LibrEduc/RobotBlocs/Projets_complets/v2020-2021/RobotTraceur1 - Pierre Gautier  - Simon Le Moal - Armand Racine  - Gwen Berrou/brainstorming/Croquis Option 2.pdf

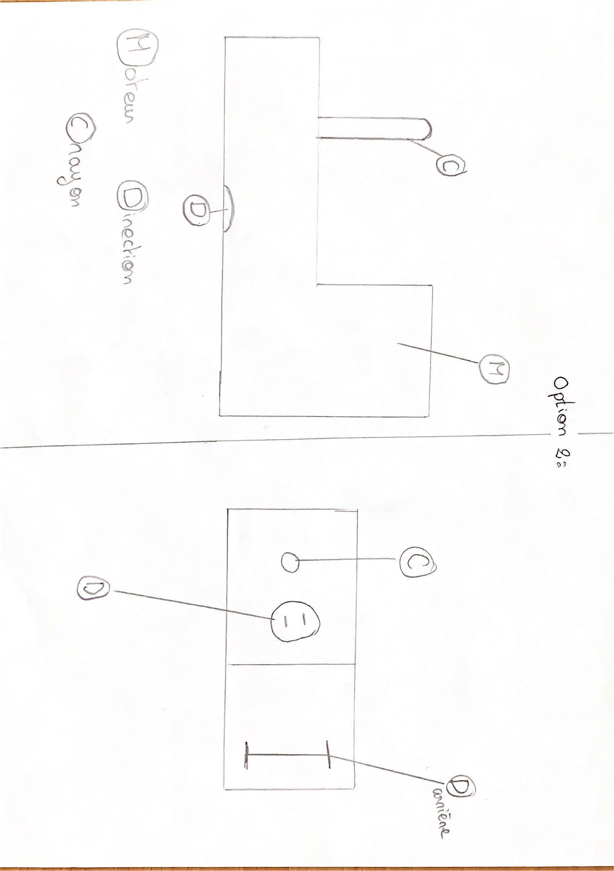
[picture p103: page 1]
