LibrEduc/RobotBlocs/Besoin_prof/SIN_ITEC_Livet_RobotBlocs_2020_uc.jpg

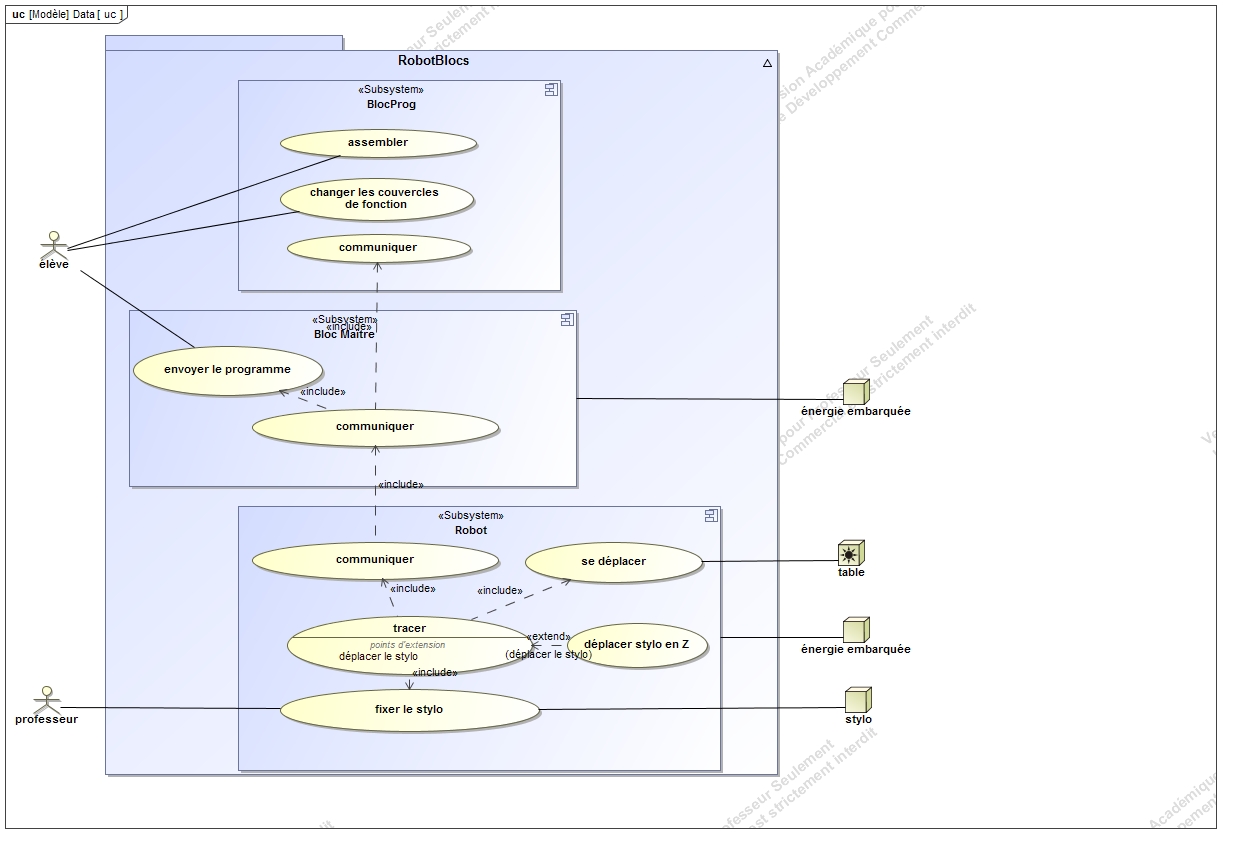
Besoin_prof/SIN_ITEC_Livet_RobotBlocs_2020_uc.jpg
