LibrEduc/RobotBlocs/Electronique/protoprof/CARTE BLOC SLAVE.png

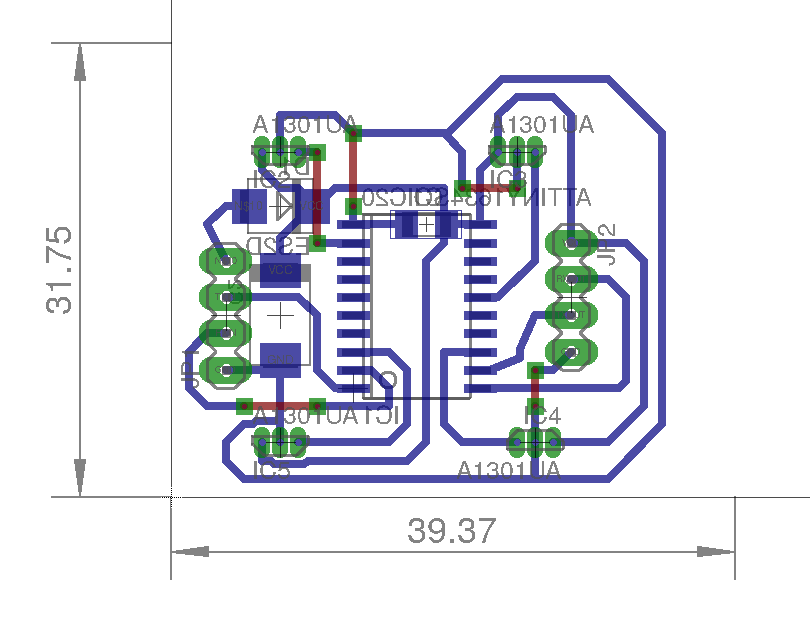
Electronique/protoprof/CARTE BLOC SLAVE.png
