LibrEduc/RobotBlocs/Electronique/protoprof/carte blocslave.png

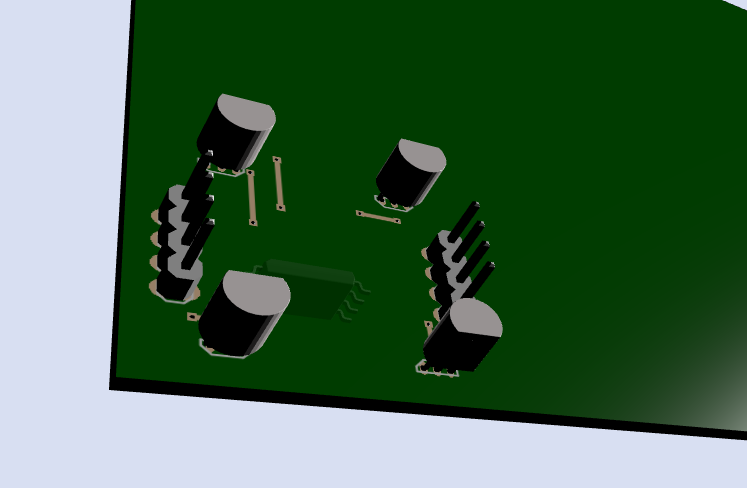
Electronique/protoprof/carte blocslave.png
