LibrEduc/RobotBlocs/Electronique/SIN_2016-2017/07_12_16 Idée RS232 cablage.png

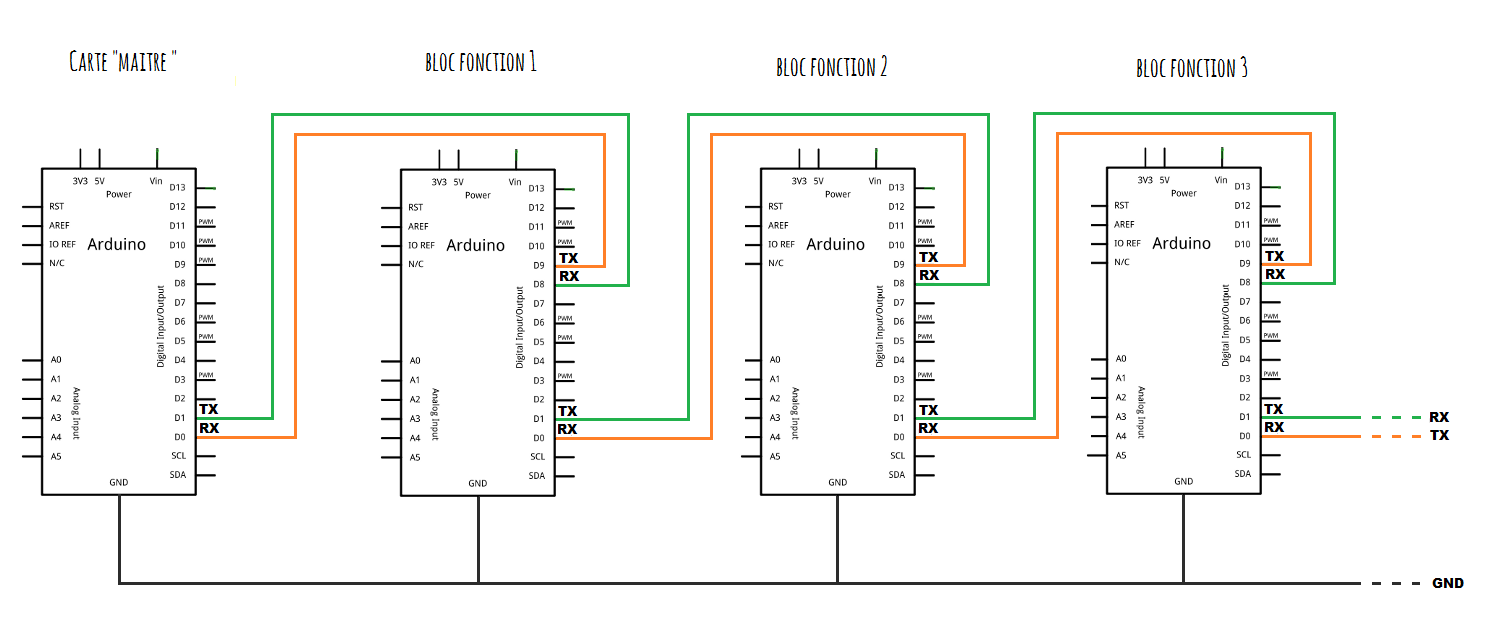
Electronique/SIN_2016-2017/07_12_16 Idée RS232 cablage.png
