LibrEduc/RobotBlocs/Electronique/SIN_2016-2017/09_12_16 Algorithme 2 RS232.png

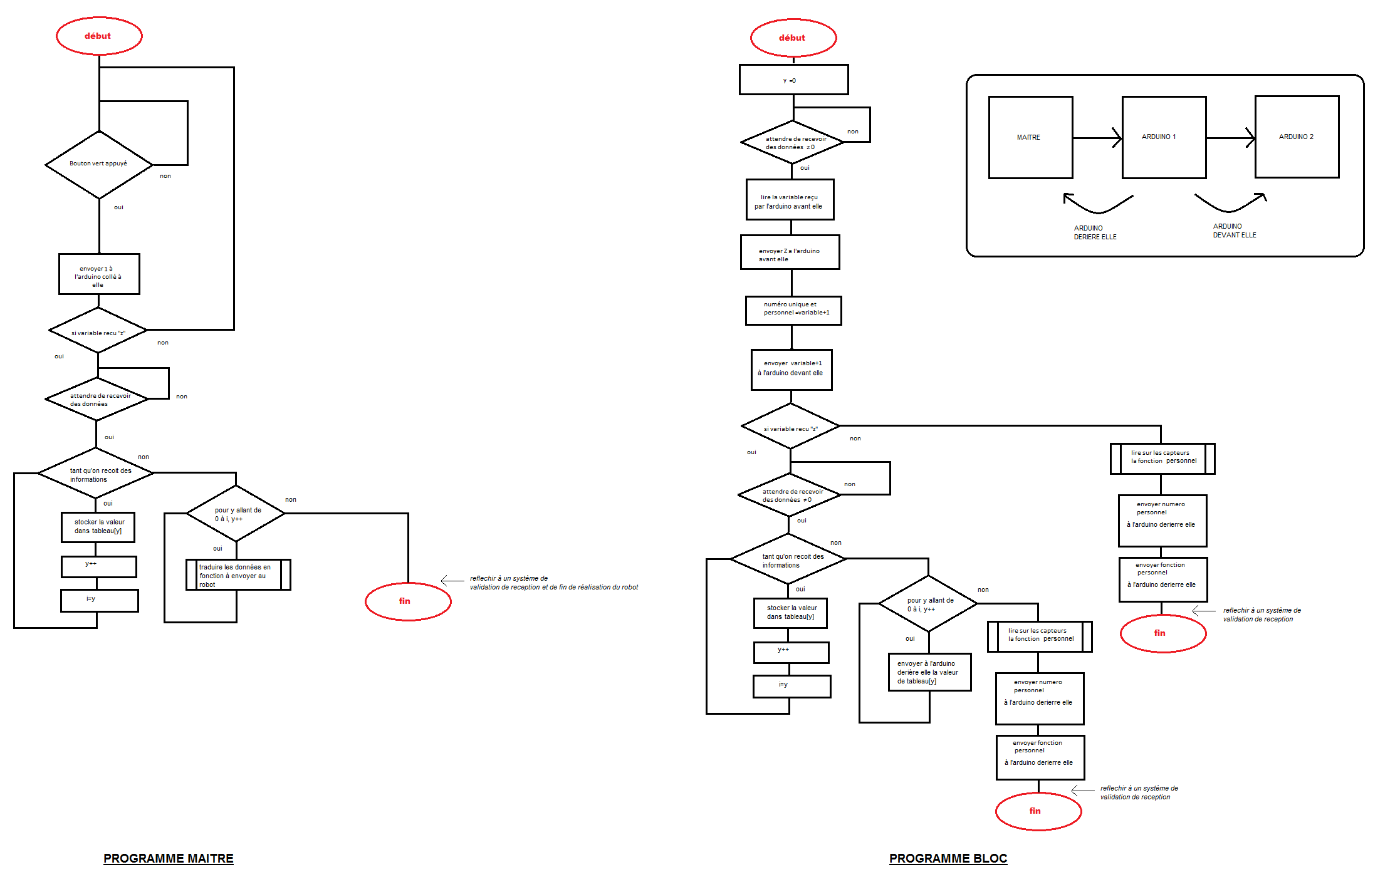
Electronique/SIN_2016-2017/09_12_16 Algorithme 2 RS232.png
