LibrEduc/RobotBlocs/Electronique/SIN_2016-2017/bloc-maitre.png

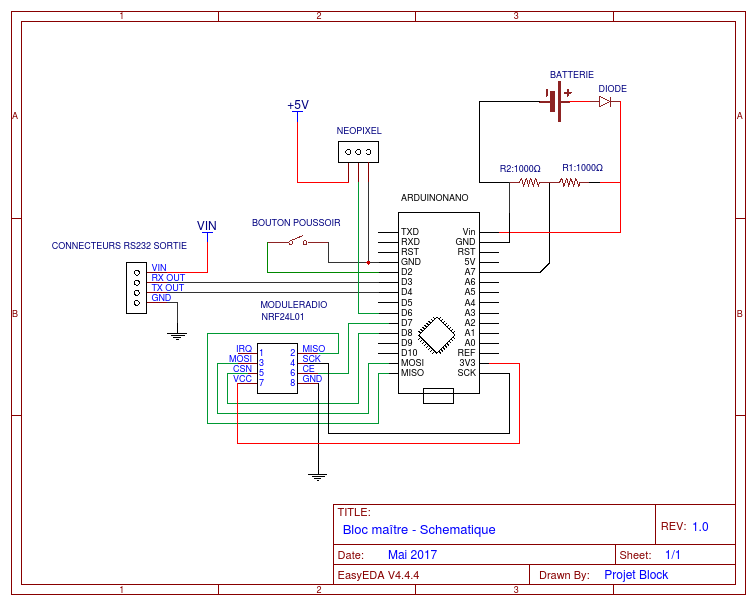
Electronique/SIN_2016-2017/bloc-maitre.png
