LibrEduc/RobotBlocs/Electronique/SIN_2016-2017/capture 1.PNG

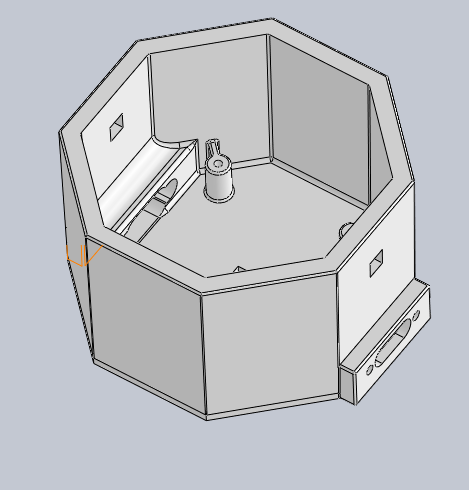
Electronique/SIN_2016-2017/capture 1.PNG
