LibrEduc/RobotBlocs/Electronique/SIN_2016-2017/Capture (1).PNG

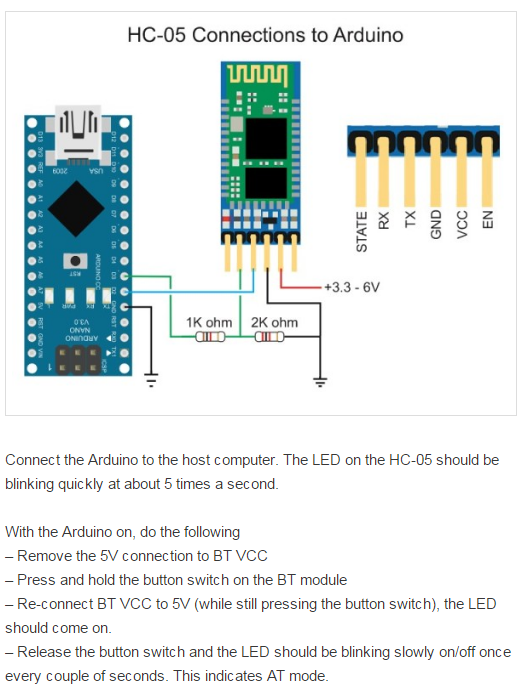
Electronique/SIN_2016-2017/Capture (1).PNG
