LibrEduc/RobotBlocs/Electronique/SIN_2016-2017/Capture.PNG

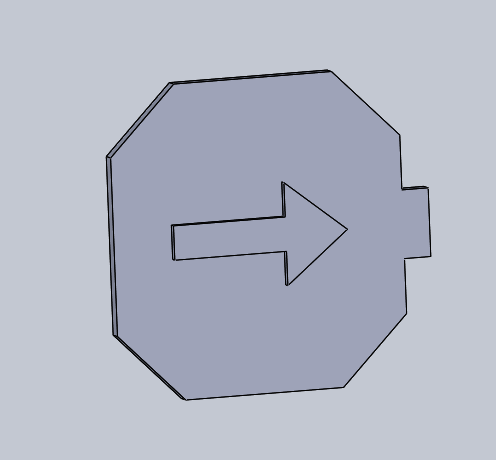
Electronique/SIN_2016-2017/Capture.PNG
