LibrEduc/RobotBlocs/Electronique/SIN_2016-2017/CODE MODULE RADIO/Captdddure.PNG

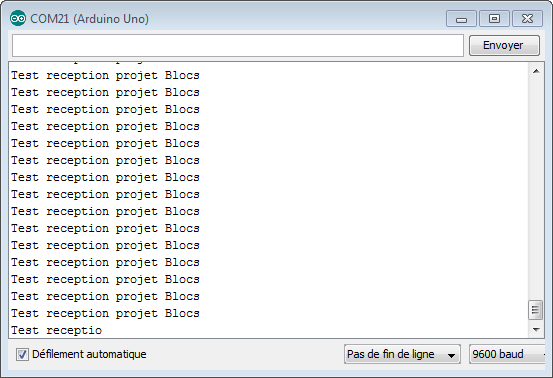
Electronique/SIN_2016-2017/CODE MODULE RADIO/Captdddure.PNG
