LibrEduc/RobotBlocs/Electronique/SIN_2016-2017/CODE MODULE RADIO/nrf-ardino-en.png

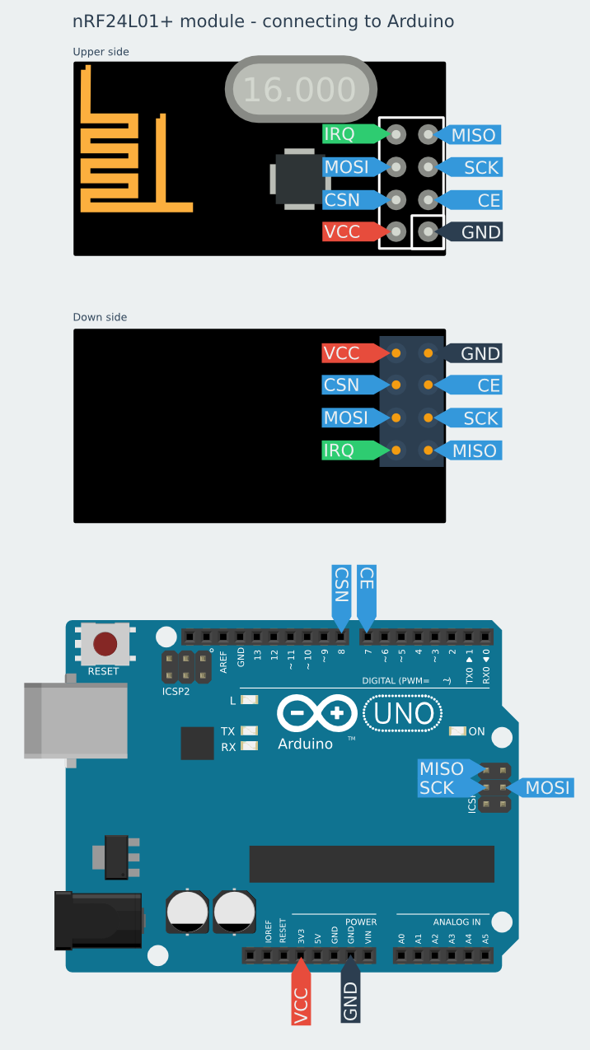
Electronique/SIN_2016-2017/CODE MODULE RADIO/nrf-ardino-en.png
