LibrEduc/RobotBlocs/Electronique/SIN_2016-2017/Effet hall/Capture.PNG

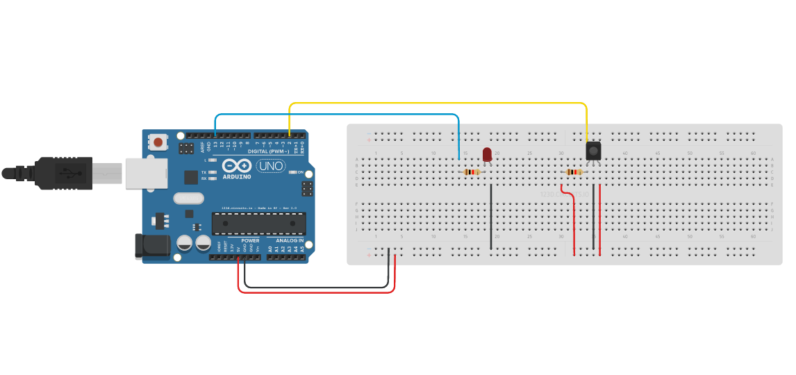
Electronique/SIN_2016-2017/Effet hall/Capture.PNG
