LibrEduc/RobotBlocs/Electronique/SIN_2016-2017/fritzing/capture bloc maitre (neopixel).PNG

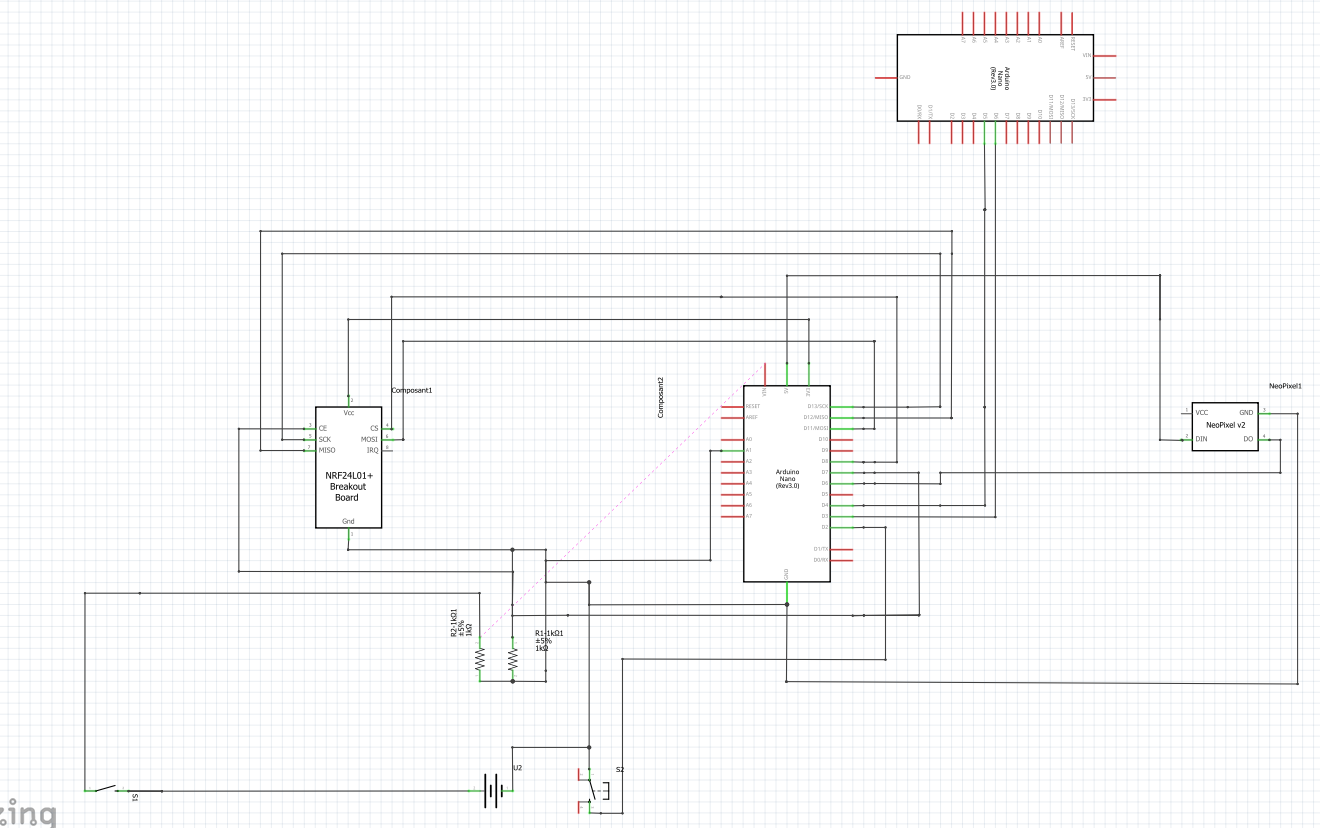
Electronique/SIN_2016-2017/fritzing/capture bloc maitre (neopixel).PNG
