LibrEduc/RobotBlocs/Electronique/SIN_2016-2017/fritzing/capture bloc maître.PNG

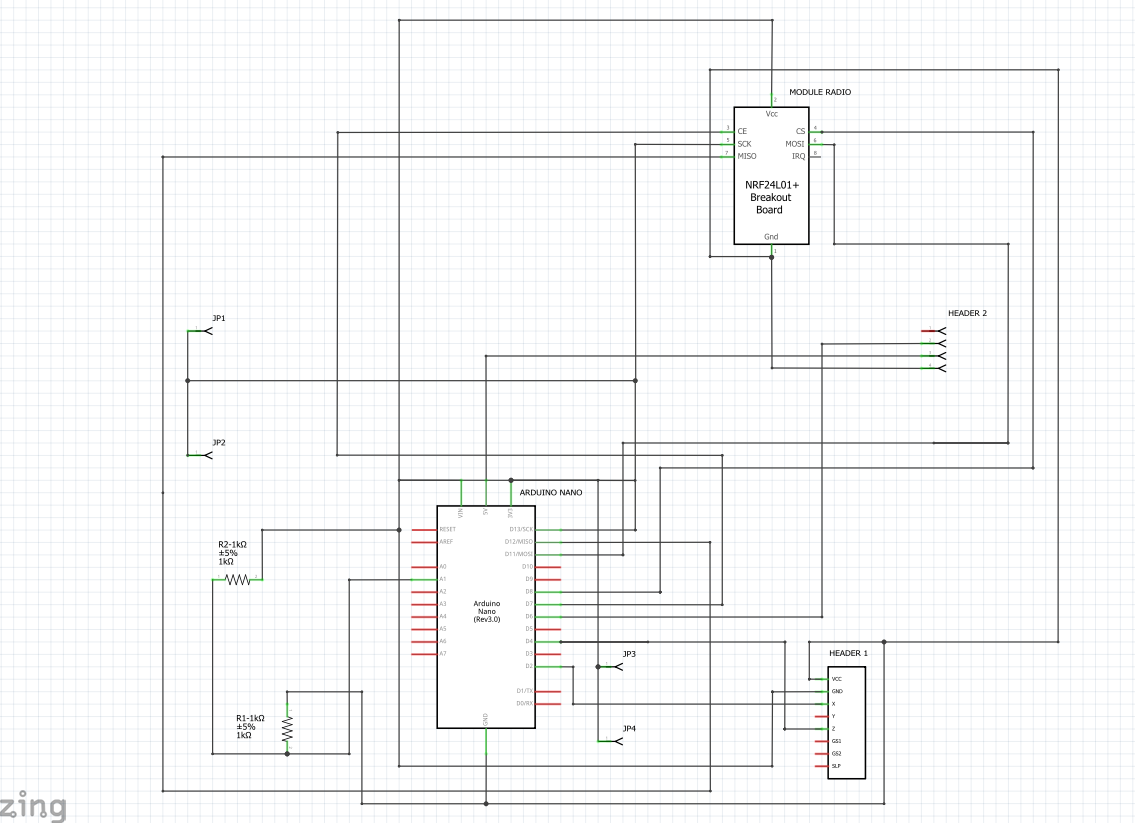
Electronique/SIN_2016-2017/fritzing/capture bloc maître.PNG
