LibrEduc/RobotBlocs/Electronique/SIN_2016-2017/fritzing/capture bloc prog.PNG

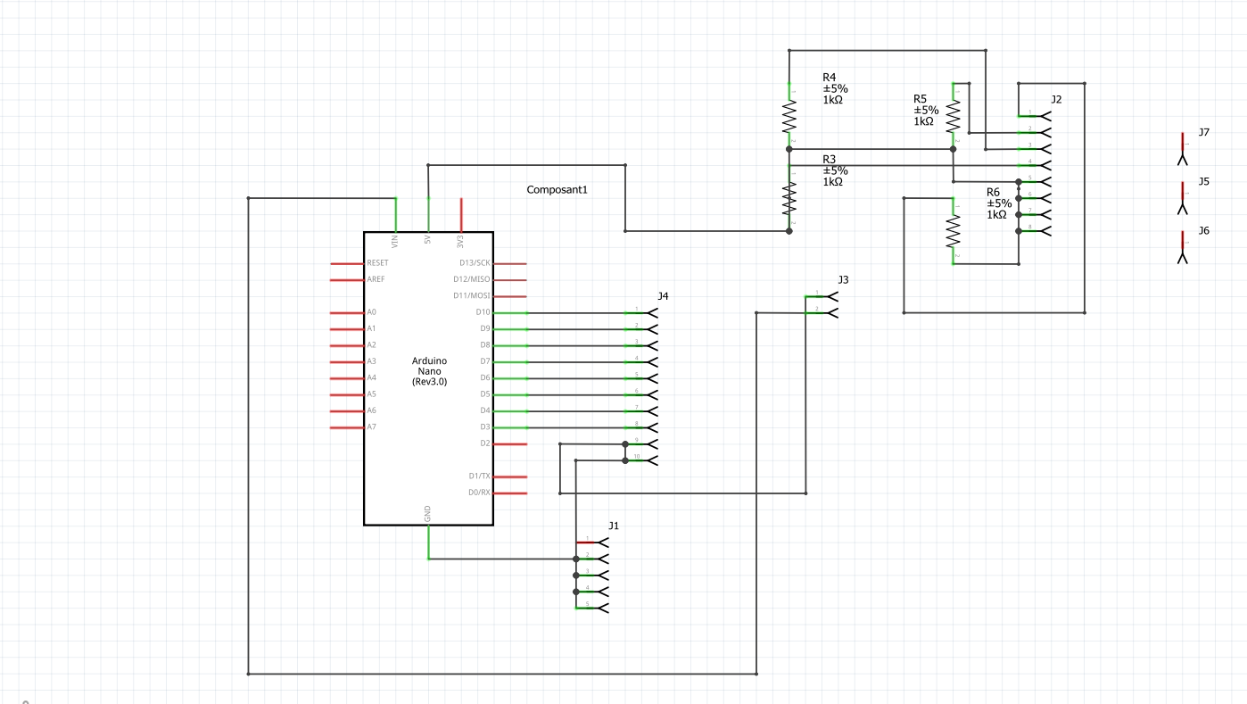
Electronique/SIN_2016-2017/fritzing/capture bloc prog.PNG
