LibrEduc/RobotBlocs/Electronique/SIN_2016-2017/fritzing/capture robot.PNG

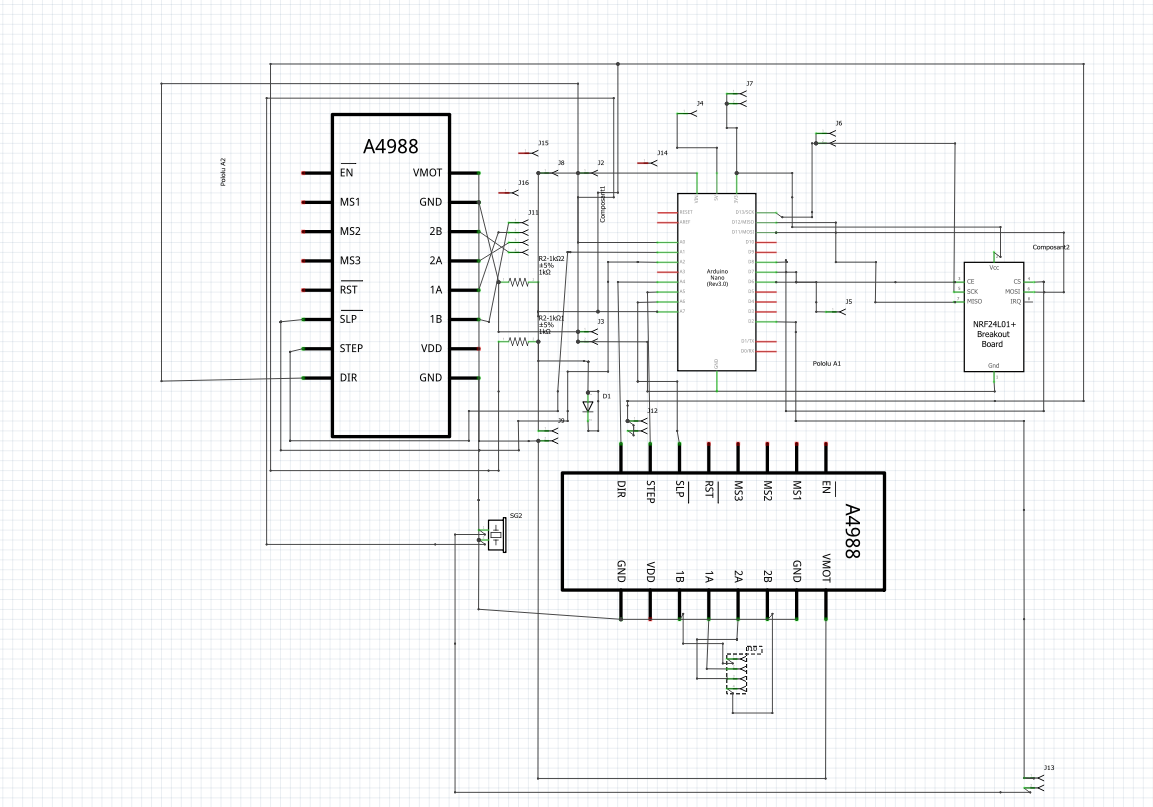
Electronique/SIN_2016-2017/fritzing/capture robot.PNG
