LibrEduc/RobotBlocs/Electronique/SIN_2016-2017/fritzing/screenshot bloc prog.PNG

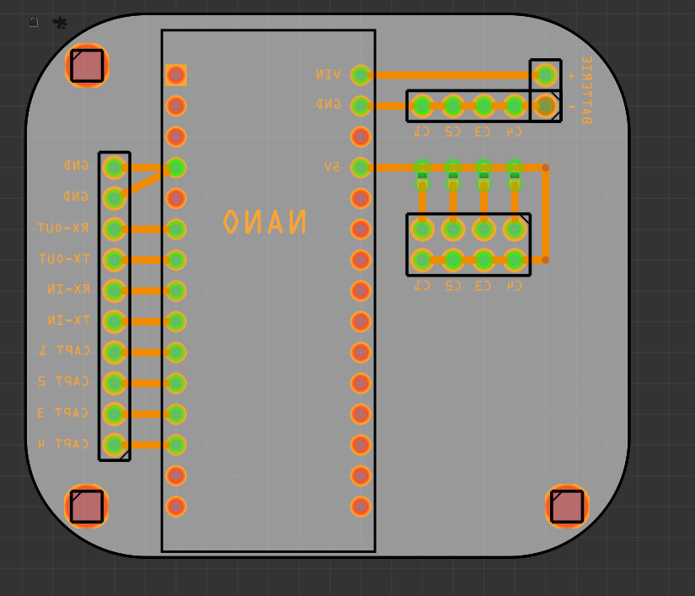
Electronique/SIN_2016-2017/fritzing/screenshot bloc prog.PNG
