LibrEduc/RobotBlocs/Electronique/SIN_2016-2017/fritzing/screenshot robot.PNG

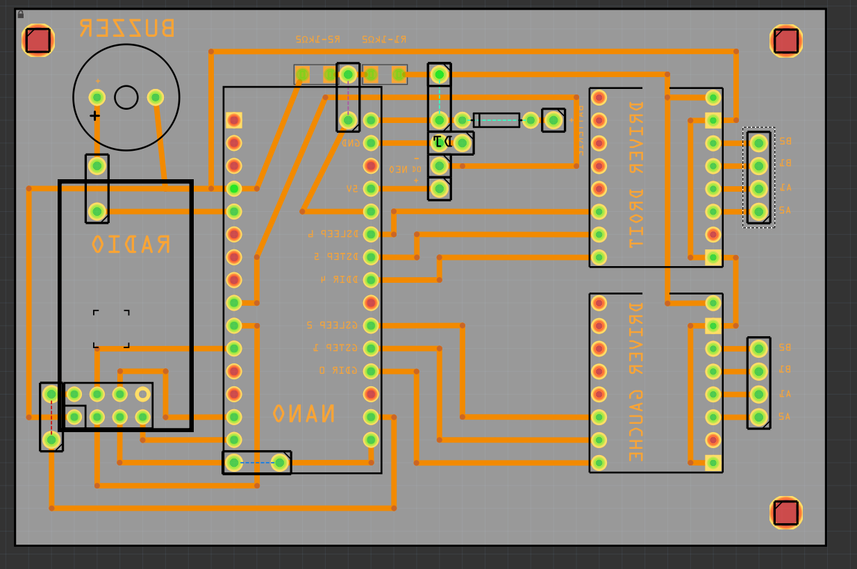
Electronique/SIN_2016-2017/fritzing/screenshot robot.PNG
