LibrEduc/RobotBlocs/Electronique/SIN_2016-2017/HTB1b1ajPXXXXXb2XVXXq6xXFXXXK.jpg

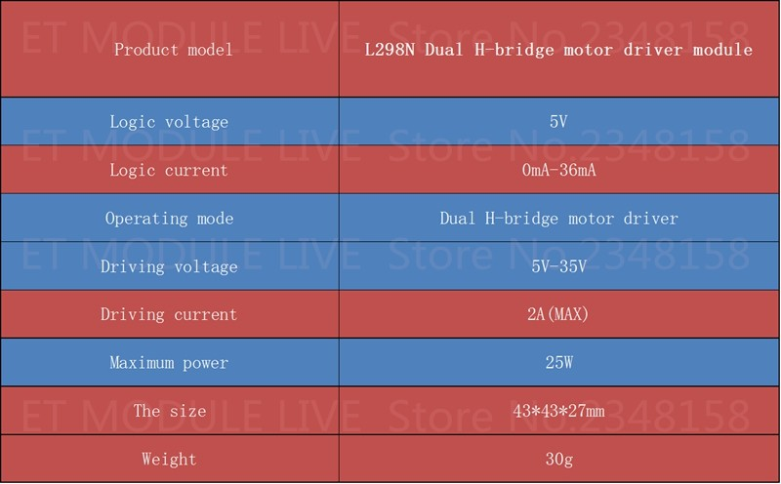
Electronique/SIN_2016-2017/HTB1b1ajPXXXXXb2XVXXq6xXFXXXK.jpg
