LibrEduc/RobotBlocs/Electronique/SIN_2016-2017/HTB1l993PXXXXXXdXVXXq6xXFXXXe.jpg

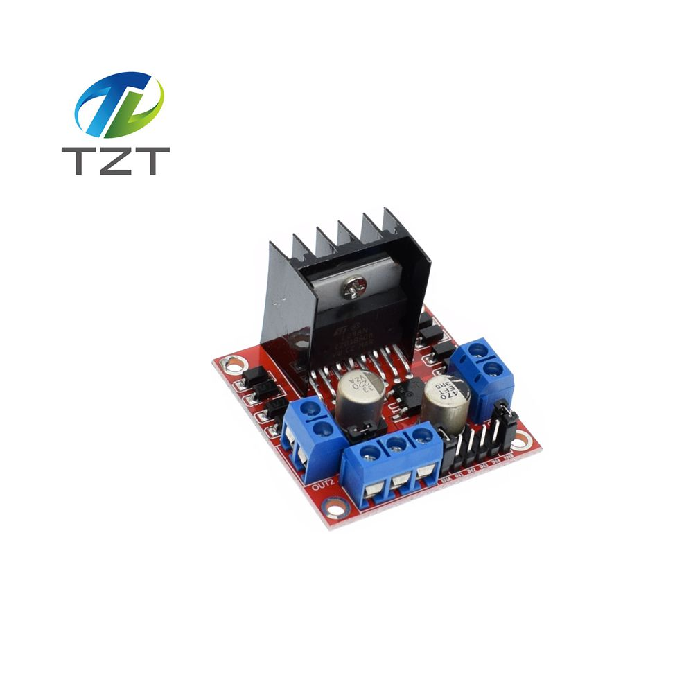
Electronique/SIN_2016-2017/HTB1l993PXXXXXXdXVXXq6xXFXXXe.jpg
