LibrEduc/RobotBlocs/Electronique/SIN_2016-2017/IMG_20170402_151555_1.jpg

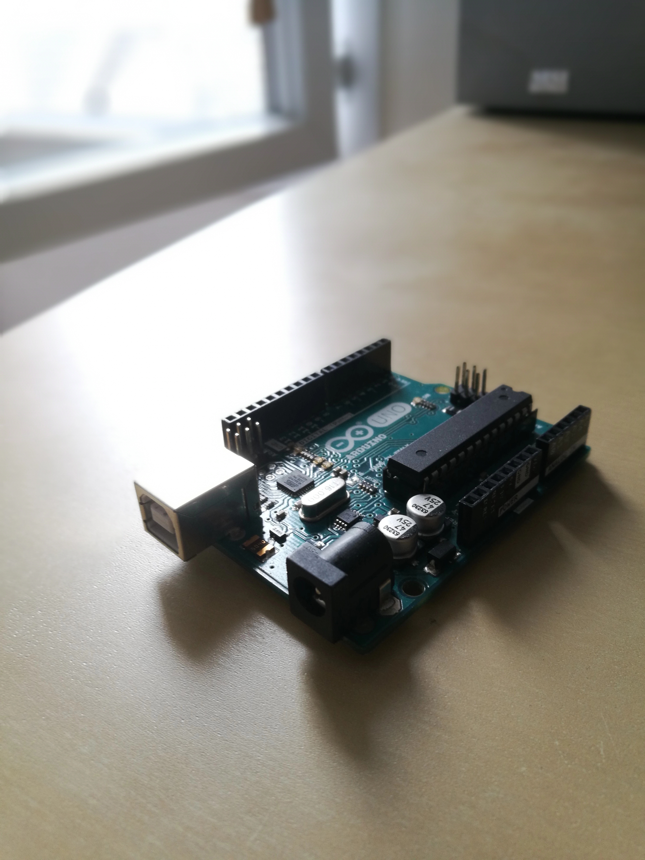
Electronique/SIN_2016-2017/IMG_20170402_151555_1.jpg
