LibrEduc/RobotBlocs/Electronique/SIN_2016-2017/L298_driver_with_stepper_motor.jpg

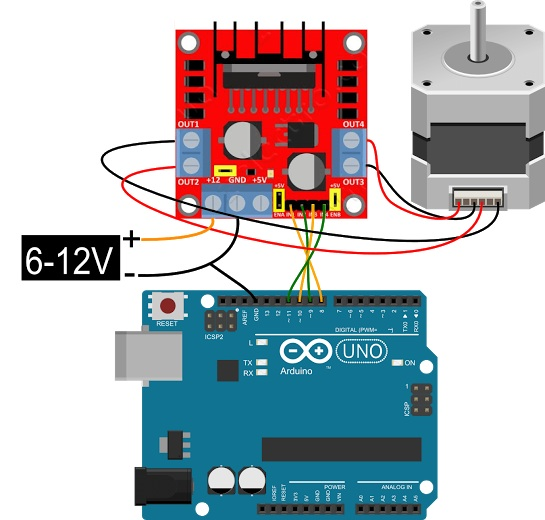
Electronique/SIN_2016-2017/L298_driver_with_stepper_motor.jpg
