LibrEduc/RobotBlocs/Electronique/SIN_2016-2017/New-Schematic-2.png

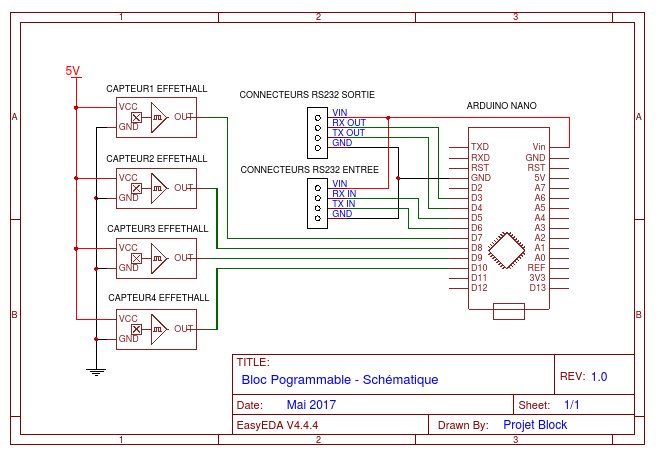
Electronique/SIN_2016-2017/New-Schematic-2.png
