LibrEduc/RobotBlocs/Electronique/SIN_2016-2017/VERSION-1.png

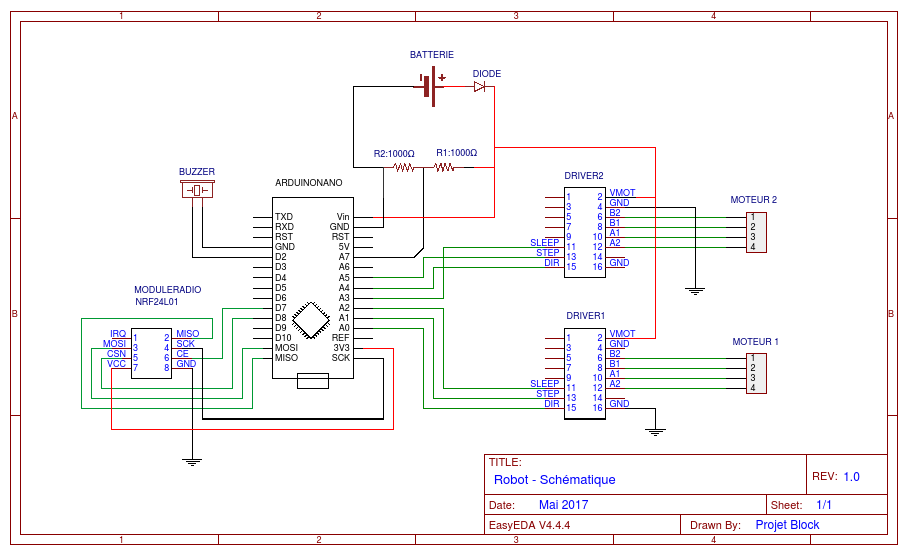
Electronique/SIN_2016-2017/VERSION-1.png
