LibrEduc/RobotBlocs/Modeles_3D/Solidworks/v2020-2021/BlocsProg1 - Jayson Dauly - Tino  Da Costa - Charles Favier/Capture Piece/esclave coter'.PNG

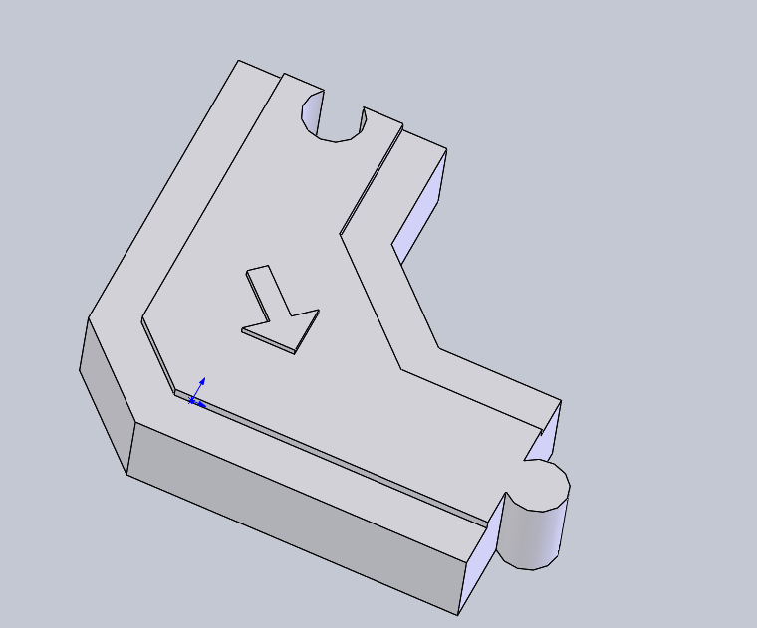
Modeles_3D/Solidworks/v2020-2021/BlocsProg1 - Jayson Dauly - Tino Da Costa - Charles Favier/Capture Piece/esclave coter'.PNG
