LibrEduc/RobotBlocs/Modeles_3D/Solidworks/v2020-2021/BlocsProg2 - Emile Mesnage - Quentin Gallot - Corentin Gloaguen/Solidworks/Simulation/Simulation Bloc esclave.PNG

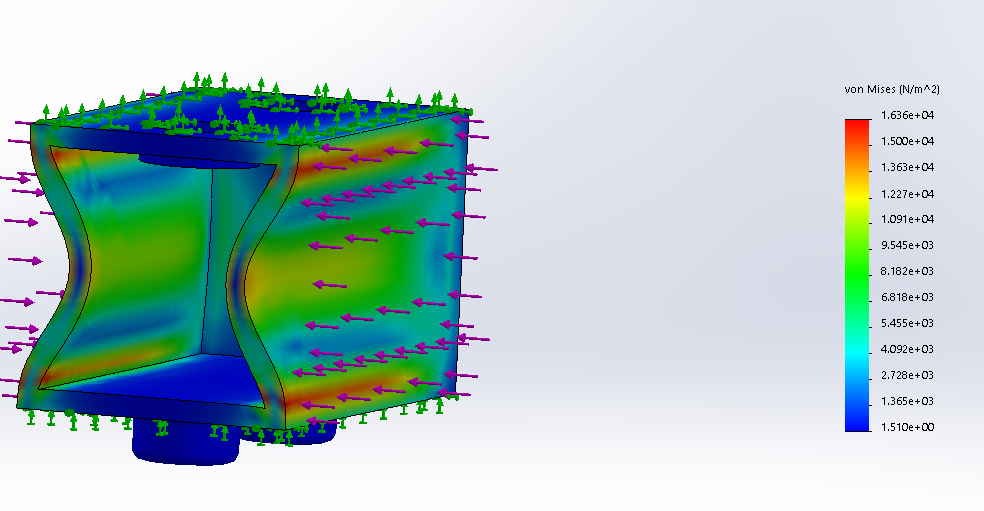
Modeles_3D/Solidworks/v2020-2021/BlocsProg2 - Emile Mesnage - Quentin Gallot - Corentin Gloaguen/Solidworks/Simulation/Simulation Bloc esclave.PNG
