LibrEduc/RobotBlocs/Modeles_3D/Solidworks/v2020-2021/BlocsProg3 - Romain Charrier - Maxime Fortune - Sylvain Chéné/piece bloc esclave.PNG

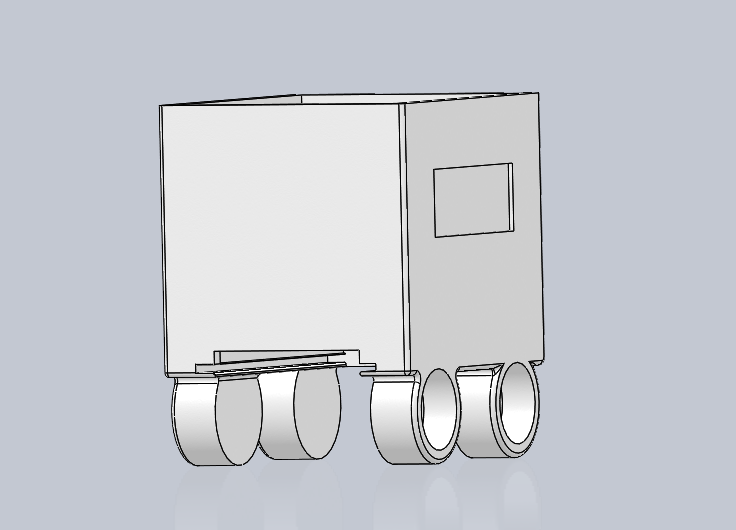
Modeles_3D/Solidworks/v2020-2021/BlocsProg3 - Romain Charrier - Maxime Fortune - Sylvain Chéné/piece bloc esclave.PNG
