LibrEduc/RobotBlocs/Modeles_3D/Solidworks/v2020-2021/BlocsProg3 - Romain Charrier - Maxime Fortune - Sylvain Chéné/piece bloc maitre.PNG

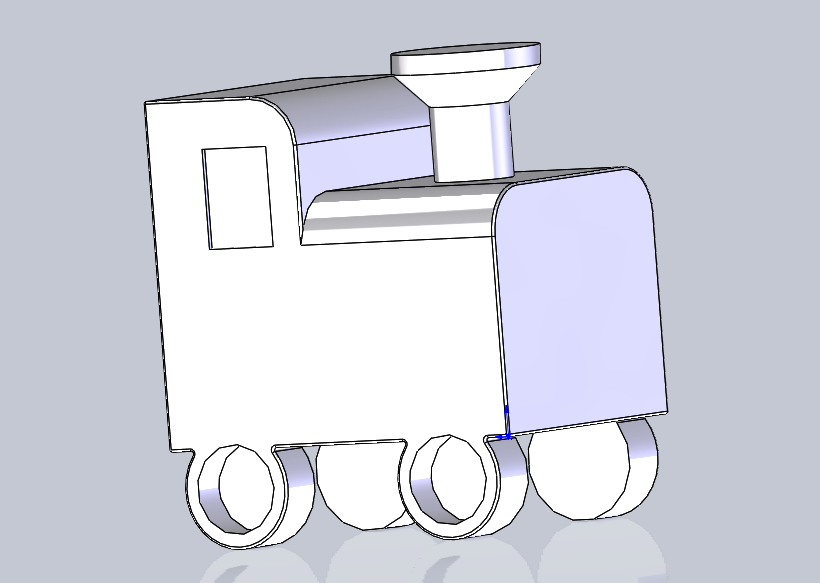
Modeles_3D/Solidworks/v2020-2021/BlocsProg3 - Romain Charrier - Maxime Fortune - Sylvain Chéné/piece bloc maitre.PNG
