LibrEduc/RobotBlocs/Photos_3D_et_fab/v2016-2017/3d robot complet.png

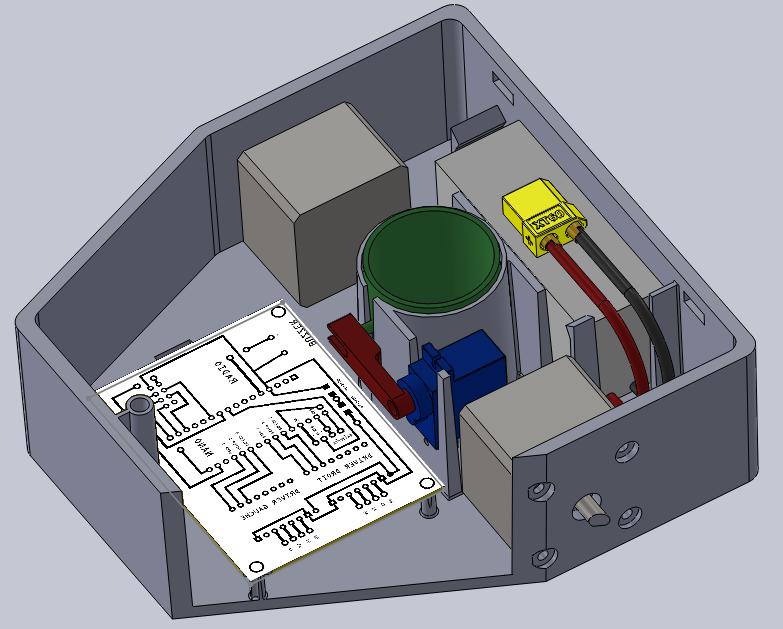
Photos_3D_et_fab/v2016-2017/3d robot complet.png
