LibrEduc/RobotBlocs/Photos_3D_et_fab/v2016-2017/20170410_140929.jpg

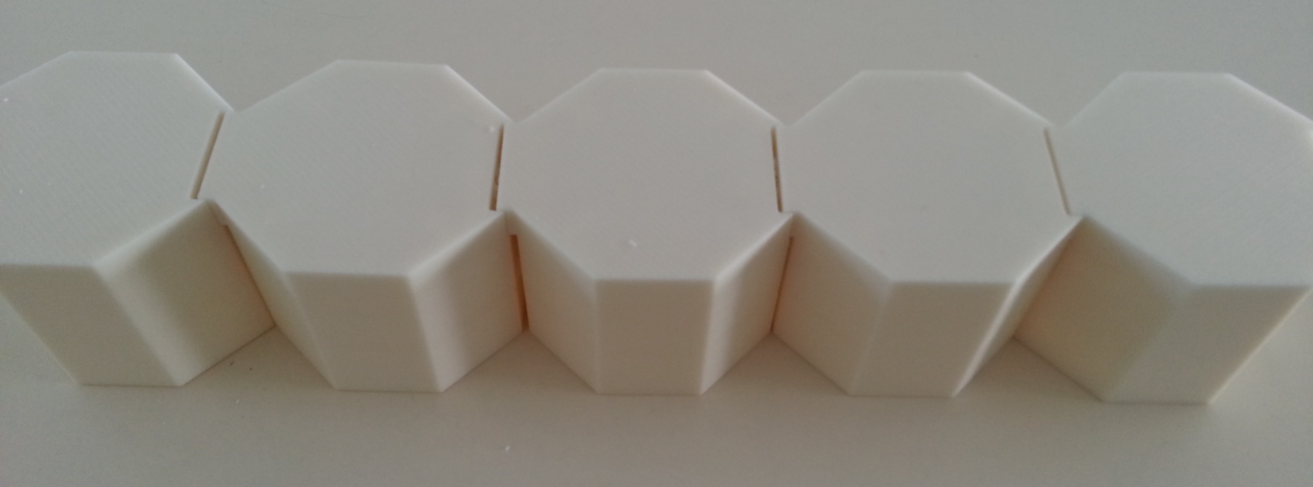
Photos_3D_et_fab/v2016-2017/20170410_140929.jpg
