LibrEduc/RobotBlocs/Photos_3D_et_fab/v2016-2017/20170412_155358.jpg

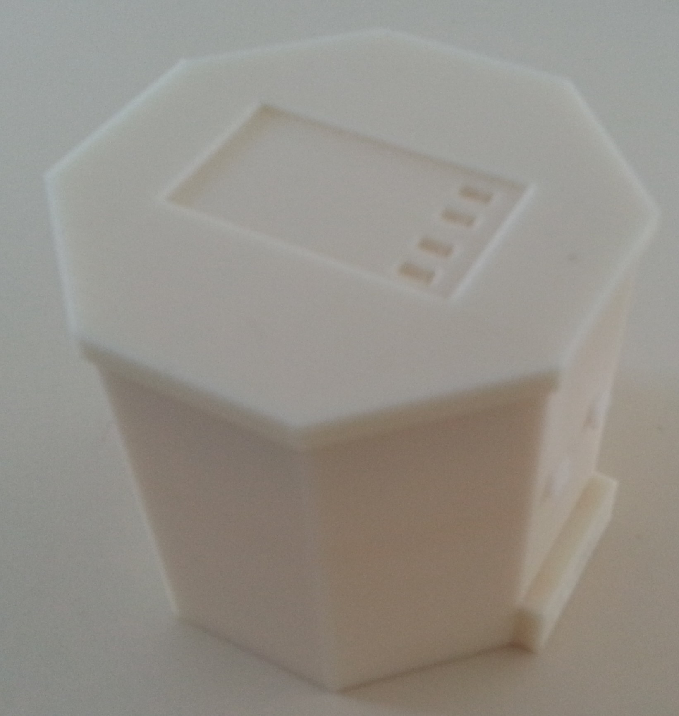
Photos_3D_et_fab/v2016-2017/20170412_155358.jpg
