LibrEduc/RobotBlocs/Photos_3D_et_fab/v2016-2017/carte robot.jpg

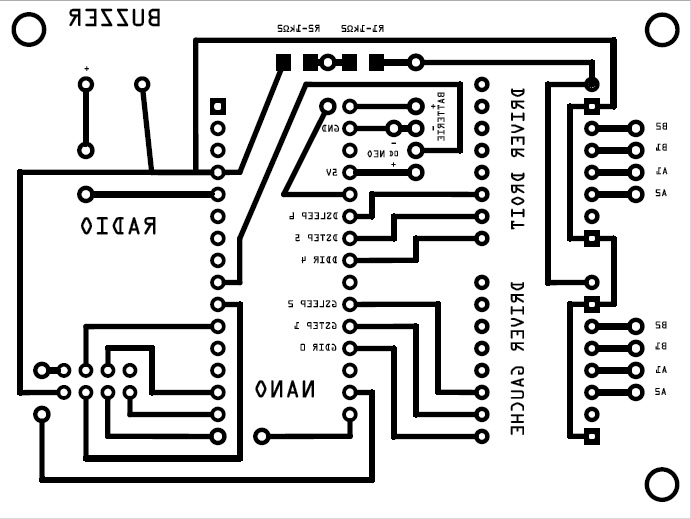
Photos_3D_et_fab/v2016-2017/carte robot.jpg
