LibrEduc/RobotBlocs/Photos_3D_et_fab/v2016-2017/CE robot.png

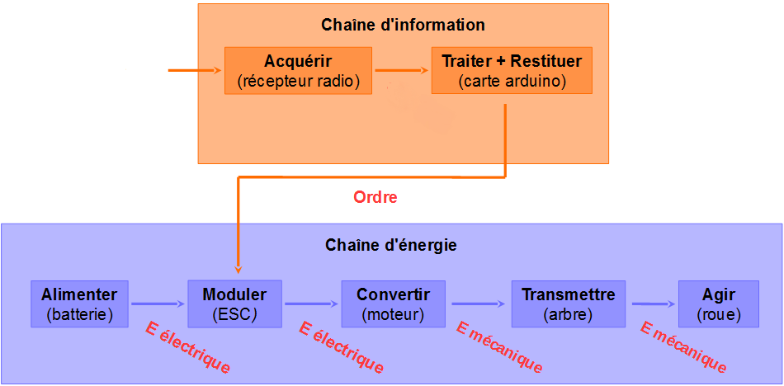
Photos_3D_et_fab/v2016-2017/CE robot.png
