LibrEduc/RobotBlocs/Photos_3D_et_fab/v2016-2017/découpeuse.jpg

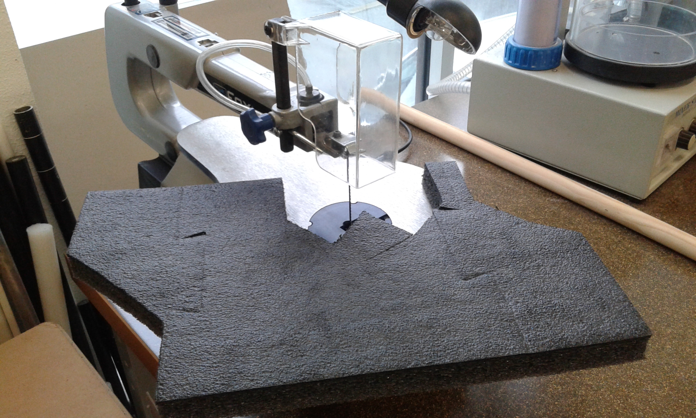
Photos_3D_et_fab/v2016-2017/découpeuse.jpg
