LibrEduc/RobotBlocs/Photos_3D_et_fab/v2016-2017/FD 2.jpg

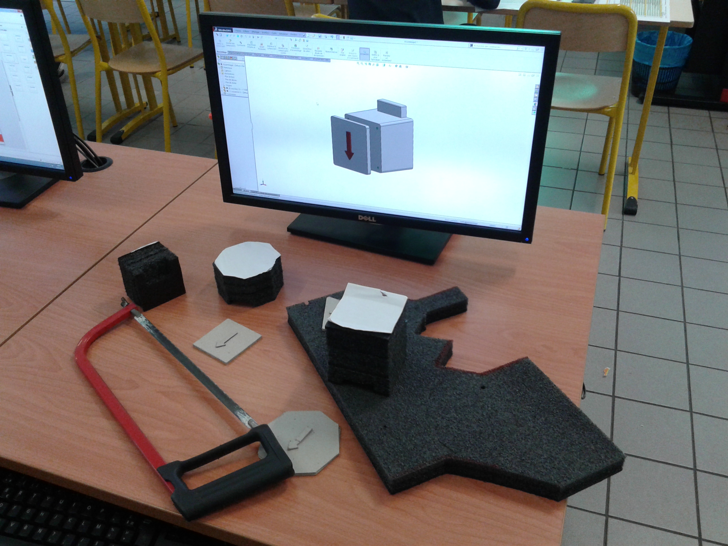
Photos_3D_et_fab/v2016-2017/FD 2.jpg
