LibrEduc/RobotBlocs/Photos_3D_et_fab/v2016-2017/FD conception.jpg

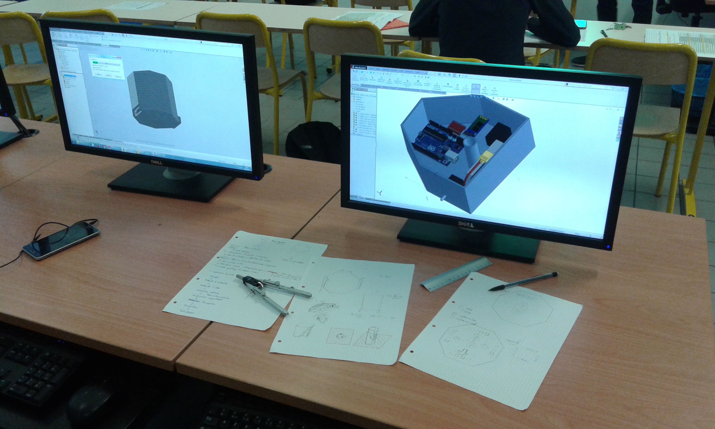
Photos_3D_et_fab/v2016-2017/FD conception.jpg
