LibrEduc/RobotBlocs/Photos_3D_et_fab/v2016-2017/Image 002.jpg

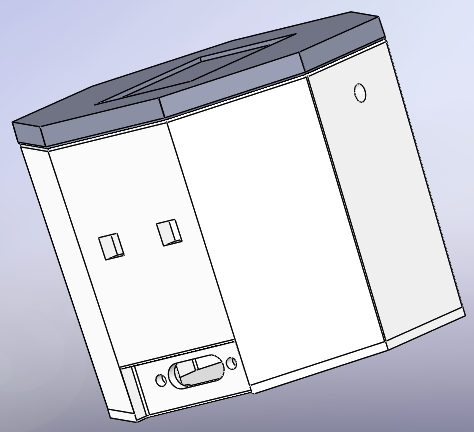
Photos_3D_et_fab/v2016-2017/Image 002.jpg
