LibrEduc/RobotBlocs/Photos_3D_et_fab/v2016-2017/Image 003.jpg

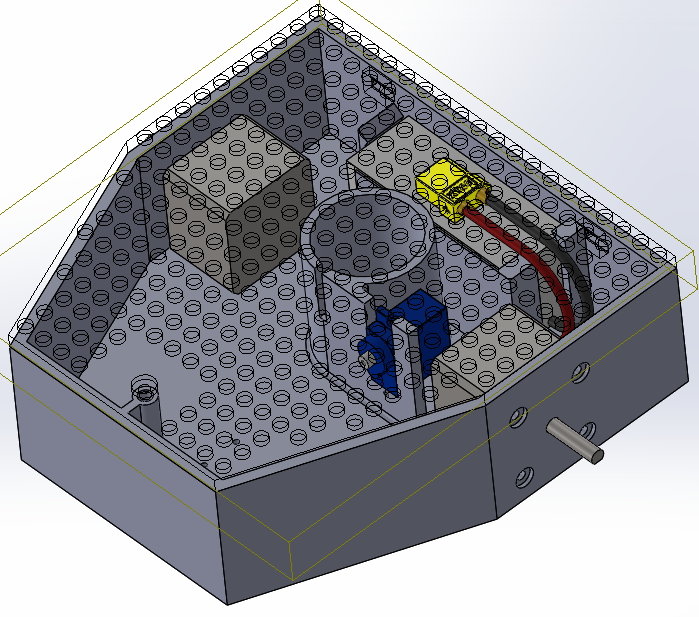
Photos_3D_et_fab/v2016-2017/Image 003.jpg
