LibrEduc/RobotBlocs/Photos_3D_et_fab/v2016-2017/IMG_20170514_171410.jpg

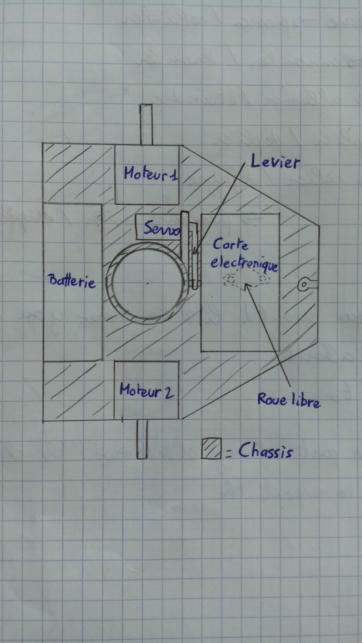
Photos_3D_et_fab/v2016-2017/IMG_20170514_171410.jpg
