LibrEduc/RobotBlocs/Photos_3D_et_fab/v2016-2017/prototypes blocs + couvercles.jpg

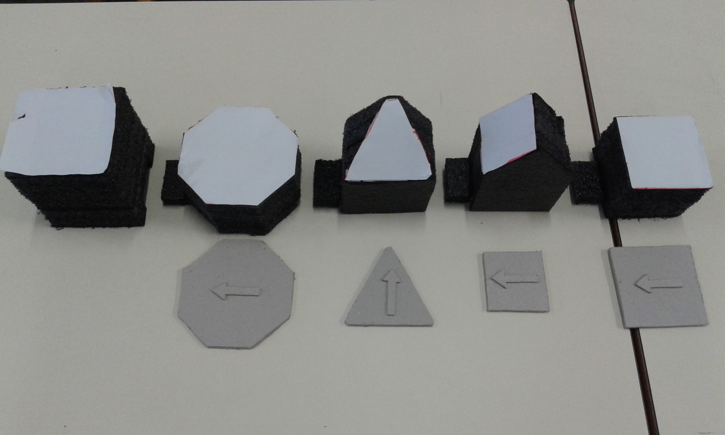
Photos_3D_et_fab/v2016-2017/prototypes blocs + couvercles.jpg
