LibrEduc/RobotBlocs/Photos_3D_et_fab/v2016-2017/RDM bloc prog.png

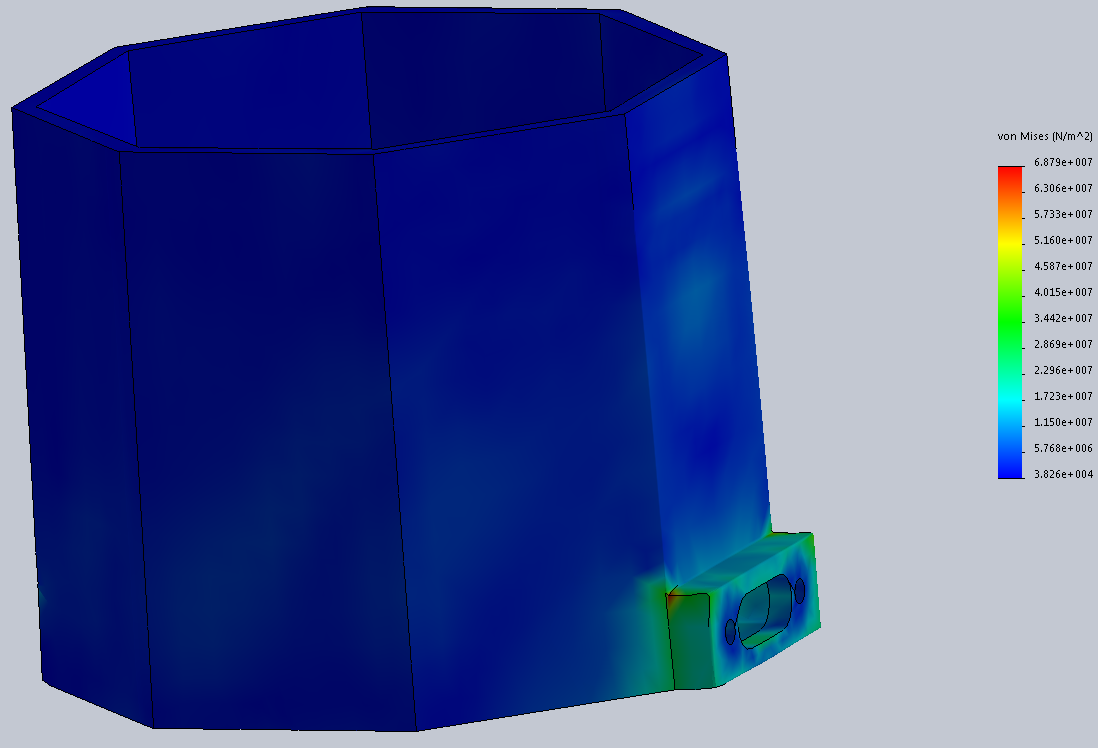
Photos_3D_et_fab/v2016-2017/RDM bloc prog.png
