LibrEduc/RobotBlocs/Photos_3D_et_fab/v2016-2017/schéma solution stylo finale.jpg

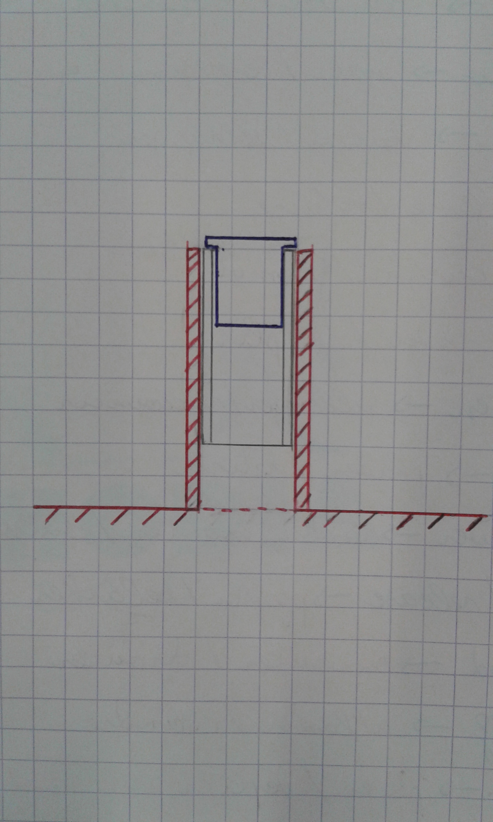
Photos_3D_et_fab/v2016-2017/schéma solution stylo finale.jpg
