LibrEduc/RobotBlocs/Photos_3D_et_fab/v2016-2017/schémas blocs prog.jpg

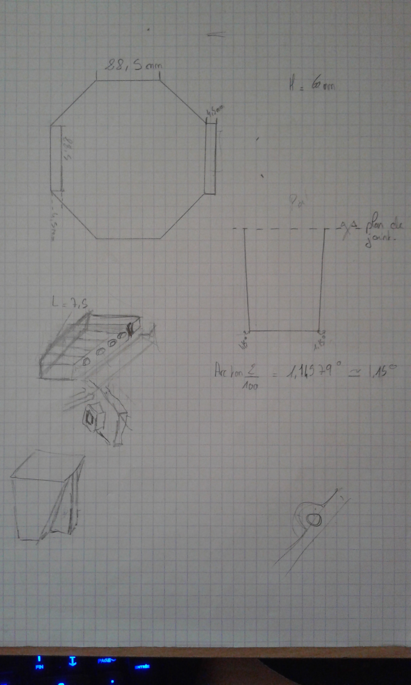
Photos_3D_et_fab/v2016-2017/schémas blocs prog.jpg
