LibrEduc/RobotBlocs/Photos_3D_et_fab/v2016-2017/scéma stylo.jpg

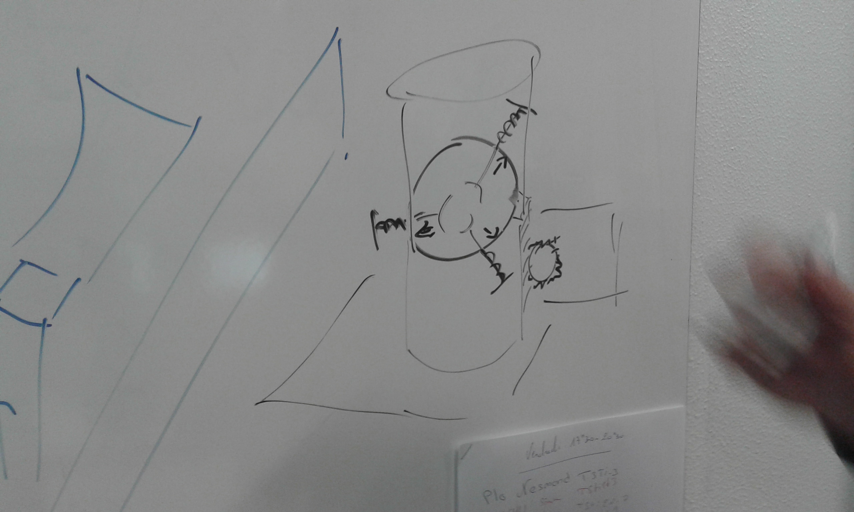
Photos_3D_et_fab/v2016-2017/scéma stylo.jpg
