LibrEduc/RobotBlocs/Photos_3D_et_fab/v2016-2017/Stylo v3d.jpg

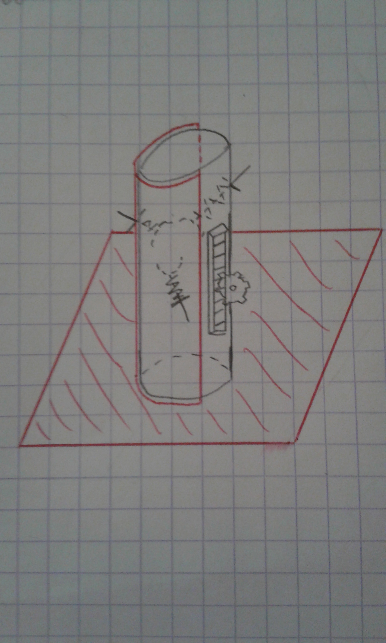
Photos_3D_et_fab/v2016-2017/Stylo v3d.jpg
