LibrEduc/RobotBlocs/Photos_3D_et_fab/v2016-2017/Stylo vdessus.jpg

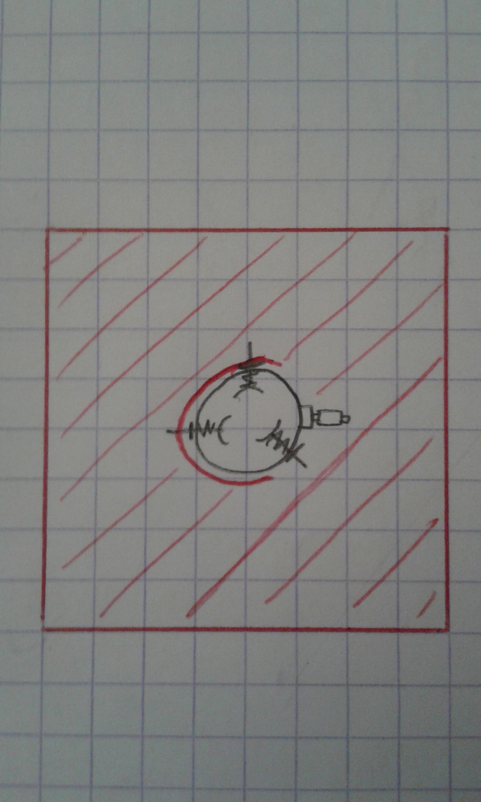
Photos_3D_et_fab/v2016-2017/Stylo vdessus.jpg
