LibrEduc/RobotBlocs/Photos_3D_et_fab/v2018-2019/Bloc-maître/Capture1.PNG

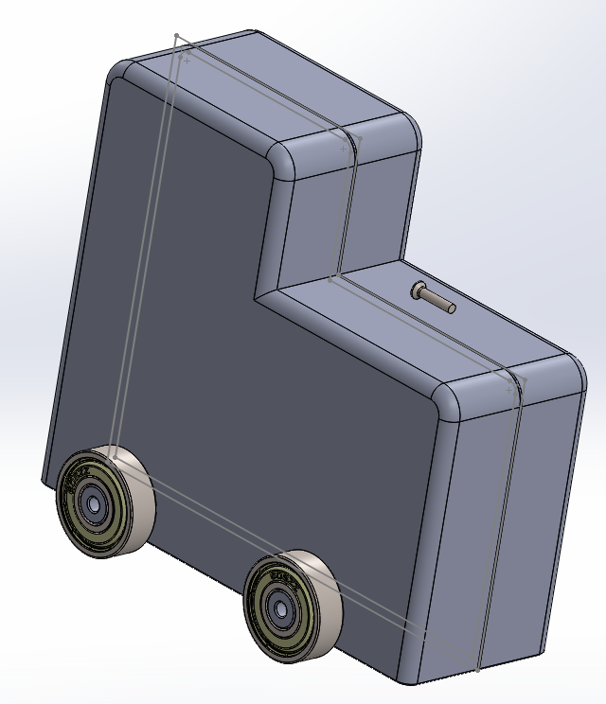
Photos_3D_et_fab/v2018-2019/Bloc-maître/Capture1.PNG
