LibrEduc/RobotBlocs/Photos_3D_et_fab/v2018-2019/Bloc-maître/Capture2.PNG

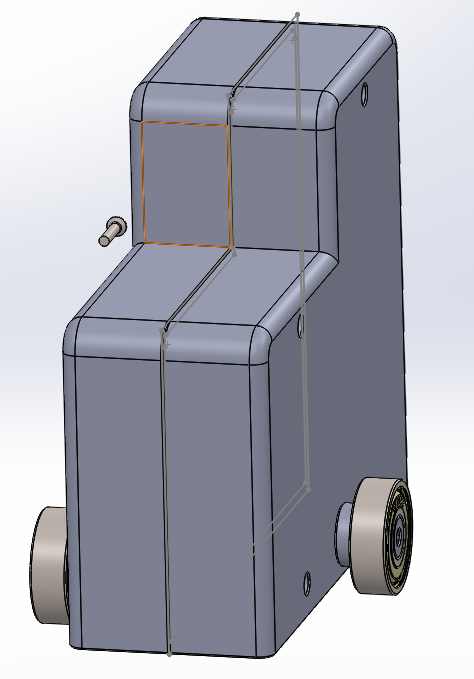
Photos_3D_et_fab/v2018-2019/Bloc-maître/Capture2.PNG
