LibrEduc/RobotBlocs/Photos_3D_et_fab/v2018-2019/Bloc-Prog/Capture3.PNG

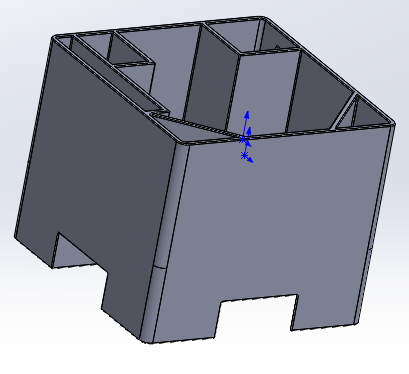
Photos_3D_et_fab/v2018-2019/Bloc-Prog/Capture3.PNG
