LibrEduc/RobotBlocs/Photos_3D_et_fab/v2018-2019/Photo vue face.PNG

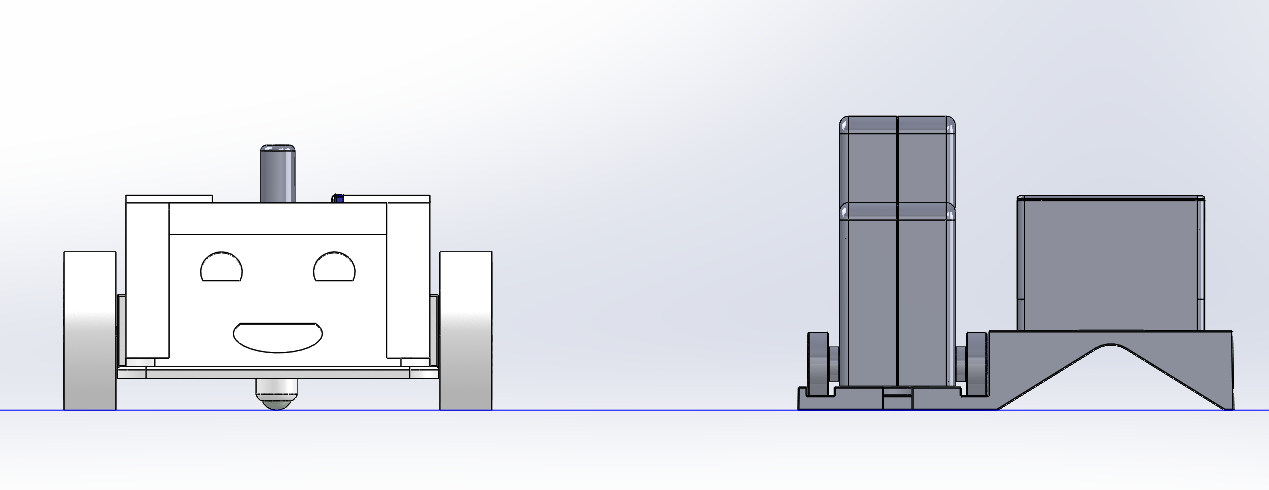
Photos_3D_et_fab/v2018-2019/Photo vue face.PNG
