LibrEduc/RobotBlocs/Photos_3D_et_fab/v2018-2019/Photo vue iso.PNG

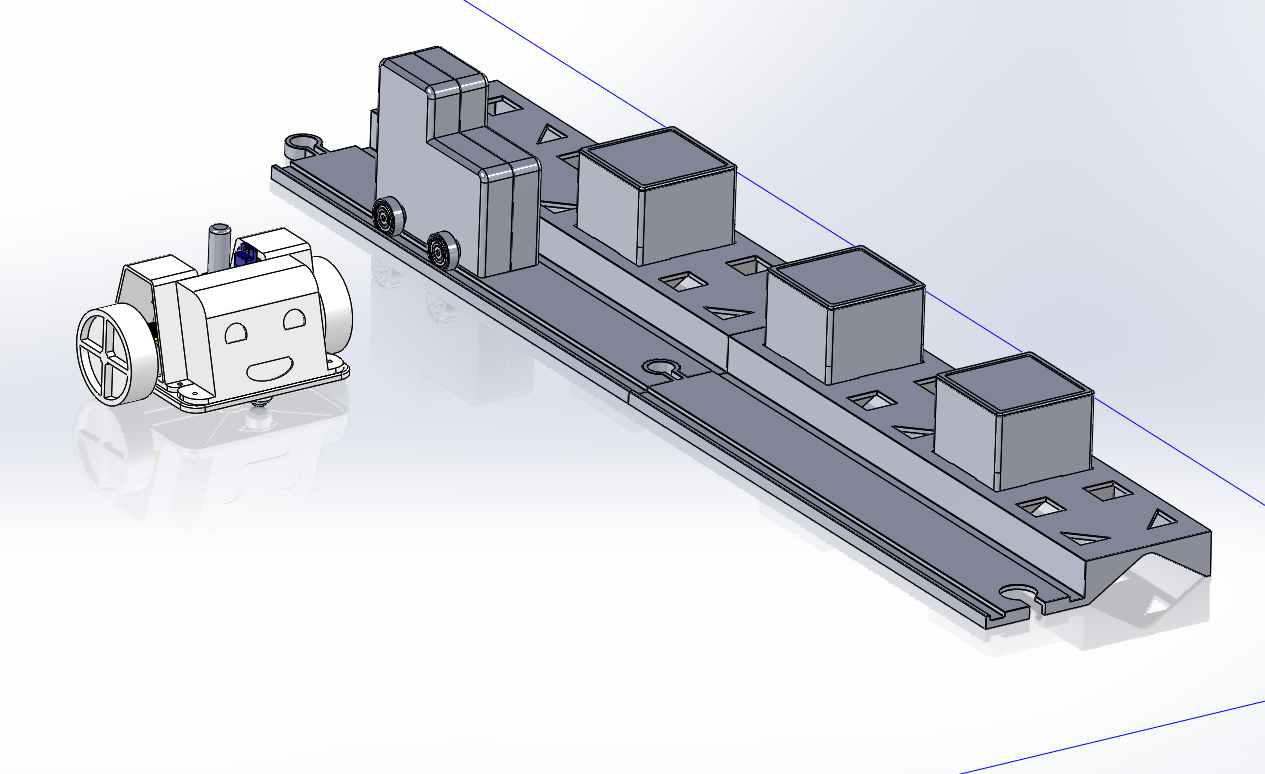
Photos_3D_et_fab/v2018-2019/Photo vue iso.PNG
