LibrEduc/RobotBlocs/Photos_3D_et_fab/v2018-2019/Rail/injection temps de remplissage.PNG

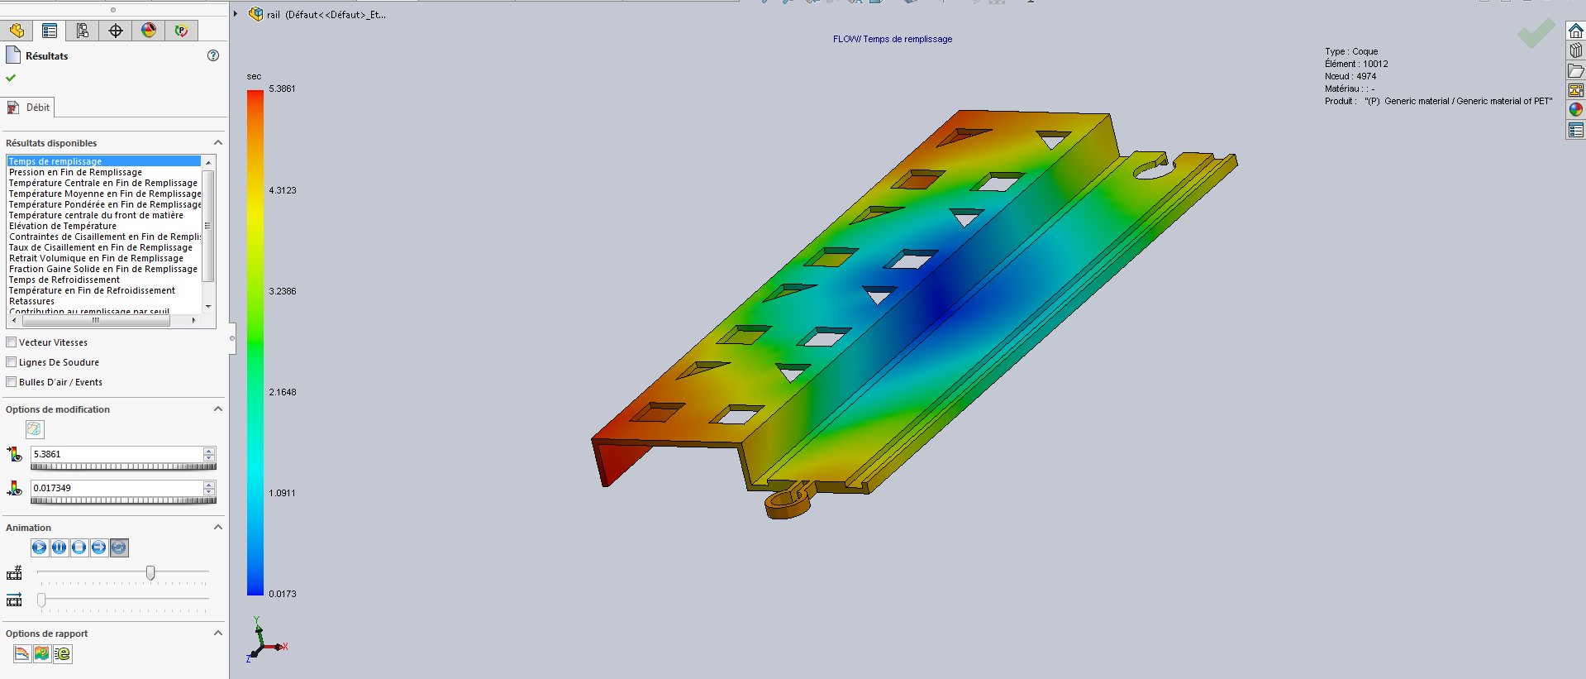
Photos_3D_et_fab/v2018-2019/Rail/injection temps de remplissage.PNG
