LibrEduc/RobotBlocs/Photos_3D_et_fab/v2018-2019/Robot/Dessous.PNG

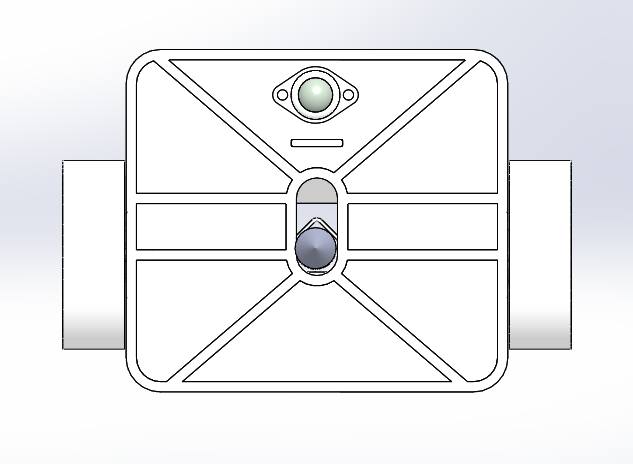
Photos_3D_et_fab/v2018-2019/Robot/Dessous.PNG
