LibrEduc/RobotBlocs/Photos_3D_et_fab/v2018-2019/Robot/Simulation chute/Déformation.PNG

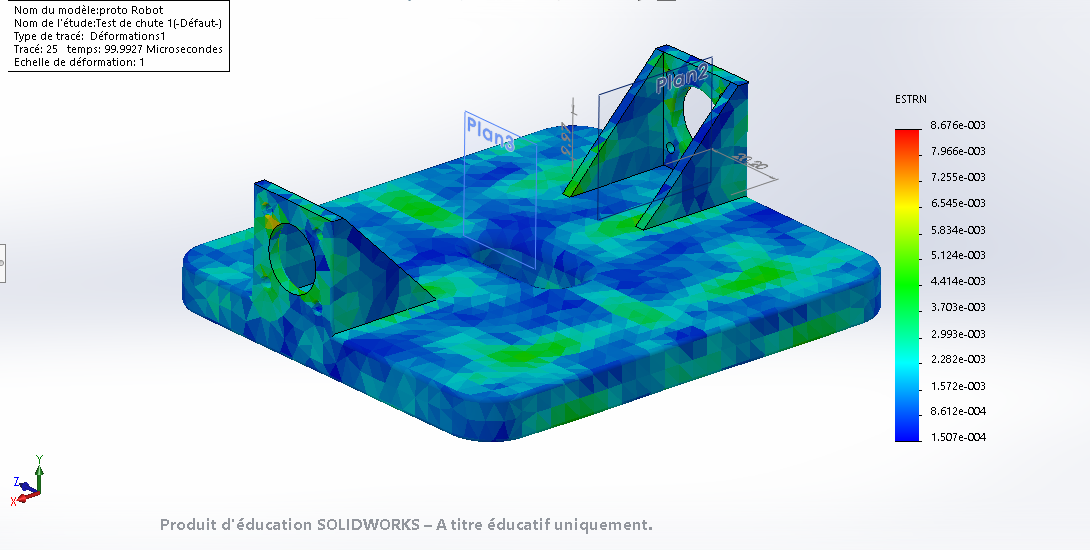
Photos_3D_et_fab/v2018-2019/Robot/Simulation chute/Déformation.PNG
