LibrEduc/RobotBlocs/Photos_3D_et_fab/v2019-2020/Capture rdm support.PNG

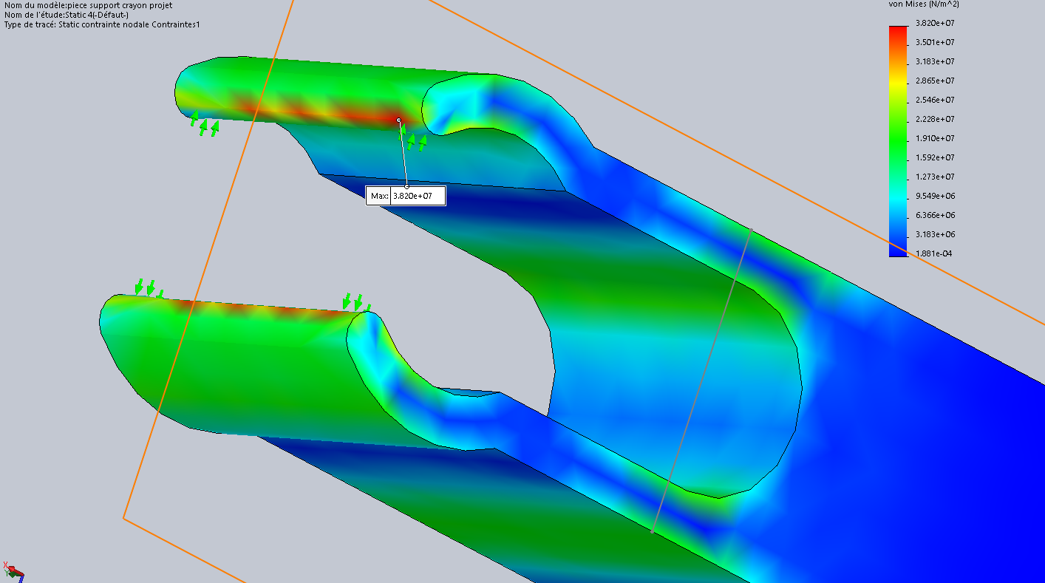
Photos_3D_et_fab/v2019-2020/Capture rdm support.PNG
