LibrEduc/RobotBlocs/Photos_3D_et_fab/v2019-2020/ccapture materiaux.png

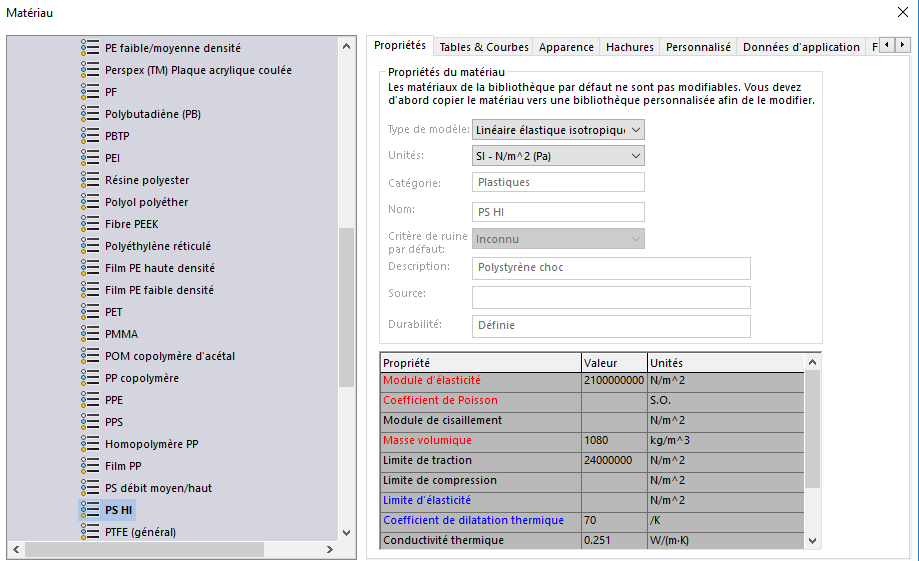
Photos_3D_et_fab/v2019-2020/ccapture materiaux.png
