LibrEduc/RobotBlocs/Photos_3D_et_fab/v2019-2020/Image Bloc.PNG

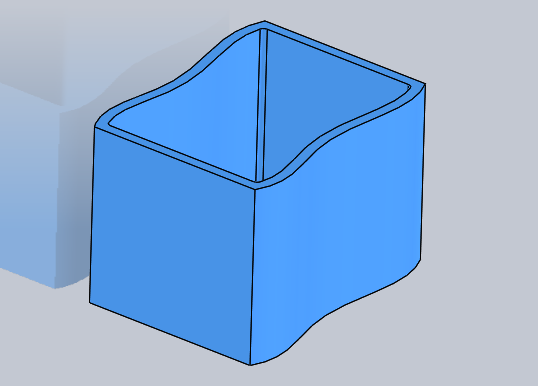
Photos_3D_et_fab/v2019-2020/Image Bloc.PNG
