LibrEduc/RobotBlocs/Photos_3D_et_fab/v2019-2020/photo support crayon 2.png

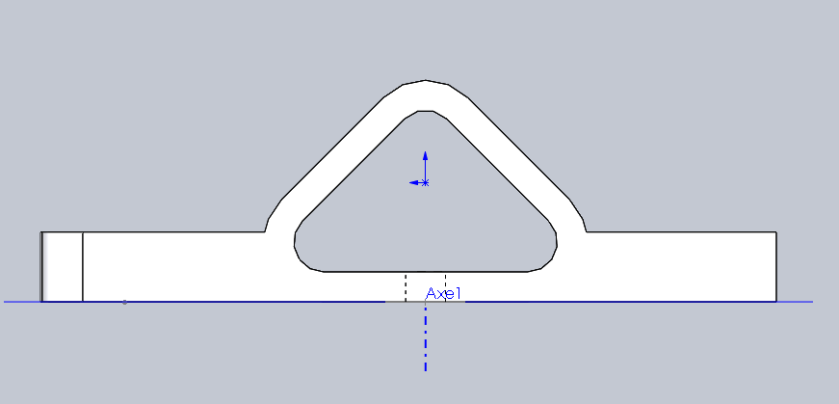
Photos_3D_et_fab/v2019-2020/photo support crayon 2.png
