LibrEduc/RobotBlocs/Photos_3D_et_fab/v2019-2020/rdm robot avant.PNG

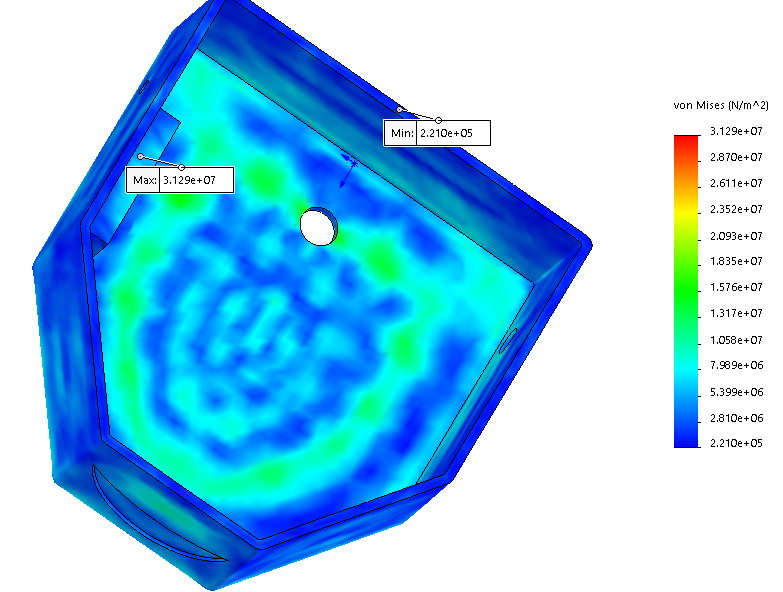
Photos_3D_et_fab/v2019-2020/rdm robot avant.PNG
