LibrEduc/RobotBlocs/Projets_complets/v2020-2021/RobotTraceur1 - Pierre Gautier  - Simon Le Moal - Armand Racine  - Gwen Berrou/brainstorming/brainstorming3.jpg

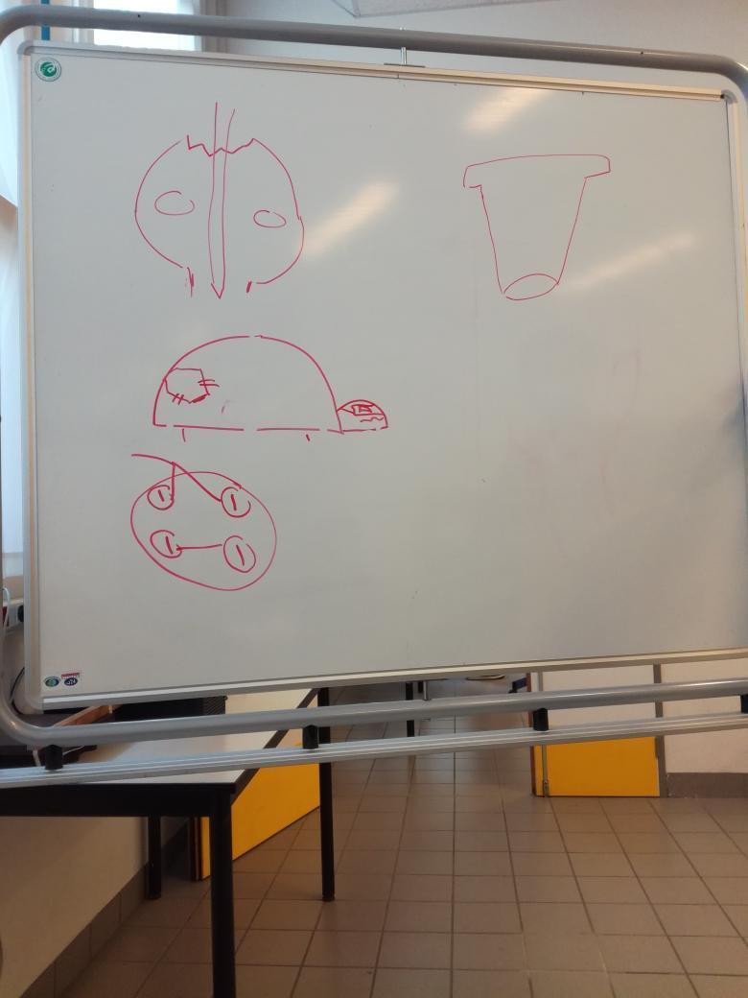
Projets_complets/v2020-2021/RobotTraceur1 - Pierre Gautier - Simon Le Moal - Armand Racine - Gwen Berrou/brainstorming/brainstorming3.jpg
