LibrEduc/RobotBlocs/Projets_complets/v2020-2021/RobotTraceur1 - Pierre Gautier  - Simon Le Moal - Armand Racine  - Gwen Berrou/brainstorming/brainstorming4.jpg

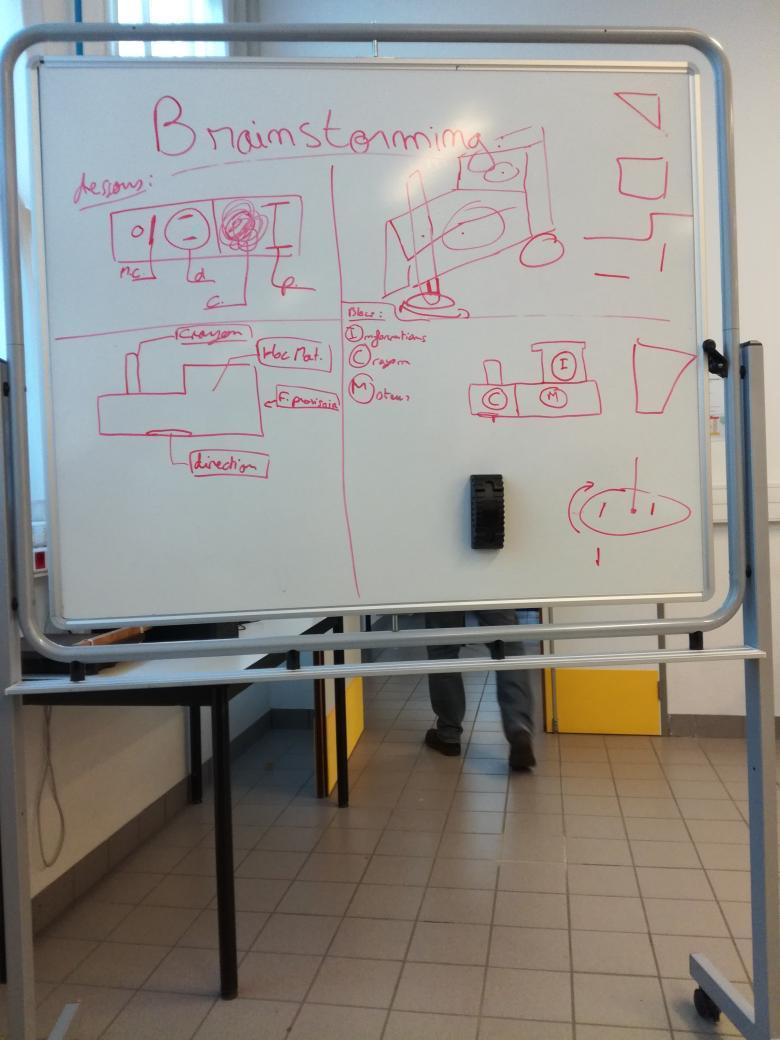
Projets_complets/v2020-2021/RobotTraceur1 - Pierre Gautier - Simon Le Moal - Armand Racine - Gwen Berrou/brainstorming/brainstorming4.jpg
