LibrEduc/RobotBlocs/Projets_complets/v2020-2021/RobotTraceur1 - Pierre Gautier  - Simon Le Moal - Armand Racine  - Gwen Berrou/Conception/Simulations/Chassi/rheologie_temps_de_remplissage.png

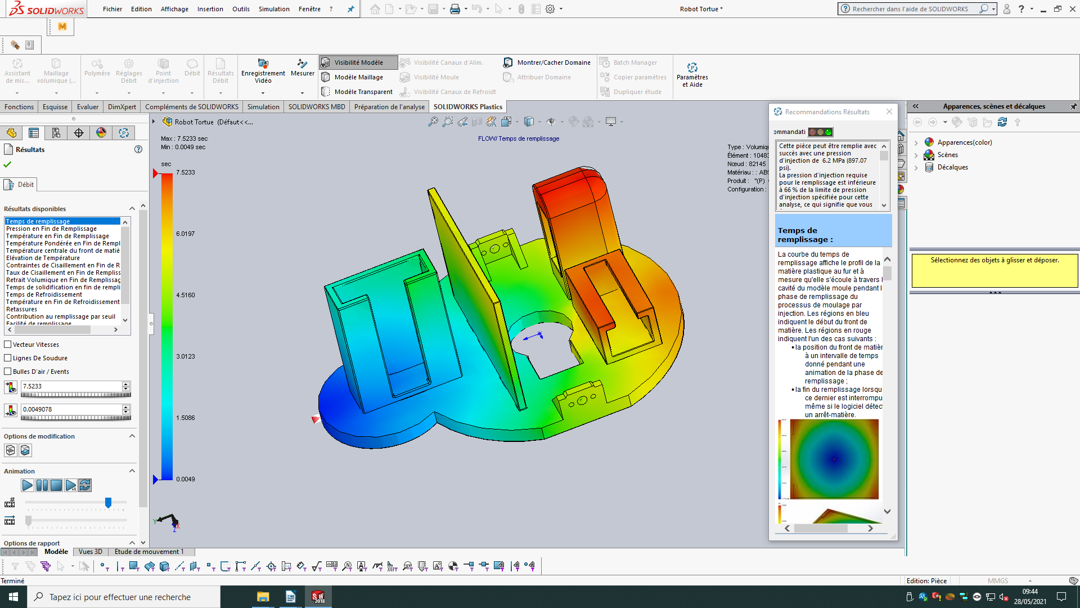
Projets_complets/v2020-2021/RobotTraceur1 - Pierre Gautier - Simon Le Moal - Armand Racine - Gwen Berrou/Conception/Simulations/Chassi/rheologie_temps_de_remplissage.png
