LibrEduc/RobotBlocs/Projets_complets/v2020-2021/RobotTraceur1 - Pierre Gautier  - Simon Le Moal - Armand Racine  - Gwen Berrou/Conception/Support Crayon/support crayon 2 taille reduite/support 3f depalcement.PNG

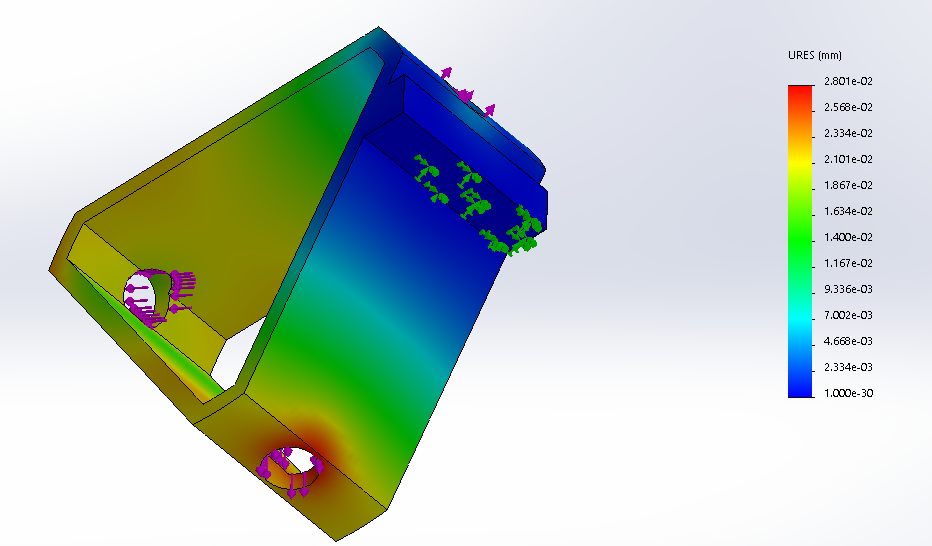
Projets_complets/v2020-2021/RobotTraceur1 - Pierre Gautier - Simon Le Moal - Armand Racine - Gwen Berrou/Conception/Support Crayon/support crayon 2 taille reduite/support 3f depalcement.PNG
