LibrEduc/RobotBlocs/Projets_complets/v2020-2021/RobotTraceur2 - Basile Glo - Gaspar Quéméner - Rahkim Gairbekov - Killian Salmon/Capture des pièces/Moteur_PaP.PNG

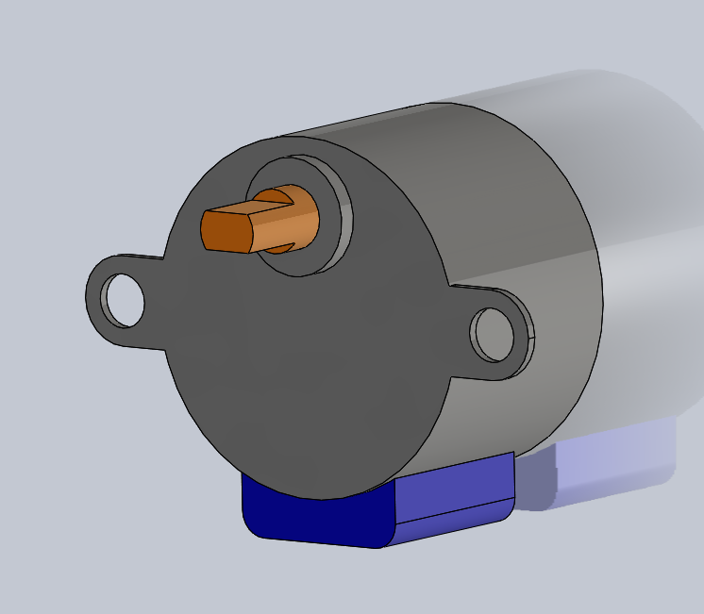
Projets_complets/v2020-2021/RobotTraceur2 - Basile Glo - Gaspar Quéméner - Rahkim Gairbekov - Killian Salmon/Capture des pièces/Moteur_PaP.PNG
