LibrEduc/RobotBlocs/Projets_complets/v2020-2021/RobotTraceur4 - Dylan Morilleau - Arthur Albert - Simon Leservoisier - Marius Bourse - Elouan lucas/camion.jpg

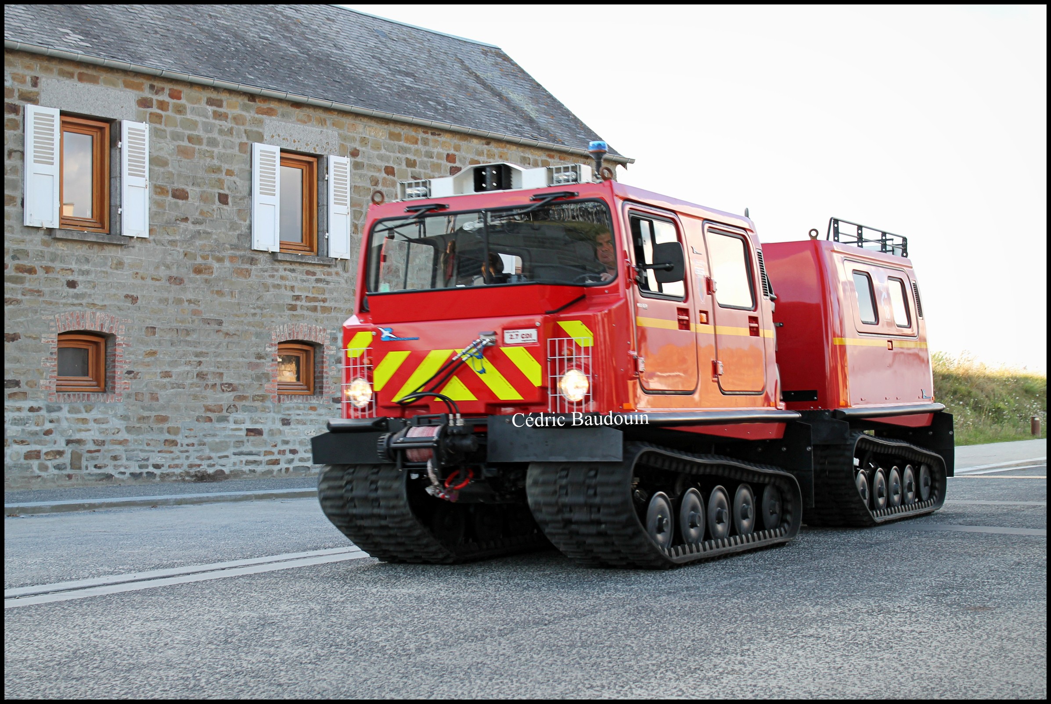
Projets_complets/v2020-2021/RobotTraceur4 - Dylan Morilleau - Arthur Albert - Simon Leservoisier - Marius Bourse - Elouan lucas/camion.jpg
