LibrEduc/RobotBlocs/Sorties/2016-2017/20170118_090955.jpg

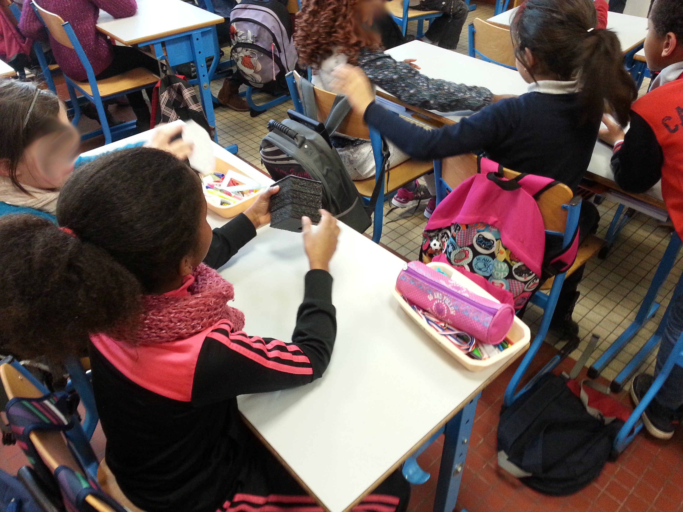
Sorties/2016-2017/20170118_090955.jpg
