LibrEduc/RobotBlocs/Sorties/2016-2017/20170118_091204.jpg

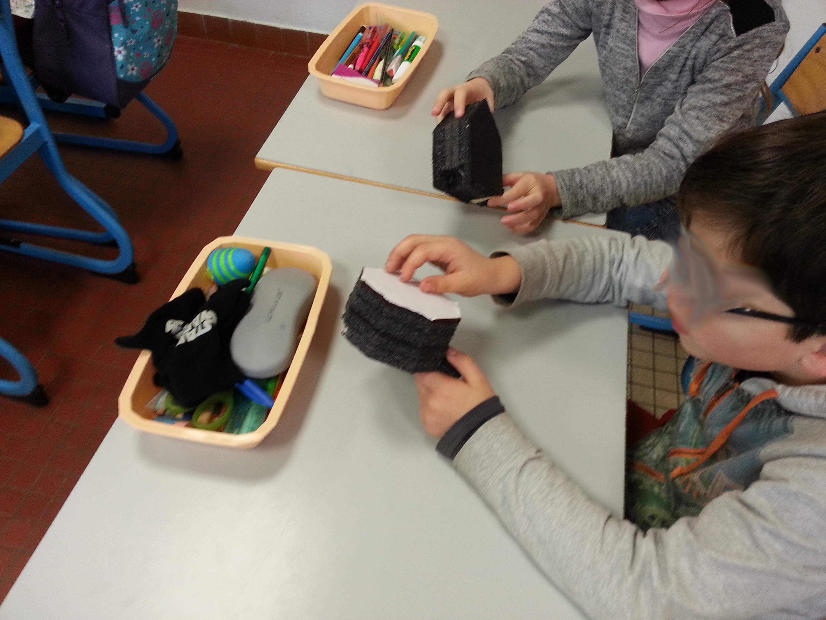
Sorties/2016-2017/20170118_091204.jpg
