LibrEduc/RobotBlocs/Sorties/2016-2017/20170118_091243.jpg

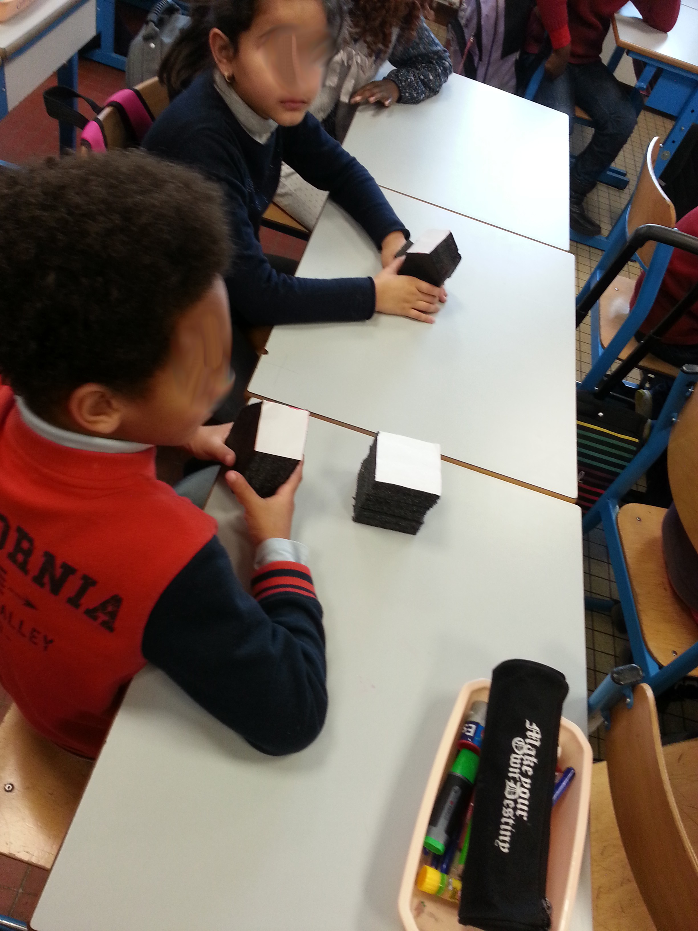
Sorties/2016-2017/20170118_091243.jpg
