LibrEduc/RobotBlocs/Sorties/2016-2017/20170118_094056.jpg

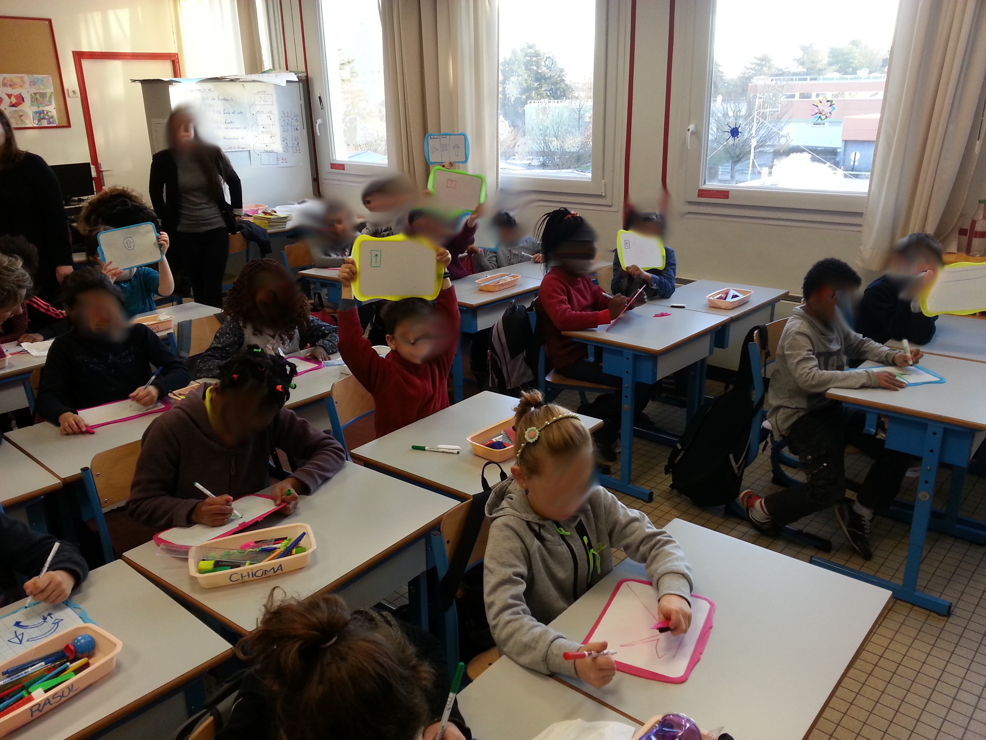
Sorties/2016-2017/20170118_094056.jpg
