LibrEduc/RobotBlocs/Sorties/2016-2017/20170118_094103.jpg

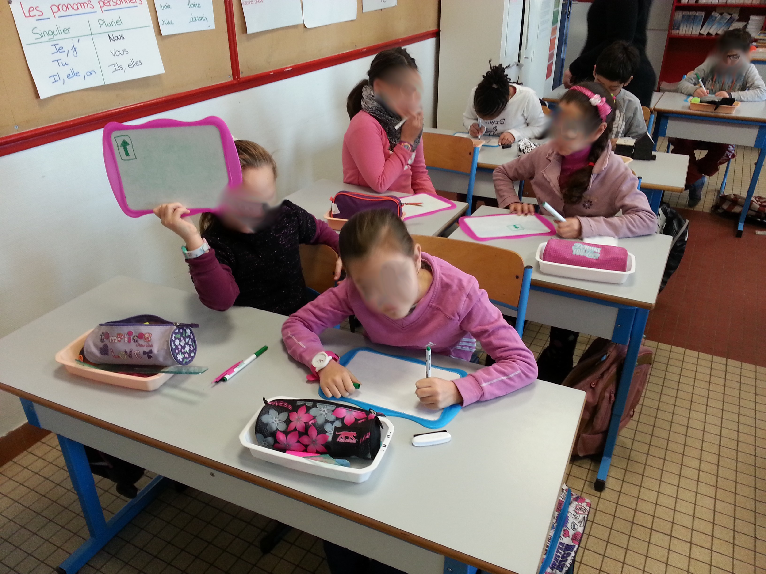
Sorties/2016-2017/20170118_094103.jpg
