LibrEduc/RobotBlocs/Sorties/2016-2017/20170118_095057.jpg

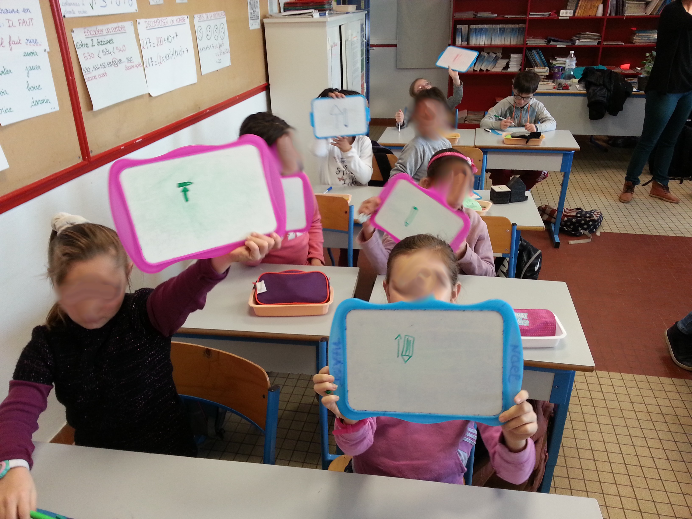
Sorties/2016-2017/20170118_095057.jpg
