LibrEduc/RobotBlocs/Sorties/2016-2017/20170118_095119.jpg

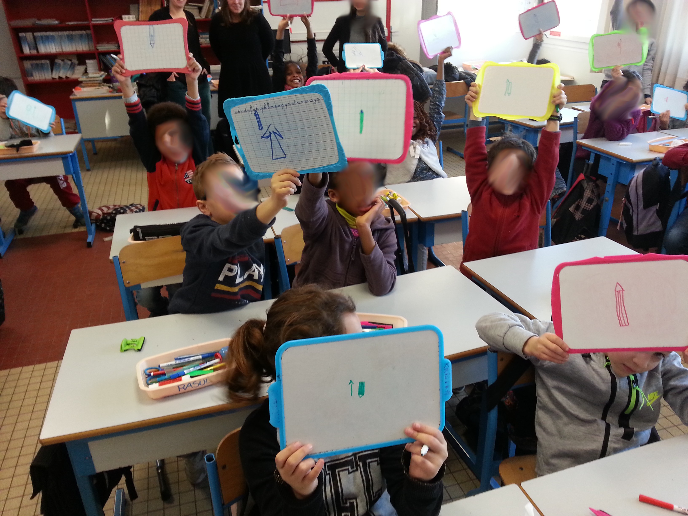
Sorties/2016-2017/20170118_095119.jpg
