LibrEduc/RobotBlocs/Sorties/2016-2017/20170118_095125.jpg

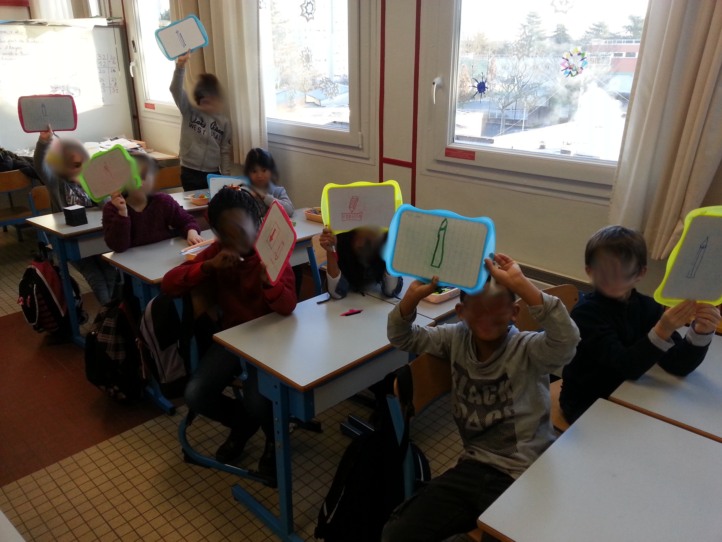
Sorties/2016-2017/20170118_095125.jpg
