LibrEduc/RobotBlocs/Sorties/2016-2017/20170118_100046.jpg

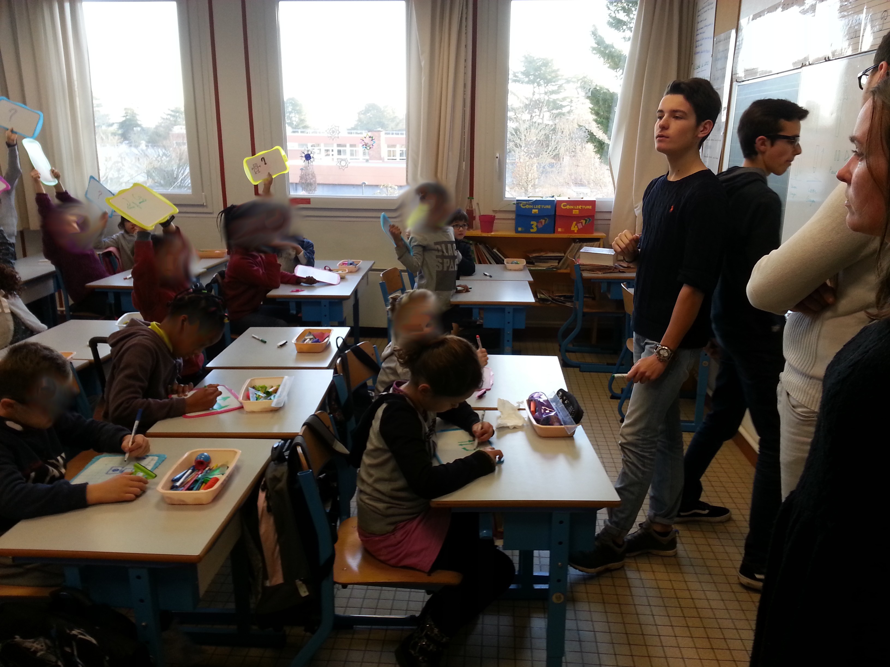
Sorties/2016-2017/20170118_100046.jpg
