LibrEduc/RobotBlocs/Sorties/2016-2017/20170118_100051.jpg

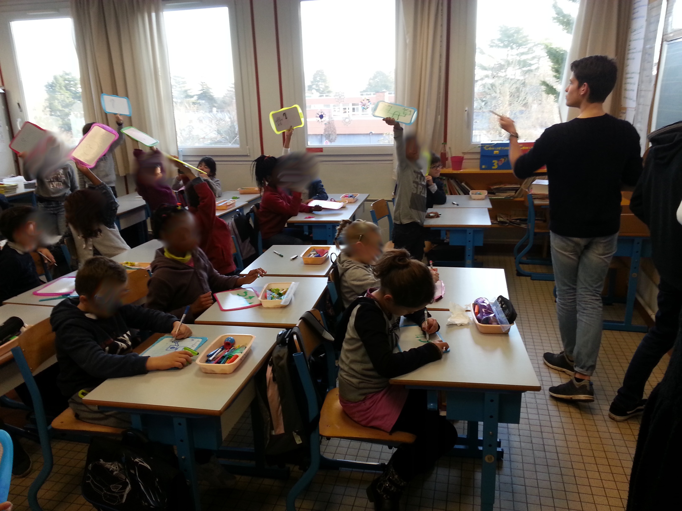
Sorties/2016-2017/20170118_100051.jpg
