LibrEduc/RobotBlocs/Sorties/2016-2017/20170118_103954.jpg

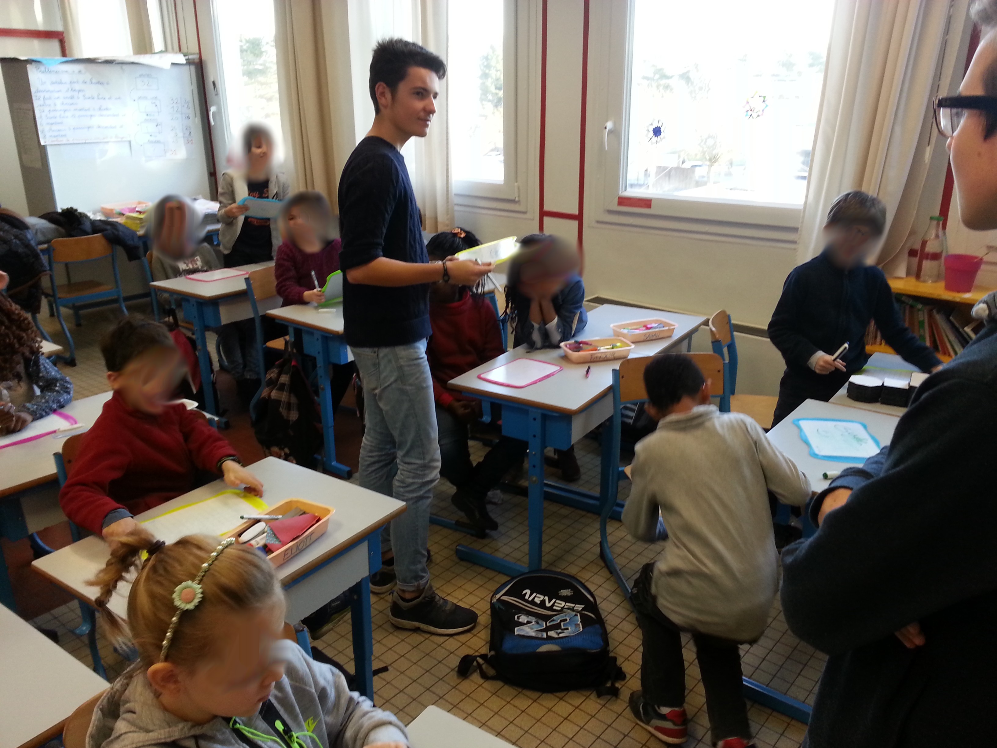
Sorties/2016-2017/20170118_103954.jpg
