LibrEduc/RobotBlocs/Sorties/2018-2019/IMG_20190118_105946_redimensionner.jpg

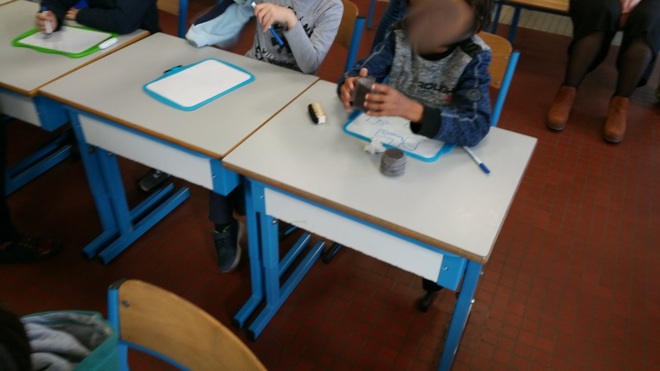
Sorties/2018-2019/IMG_20190118_105946_redimensionner.jpg
