LibrEduc/RobotBlocs/Sorties/2018-2019/IMG_20190118_111452_redimensionner.jpg

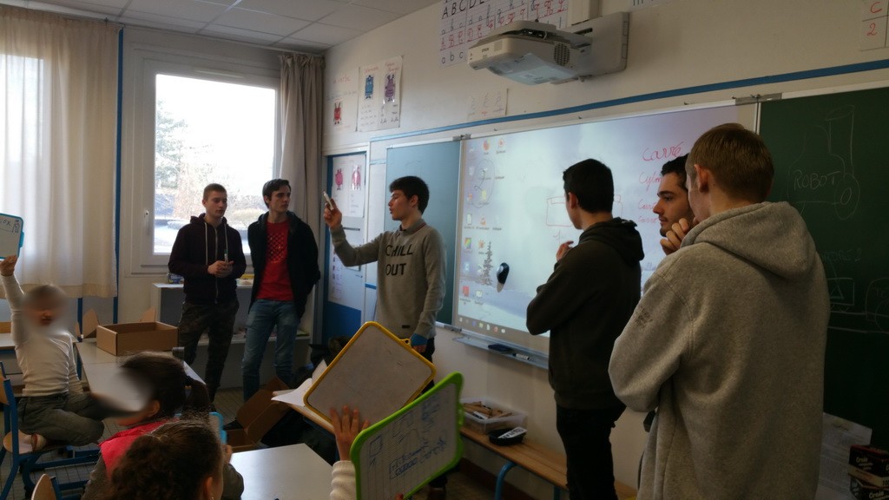
Sorties/2018-2019/IMG_20190118_111452_redimensionner.jpg
