LibrEduc/RobotBlocs/Sorties/2018-2019/IMG_20190118_114415_redimensionner.jpg

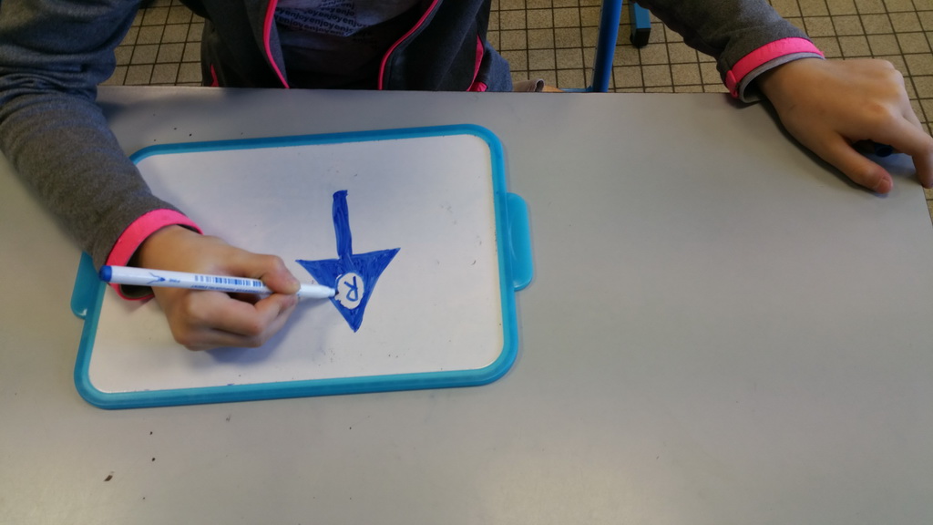
Sorties/2018-2019/IMG_20190118_114415_redimensionner.jpg
