LibrEduc/RobotBlocs/Modeles_3D/Solidworks/v2016-2017/Roboblocs-robot/Sous systèmes - composants/prises XT60/XT60 Connector Female Connector.sldasm

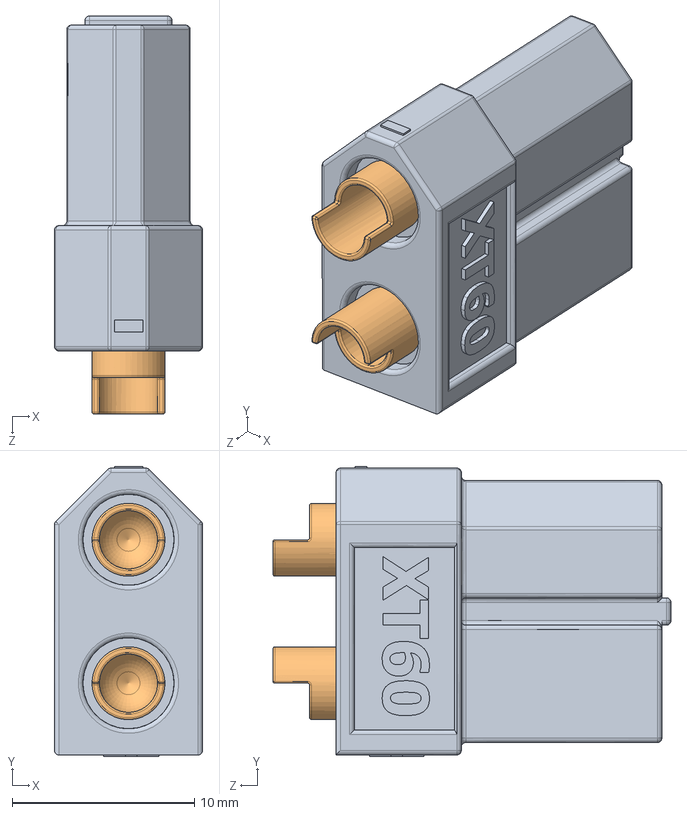
[picture p275: CAD file, 2017-06-28]
Modeles_3D/Solidworks/v2016-2017/Roboblocs-robot/Sous systèmes - composants/prises XT60/XT60 Connector Female Connector.sldasm
8.13 x 15.9 x 21.8 mm
XT60 Connector Female Housing
XT60 Connector Female Contact x 2
