LibrEduc/RobotBlocs/Modeles_3D/Solidworks/v2019-2020/robot/!Assemblage final.SLDASM

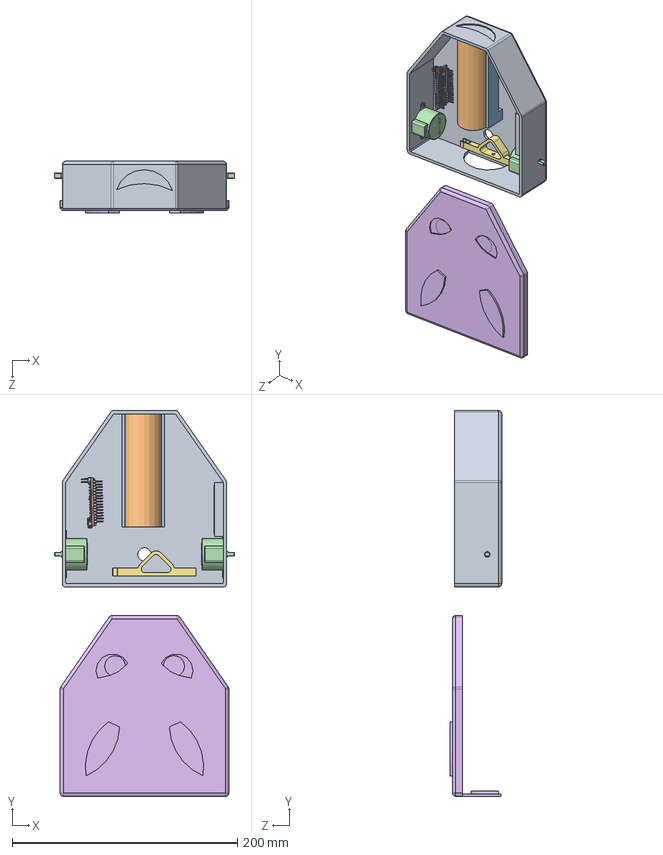
[picture p276: CAD file, 2021-02-01]
Modeles_3D/Solidworks/v2019-2020/robot/!Assemblage final.SLDASM
160.0 x 343.0 x 46.0 mm
Pièce3
powerbank112
Pièce2
Stepper 28BYJ48 x 2
nano-board
2pin_header__02 x 3
15pin_header__ x 2
atmega328
ftdi FT232rl
smt_resistor222 x 5
led x 4
16mhz crystal - measured
MINIUSBSHELL
MINIUSBCORE
MINI USB CONTACT x 5
cap106C x 2
reset core
nano - reg
NANO DIODE
189 RESISTOR PACK
102 RESISTOR PACK
couvercle
piece support crayon projet
MiniBreadboard
