LibrEduc/RobotBlocs/Projets_complets/v2020-2021/RobotTraceur2 - Basile Glo - Gaspar Quéméner - Rahkim Gairbekov - Killian Salmon/Pièces/Assemblage_final.SLDASM

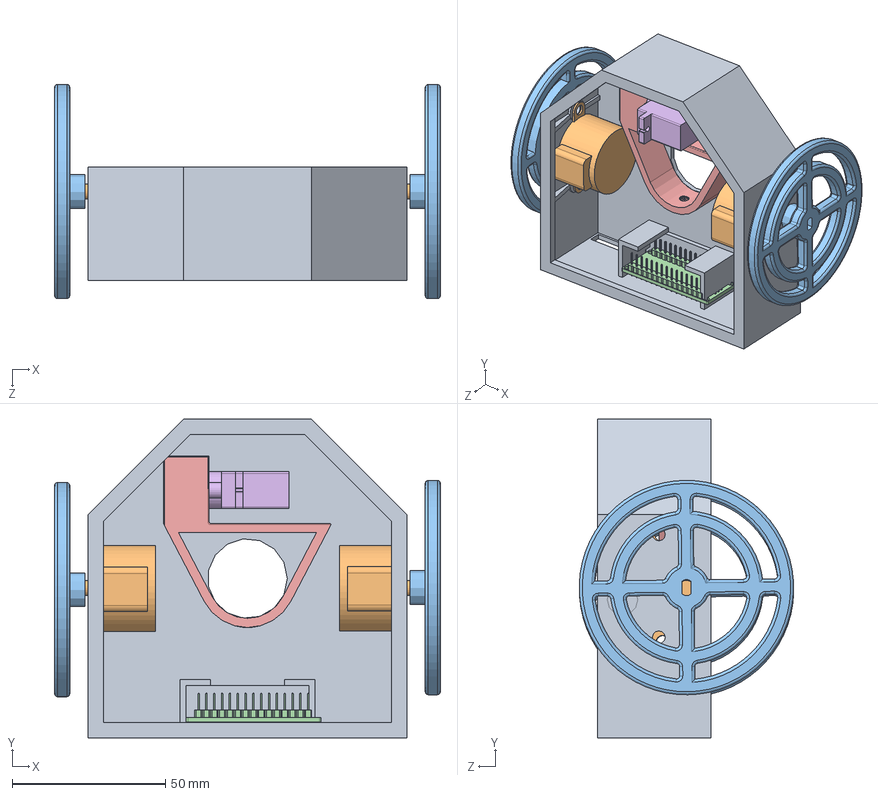
[picture p277: CAD file, 2021-07-25]
Projets_complets/v2020-2021/RobotTraceur2 - Basile Glo - Gaspar Quéméner - Rahkim Gairbekov - Killian Salmon/Pièces/Assemblage_final.SLDASM
126.0 x 104.0 x 70.0 mm
chassis v2
Moteur-pap-Arduino x 2
Roue x 2
arduino nano
attache crayon
Towerpro Micro Servo 9g (1)
