LibrEduc/RobotBlocs/Modeles_3D/Solidworks/v2018-2019/Robot/Assemblage motorisation roue.SLDASM

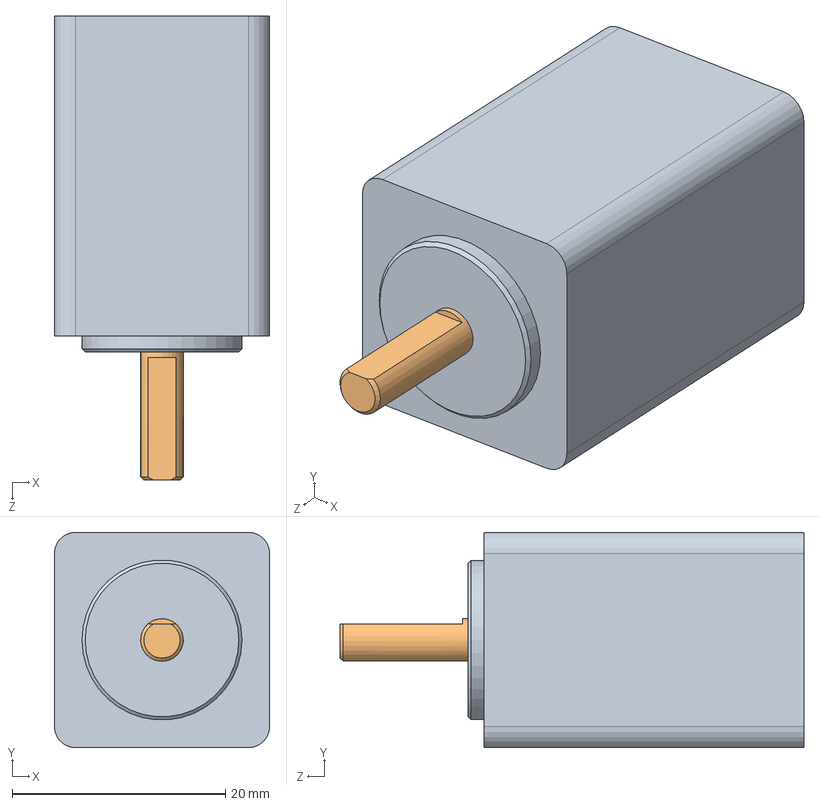
[picture p278: CAD file, 2021-02-01]
Modeles_3D/Solidworks/v2018-2019/Robot/Assemblage motorisation roue.SLDASM
20.2 x 20.2 x 43.5 mm
moteur roue
arbe moteur
