LibrEduc/RobotBlocs/Projets_complets/v2020-2021/RobotTraceur2 - Basile Glo - Gaspar Quéméner - Rahkim Gairbekov - Killian Salmon/Pièces/Module Lora.SLDASM

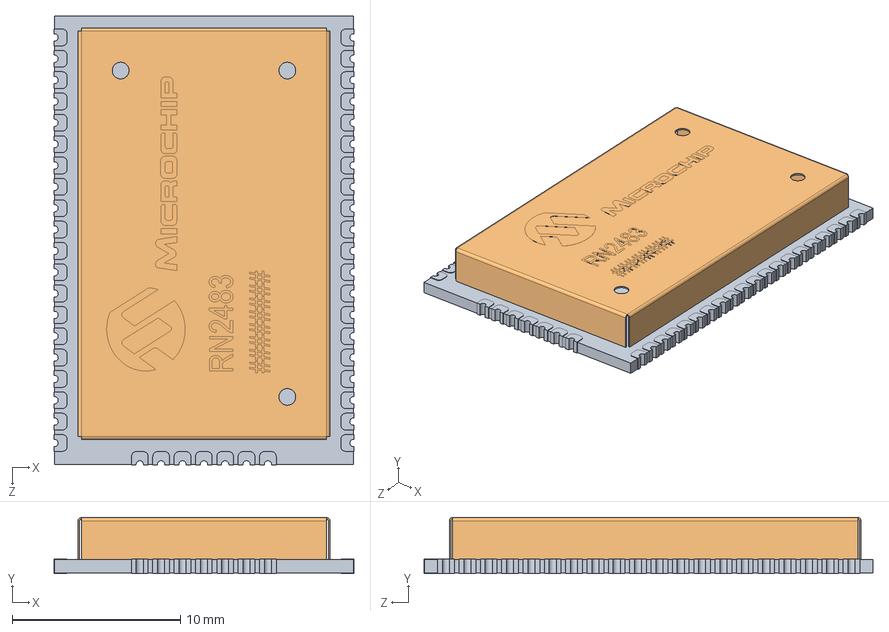
[picture p279: CAD file, 2021-07-25]
Projets_complets/v2020-2021/RobotTraceur2 - Basile Glo - Gaspar Quéméner - Rahkim Gairbekov - Killian Salmon/Pièces/Module Lora.SLDASM
17.9 x 3.35 x 26.7 mm
RN2483-PCB
RN2483-CAN
