LibrEduc/RobotBlocs/Modeles_3D/Solidworks/v2019-2020/robot/arduino nano.SLDASM

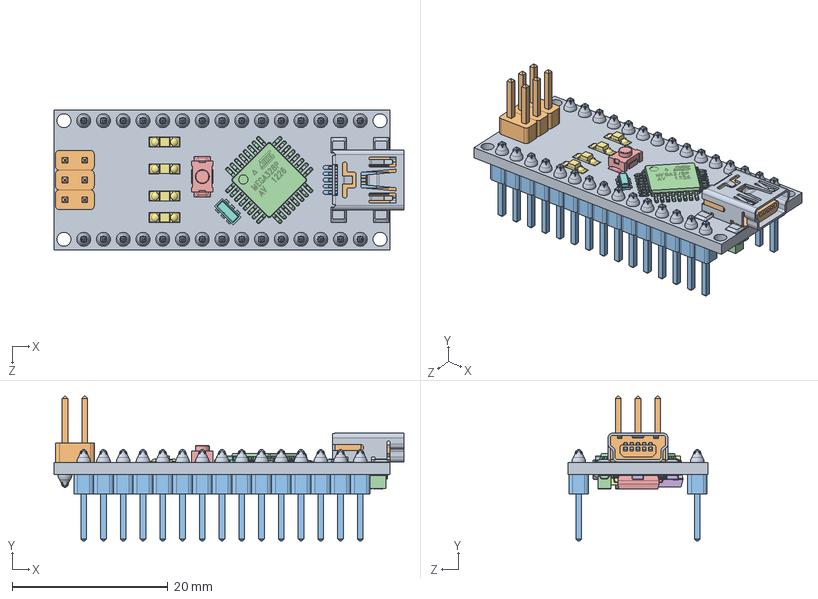
[picture p281: CAD file, 2021-02-01]
Modeles_3D/Solidworks/v2019-2020/robot/arduino nano.SLDASM
45.0 x 18.6 x 18.0 mm
nano-board
2pin_header__02 x 3
15pin_header__ x 2
atmega328
ftdi FT232rl
smt_resistor222 x 5
led x 4
16mhz crystal - measured
MINIUSBSHELL
MINIUSBCORE
MINI USB CONTACT x 5
cap106C x 2
reset core
nano - reg
NANO DIODE
189 RESISTOR PACK
102 RESISTOR PACK
