LibrEduc/RobotBlocs/Projets_complets/v2020-2021/RobotTraceur1 - Pierre Gautier  - Simon Le Moal - Armand Racine  - Gwen Berrou/Conception/Pièces 3D/Assemblage avec tous les composants.SLDASM

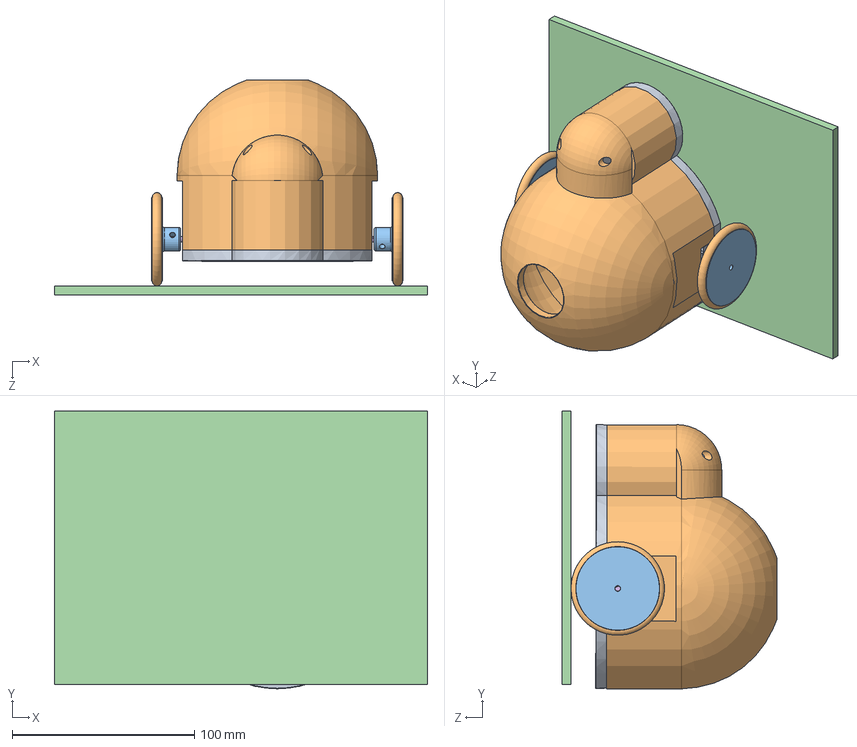
[picture p282: CAD file, 2021-07-25]
Projets_complets/v2020-2021/RobotTraceur1 - Pierre Gautier - Simon Le Moal - Armand Racine - Gwen Berrou/Conception/Pièces 3D/Assemblage avec tous les composants.SLDASM
204.5 x 152.3 x 118.0 mm
Robot Tortue
Joint torique 40,64x5,32 x 2
Roue x 2
sol
motor x 2
n20_shaft x 2
n20_gearbox x 2
cross recessed countersunk head screws gb1 x 4
spur gear_gb x 12
Pièce1^Assemblage avec tous les composants
