LibrEduc/RobotBlocs/Modeles_3D/Solidworks/v2016-2017/Roboblocs-robot/Sous systèmes - composants/arduino uno/USB type b.SLDPRT.SLDASM

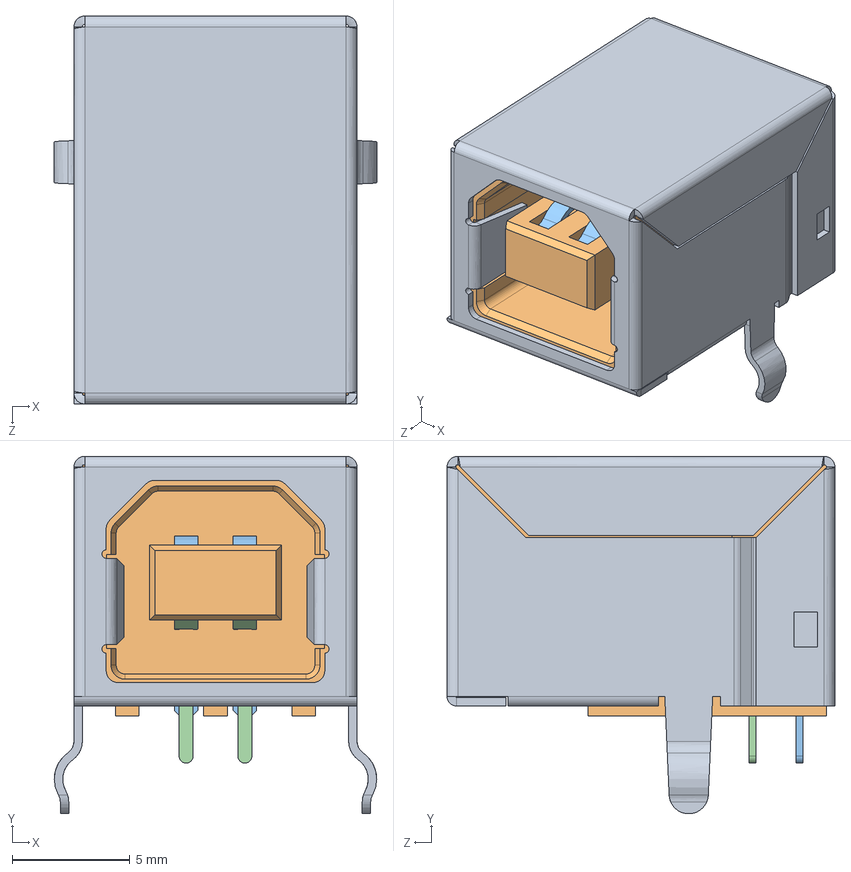
[picture p283: CAD file, 2017-06-28]
Modeles_3D/Solidworks/v2016-2017/Roboblocs-robot/Sous systèmes - composants/arduino uno/USB type b.SLDPRT.SLDASM
13.7 x 15.2 x 16.5 mm
USB SHELL
USB core
usb top contact x 2
usb btm contact x 2
