LibrEduc/RobotBlocs/Projets_complets/v2020-2021/RobotTraceur1 - Pierre Gautier  - Simon Le Moal - Armand Racine  - Gwen Berrou/Conception/Pièces 3D/Assemblage Roue.SLDASM

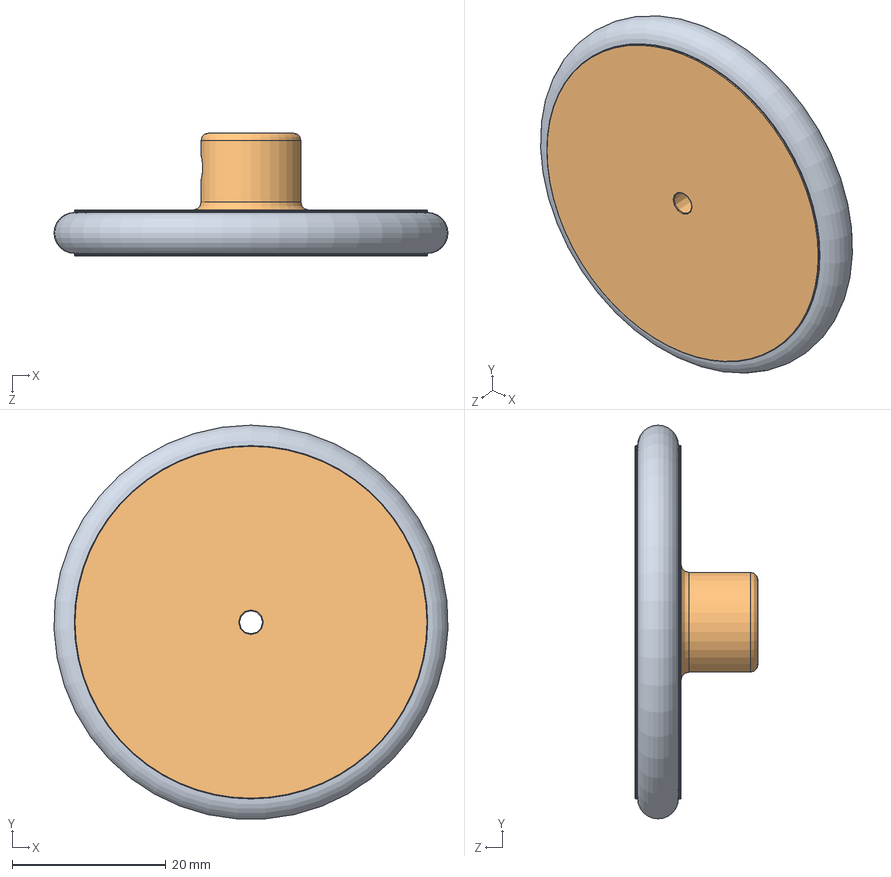
[picture p284: CAD file, 2021-07-25]
Projets_complets/v2020-2021/RobotTraceur1 - Pierre Gautier - Simon Le Moal - Armand Racine - Gwen Berrou/Conception/Pièces 3D/Assemblage Roue.SLDASM
51.2 x 51.2 x 16.0 mm
Joint torique 40,64x5,32
Roue
