LibrEduc/RobotBlocs/Modeles_3D/Solidworks/v2019-2020/robot/MINIUSB - MEASURED.SLDASM

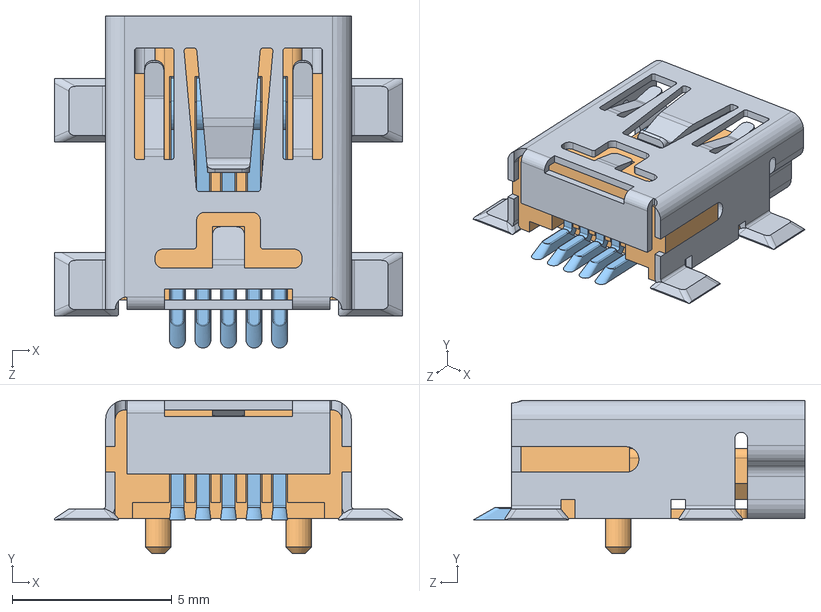
[picture p285: CAD file, 2021-02-01]
Modeles_3D/Solidworks/v2019-2020/robot/MINIUSB - MEASURED.SLDASM
10.9 x 4.80 x 10.4 mm
MINIUSBSHELL
MINIUSBCORE
MINI USB CONTACT x 5
