LibrEduc/RobotBlocs/Modeles_3D/STL/v2016-2017/Robot - Batterie-1 corps batterie.SLDASM-1.STL

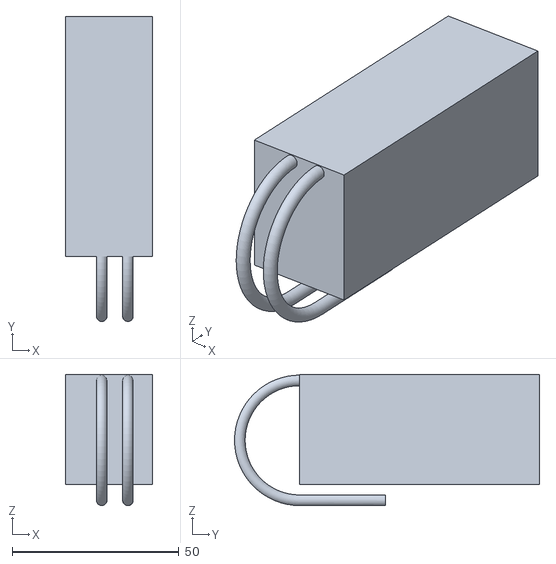
[picture p286: CAD file, 2017-06-28]
Modeles_3D/STL/v2016-2017/Robot - Batterie-1 corps batterie.SLDASM-1.STL
26.0 x 91.6 x 39.4
