LibrEduc/RobotBlocs/Projets_complets/v2020-2021/RobotTraceur4 - Dylan Morilleau - Arthur Albert - Simon Leservoisier - Marius Bourse - Elouan lucas/pièce crayon/pièce crayon/Assem1.SLDASM

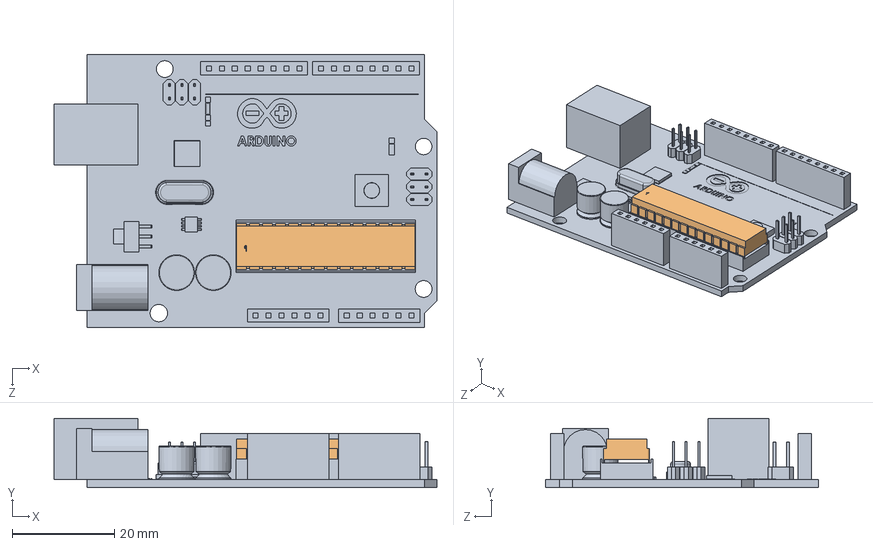
[picture p287: CAD file, 2021-09-23]
Projets_complets/v2020-2021/RobotTraceur4 - Dylan Morilleau - Arthur Albert - Simon Leservoisier - Marius Bourse - Elouan lucas/pièce crayon/pièce crayon/Assem1.SLDASM
75.1 x 13.6 x 53.5 mm
atmel
