LibrEduc/RobotBlocs/Modeles_3D/Solidworks/v2016-2017/Roboblocs-robot/Sous systèmes - composants/arduino nano/support+nano.SLDASM

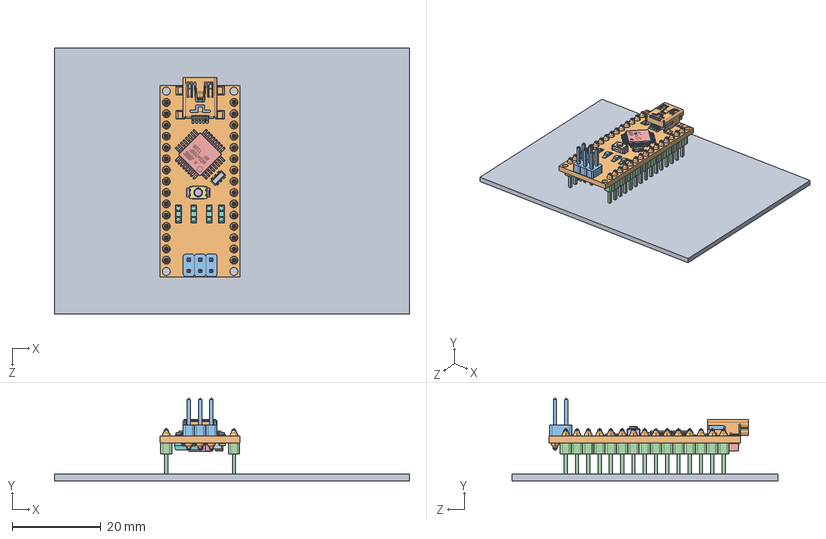
[picture p288: CAD file, 2017-06-28]
Modeles_3D/Solidworks/v2016-2017/Roboblocs-robot/Sous systèmes - composants/arduino nano/support+nano.SLDASM
80.0 x 18.6 x 60.0 mm
support nano
nano-board
2pin_header__02 x 3
15pin_header__ x 2
atmega328
ftdi FT232rl
smt_resistor222 x 5
led x 4
16mhz crystal - measured
MINIUSBSHELL
MINIUSBCORE
MINI USB CONTACT x 5
cap106C x 2
reset core
reset shell
nano - reg
NANO DIODE
189 RESISTOR PACK
102 RESISTOR PACK
