LibrEduc/RobotBlocs/Modeles_3D/STL/v2016-2017/assemblage bloc maître et couvercle finit - bloc maître.STL

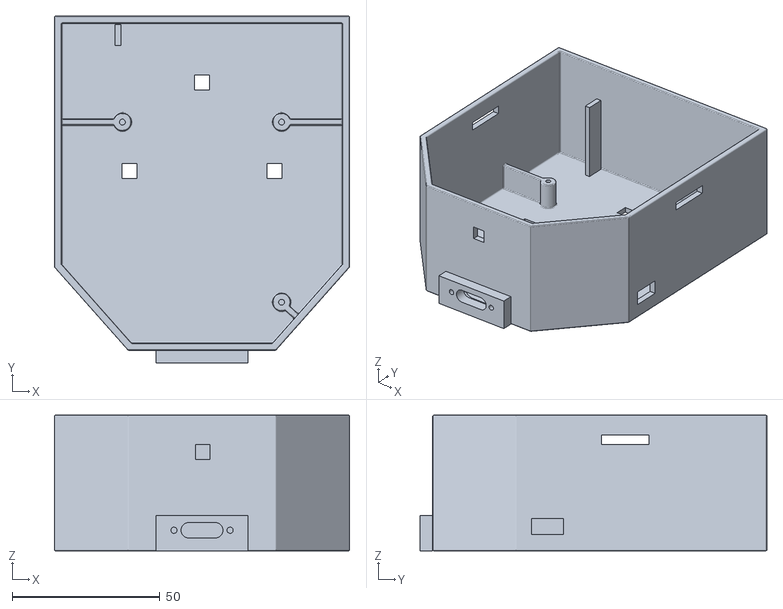
[picture p289: CAD file, 2017-06-28]
Modeles_3D/STL/v2016-2017/assemblage bloc maître et couvercle finit - bloc maître.STL
100.0 x 117.5 x 46.0
