LibrEduc/RobotBlocs/Modeles_3D/Solidworks/v2019-2020/robot/reset button.SLDASM

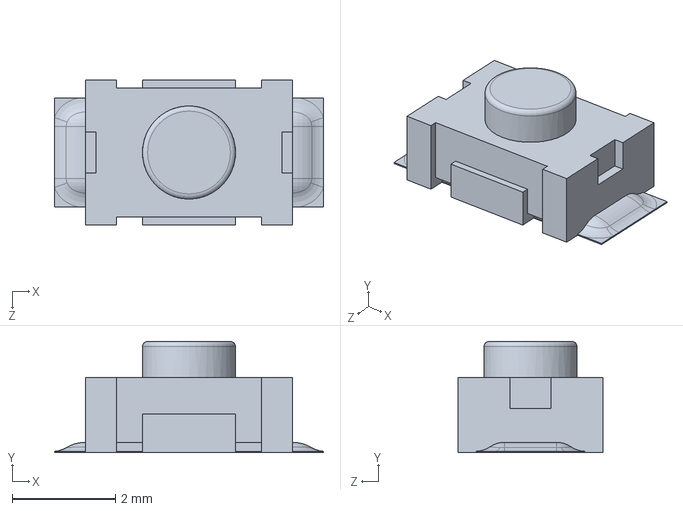
[picture p290: CAD file, 2021-02-01]
Modeles_3D/Solidworks/v2019-2020/robot/reset button.SLDASM
5.20 x 2.15 x 2.80 mm
