LibrEduc/RobotBlocs/Modeles_3D/Solidworks/v2018-2019/Robot/SG90 - Micro Servo 9g - Tower Pro.SLDASM

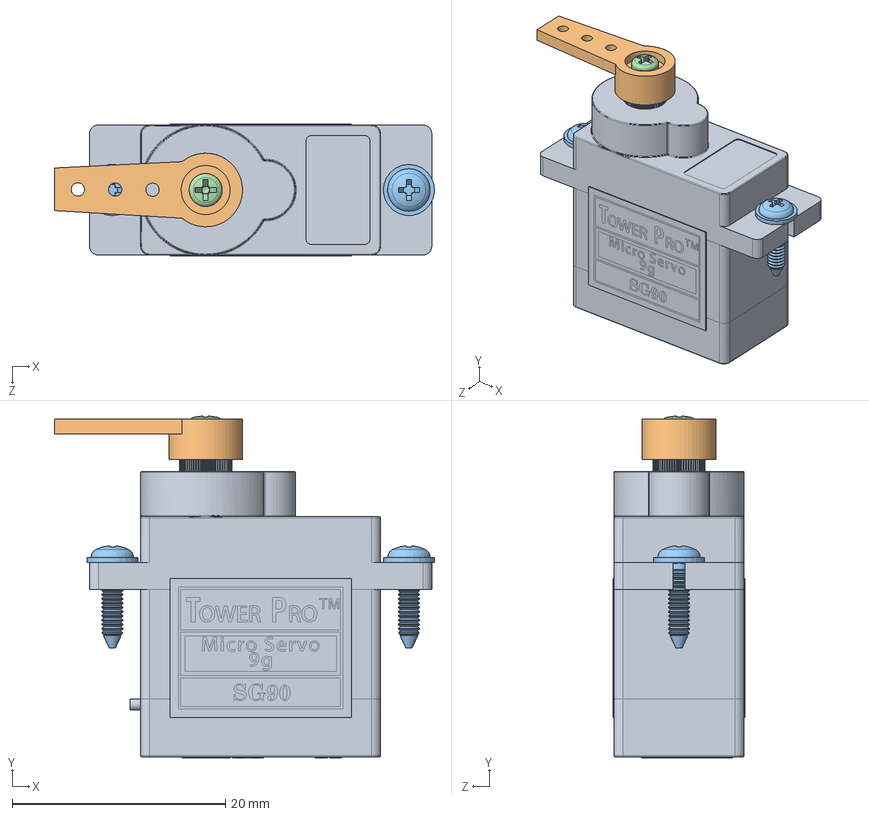
[picture p291: CAD file, 2021-02-01]
Modeles_3D/Solidworks/v2018-2019/Robot/SG90 - Micro Servo 9g - Tower Pro.SLDASM
35.6 x 32.0 x 12.4 mm
SG90 - Micro Servo 9g - Tower Pro.1
SG90 - Micro Servo 9g - Tower Pro.2
SG90 - Micro Servo 9g - Tower Pro.5 x 2
SG90 - Micro Servo 9g - Tower Pro.6
