LibrEduc/RobotBlocs/Projets_complets/v2020-2021/RobotTraceur4 - Dylan Morilleau - Arthur Albert - Simon Leservoisier - Marius Bourse - Elouan lucas/pièce crayon/pièce crayon/maintien.SLDPRT

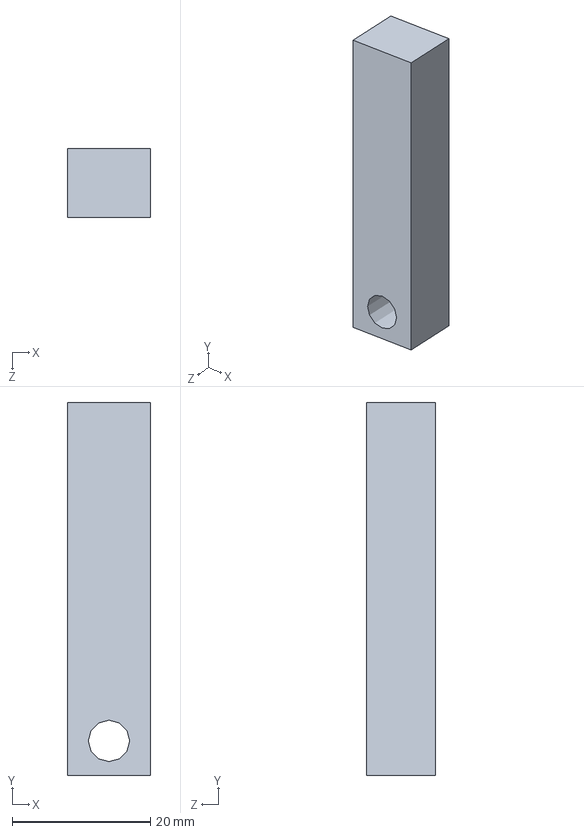
[picture p292: CAD file, 2021-09-23]
Projets_complets/v2020-2021/RobotTraceur4 - Dylan Morilleau - Arthur Albert - Simon Leservoisier - Marius Bourse - Elouan lucas/pièce crayon/pièce crayon/maintien.SLDPRT
12.0 x 54.0 x 10.0 mm
