LibrEduc/RobotBlocs/Modeles_3D/Solidworks/v2016-2017/Roboblocs-robot/Sous systèmes - composants/arduino uno/dip28.SLDASM

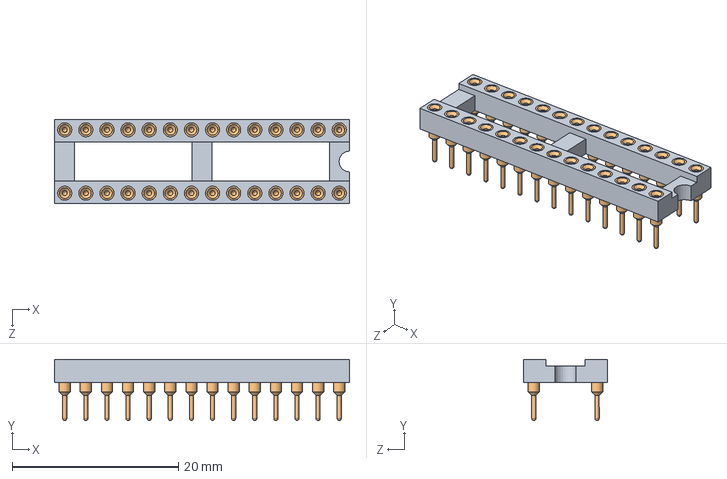
[picture p293: CAD file, 2017-06-28]
Modeles_3D/Solidworks/v2016-2017/Roboblocs-robot/Sous systèmes - composants/arduino uno/dip28.SLDASM
35.5 x 7.37 x 10.1 mm
dip28
dip socket pin x 28
