LibrEduc/RobotBlocs/Modeles_3D/Solidworks/v2016-2017/Roboblocs-robot/Sous systèmes - composants/arduino uno/RESET BUTTON.SLDASM

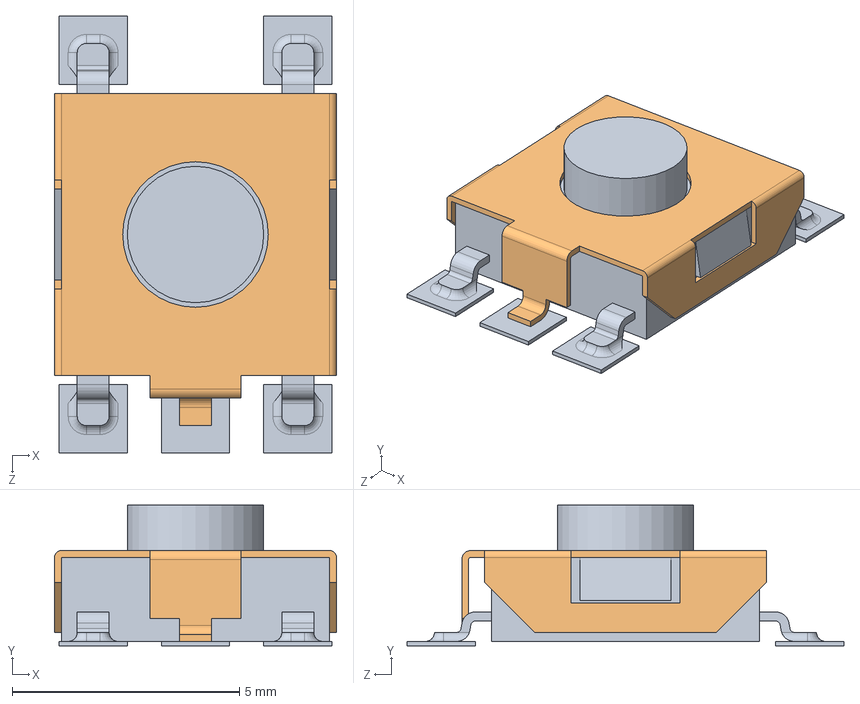
[picture p294: CAD file, 2017-06-28]
Modeles_3D/Solidworks/v2016-2017/Roboblocs-robot/Sous systèmes - composants/arduino uno/RESET BUTTON.SLDASM
6.20 x 3.10 x 9.60 mm
RESET CORE
RESET
