LibrEduc/RobotBlocs/Electronique/protorobotrapido/prototype robot 1.STL

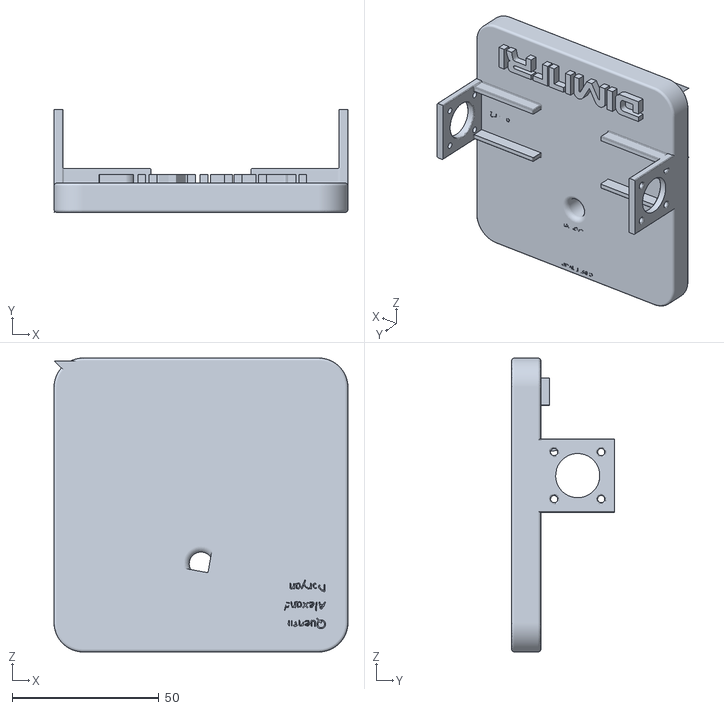
[picture p295: CAD file, 2021-02-01]
Electronique/protorobotrapido/prototype robot 1.STL
100.0 x 35.0 x 100.0
