LibrEduc/RobotBlocs/Modeles_3D/Solidworks/v2016-2017/Roboblocs-progs/pieces_et_couvercles/contacteur/SWIFT DOCK MINI-4-L.STEP

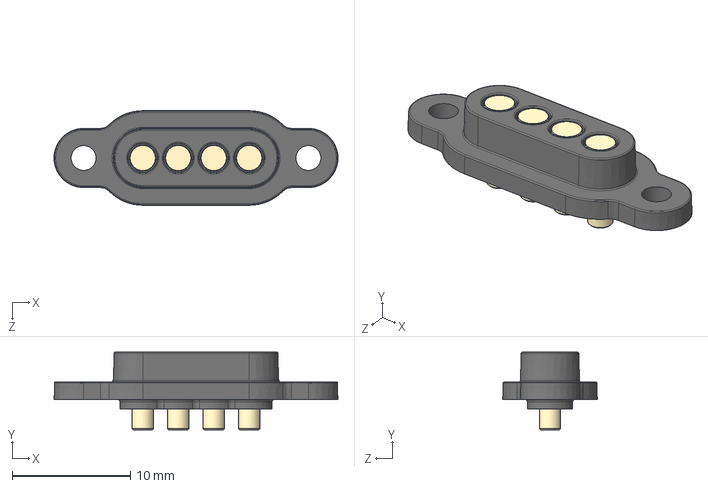
[picture p296: CAD file, 2017-06-28]
Modeles_3D/Solidworks/v2016-2017/Roboblocs-progs/pieces_et_couvercles/contacteur/SWIFT DOCK MINI-4-L.STEP
24.0 x 6.56 x 8.00 mm
land body_4 hole_mini
contact land_sd_mini x 4
