LibrEduc/RobotBlocs/Modeles_3D/Solidworks/v2016-2017/Roboblocs-robot/Sous systèmes - composants/arduino uno/usb top contact.SLDPRT

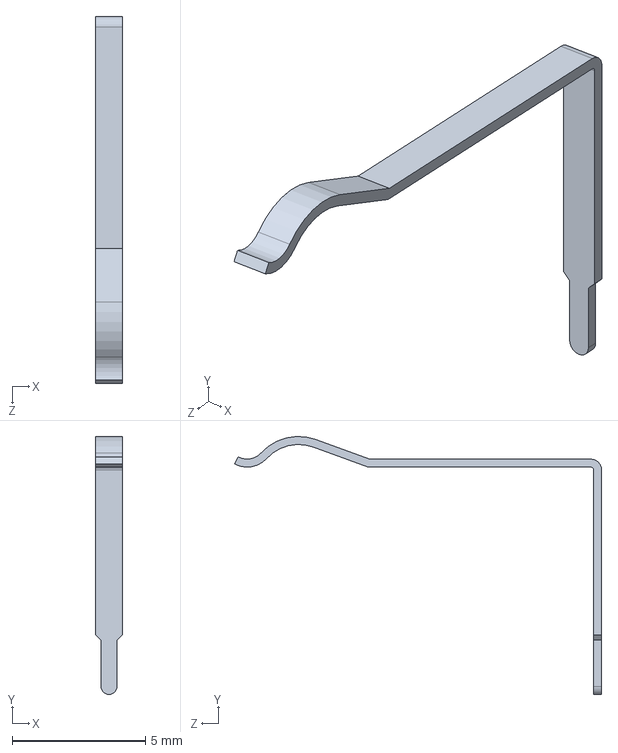
[picture p298: CAD file, 2017-06-28]
Modeles_3D/Solidworks/v2016-2017/Roboblocs-robot/Sous systèmes - composants/arduino uno/usb top contact.SLDPRT
1.00 x 9.67 x 13.8 mm
