LibrEduc/RobotBlocs/Modeles_3D/Solidworks/v2016-2017/Roboblocs-robot/Sous systèmes - composants/Moteur pas à pas (pololu 1204).SLDPRT

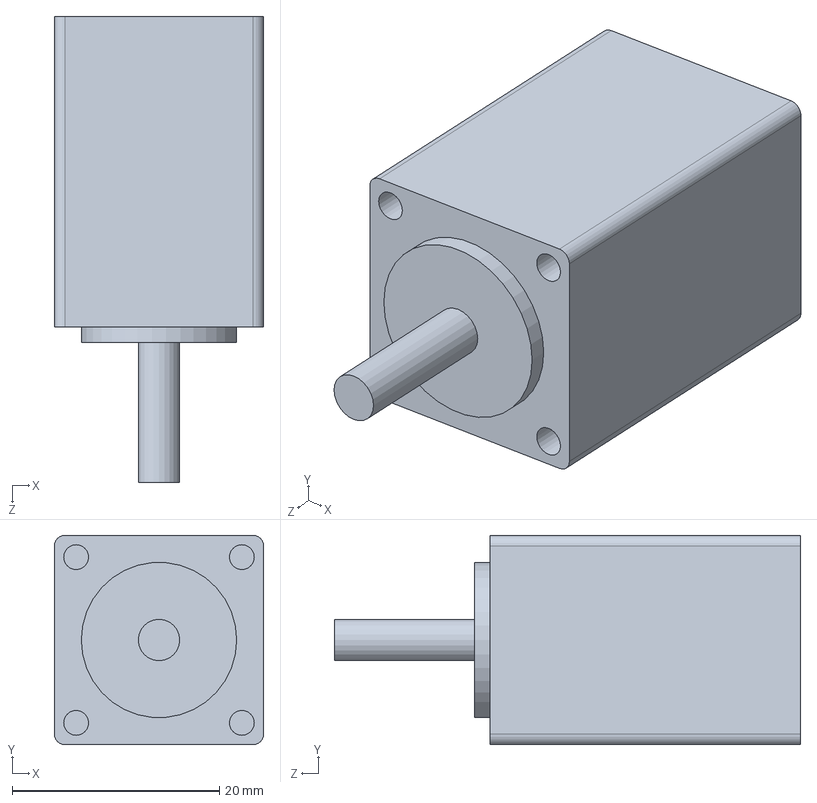
[picture p299: CAD file, 2017-06-28]
Modeles_3D/Solidworks/v2016-2017/Roboblocs-robot/Sous systèmes - composants/Moteur pas à pas (pololu 1204).SLDPRT
20.2 x 20.2 x 45.0 mm
