LibrEduc/RobotBlocs/Modeles_3D/Solidworks/v2018-2019/Bloc-maître/Ball Bearing 608ZZ.SLDPRT

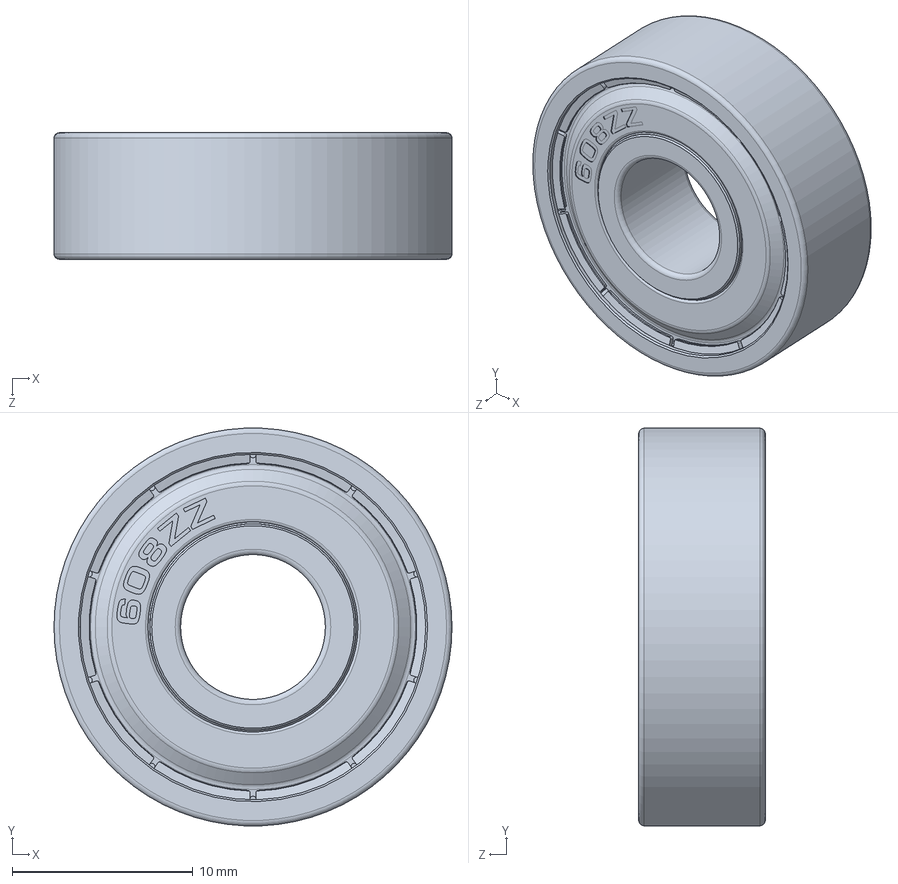
[picture p300: CAD file, 2021-02-01]
Modeles_3D/Solidworks/v2018-2019/Bloc-maître/Ball Bearing 608ZZ.SLDPRT
22.0 x 22.0 x 7.00 mm
