LibrEduc/RobotBlocs/Modeles_3D/Solidworks/v2018-2019/rail.SLDPRT

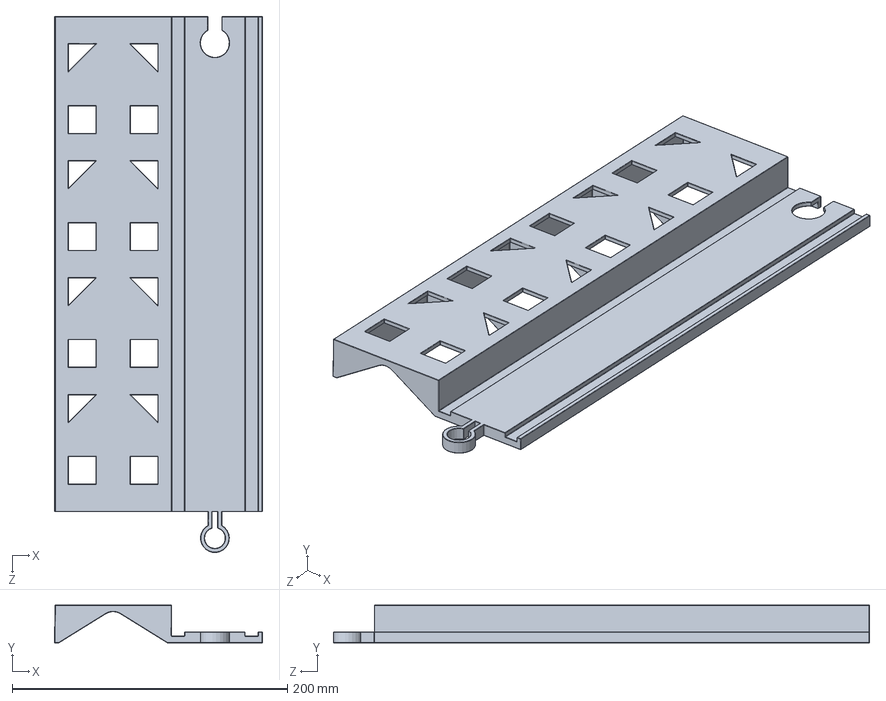
[picture p301: CAD file, 2021-02-01]
Modeles_3D/Solidworks/v2018-2019/rail.SLDPRT
151.3 x 27.5 x 389.7 mm
