LibrEduc/RobotBlocs/Modeles_3D/Solidworks/v2020-2021/BlocsProg2 - Emile Mesnage - Quentin Gallot - Corentin Gloaguen/Solidworks/Conception/Bloc Final projet Avancer 1 pas.SLDPRT

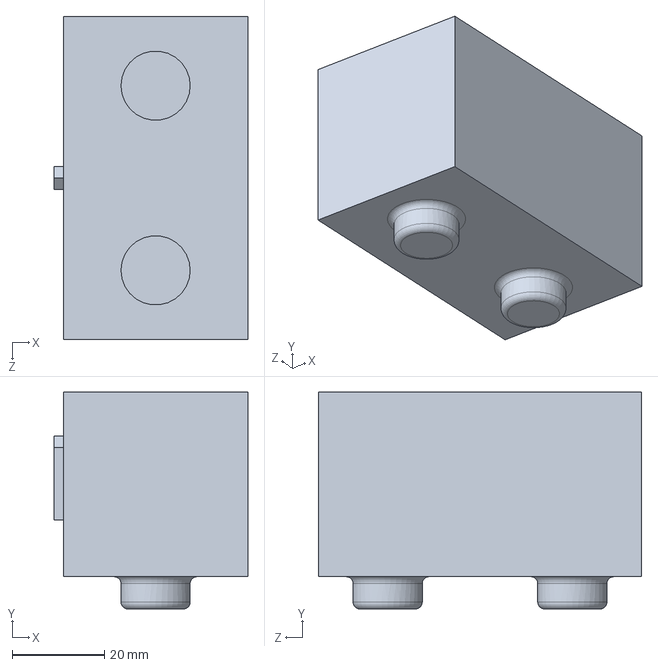
[picture p302: CAD file, 2021-07-25]
Modeles_3D/Solidworks/v2020-2021/BlocsProg2 - Emile Mesnage - Quentin Gallot - Corentin Gloaguen/Solidworks/Conception/Bloc Final projet Avancer 1 pas.SLDPRT
42.0 x 47.0 x 70.0 mm
