LibrEduc/RobotBlocs/Modeles_3D/Solidworks/v2020-2021/BlocsProg3 - Romain Charrier - Maxime Fortune - Sylvain Chéné/piece 1 bloc esclave/Pièce1 bloc esclave.SLDPRT

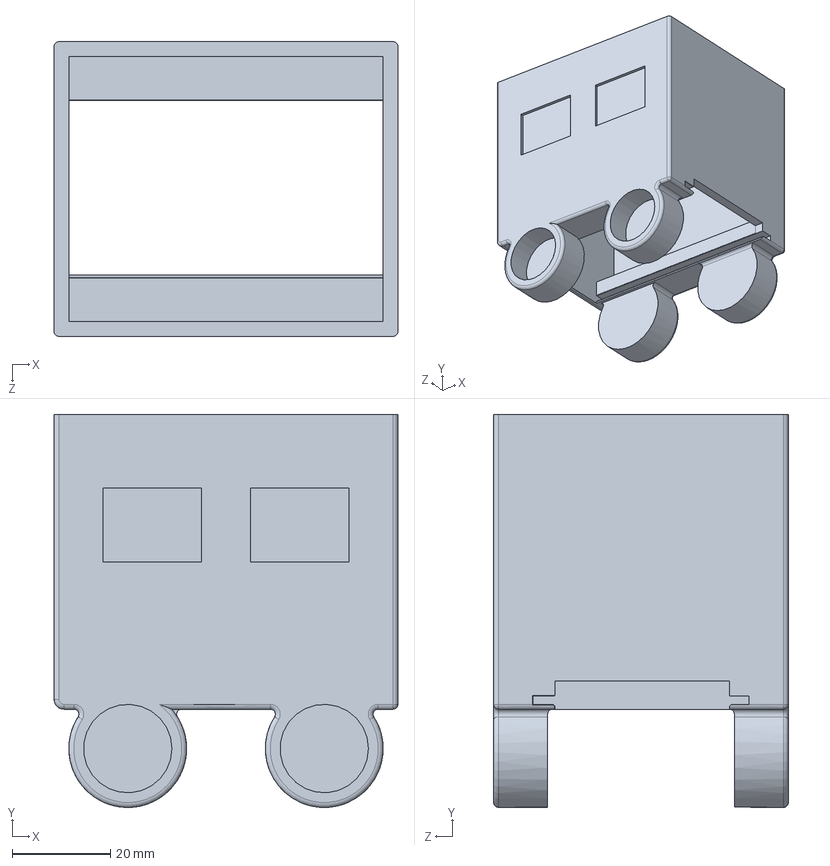
[picture p303: CAD file, 2021-07-25]
Modeles_3D/Solidworks/v2020-2021/BlocsProg3 - Romain Charrier - Maxime Fortune - Sylvain Chéné/piece 1 bloc esclave/Pièce1 bloc esclave.SLDPRT
70.0 x 80.0 x 60.0 mm
