LibrEduc/RobotBlocs/Modeles_3D/Solidworks/v2020-2021/BlocsProg3 - Romain Charrier - Maxime Fortune - Sylvain Chéné/piece 2 bloc maitre/Pièce2 bloc maitre.SLDPRT

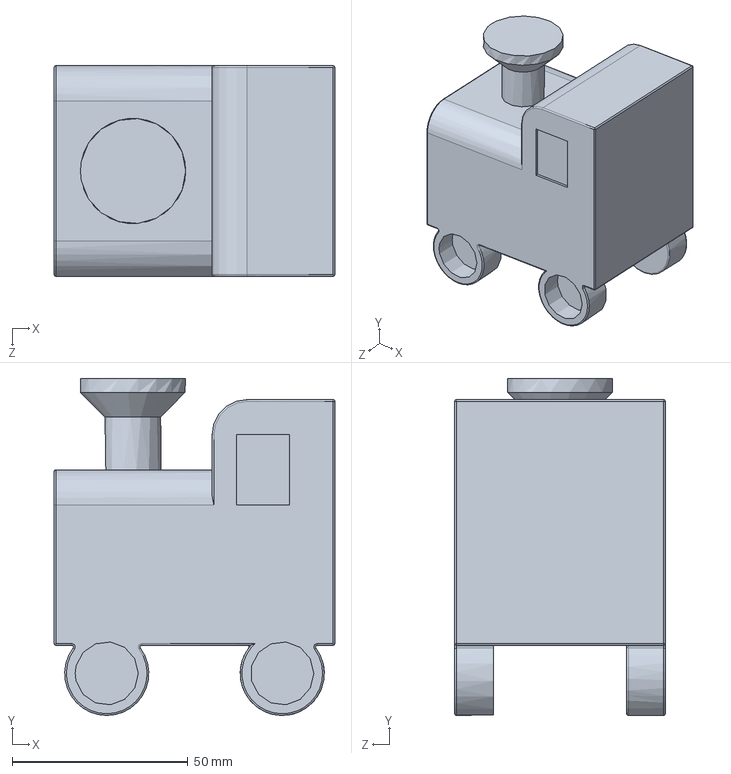
[picture p304: CAD file, 2021-07-25]
Modeles_3D/Solidworks/v2020-2021/BlocsProg3 - Romain Charrier - Maxime Fortune - Sylvain Chéné/piece 2 bloc maitre/Pièce2 bloc maitre.SLDPRT
80.0 x 96.0 x 60.0 mm
