LibrEduc/RobotBlocs/Modeles_3D/STL/v2016-2017/Robot - griffe de guidage-2.STL

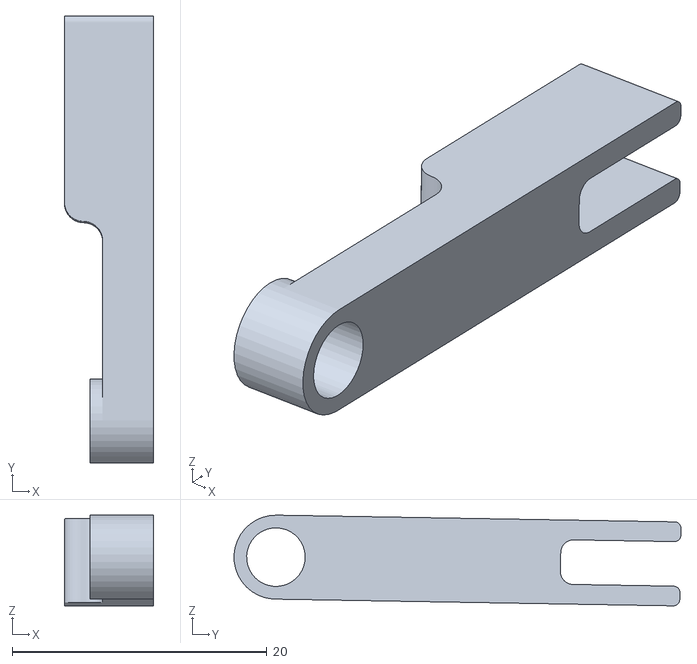
[picture p305: CAD file, 2017-06-28]
Modeles_3D/STL/v2016-2017/Robot - griffe de guidage-2.STL
7.00 x 35.1 x 7.13
