LibrEduc/RobotBlocs/Modeles_3D/STL/v2018-2019/Robot - Porte-stylo-1.STL

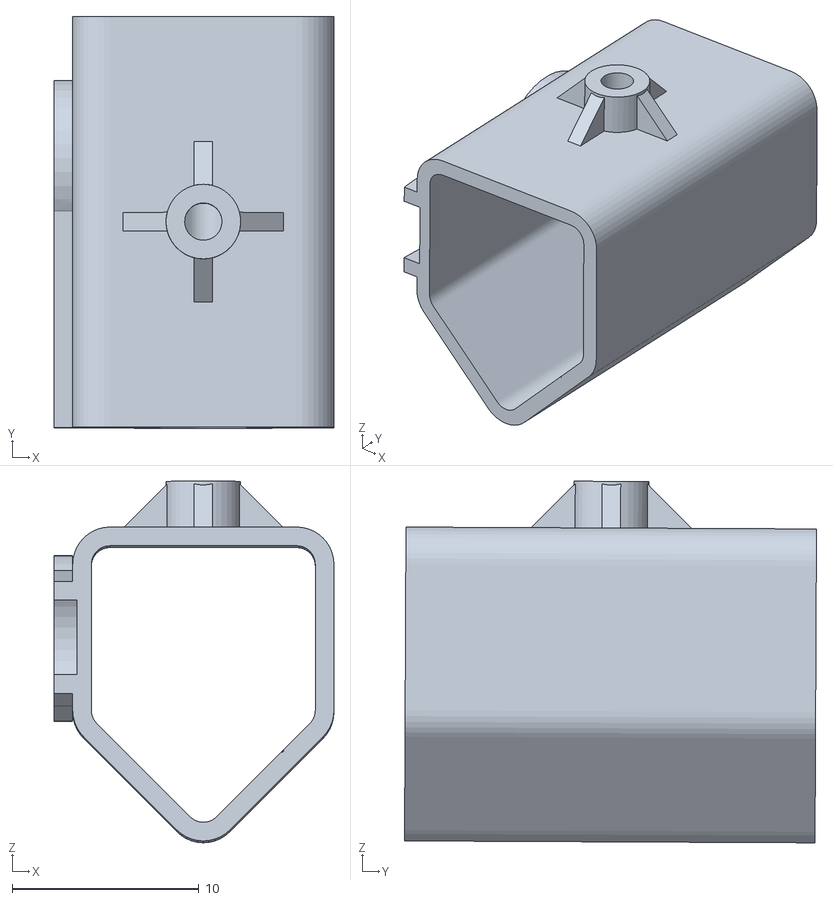
[picture p306: CAD file, 2021-02-01]
Modeles_3D/STL/v2018-2019/Robot - Porte-stylo-1.STL
15.0 x 22.1 x 19.4
