LibrEduc/RobotBlocs/Modeles_3D/STL/v2020-2021/RobotTraceur1/prot bluetooth.STL

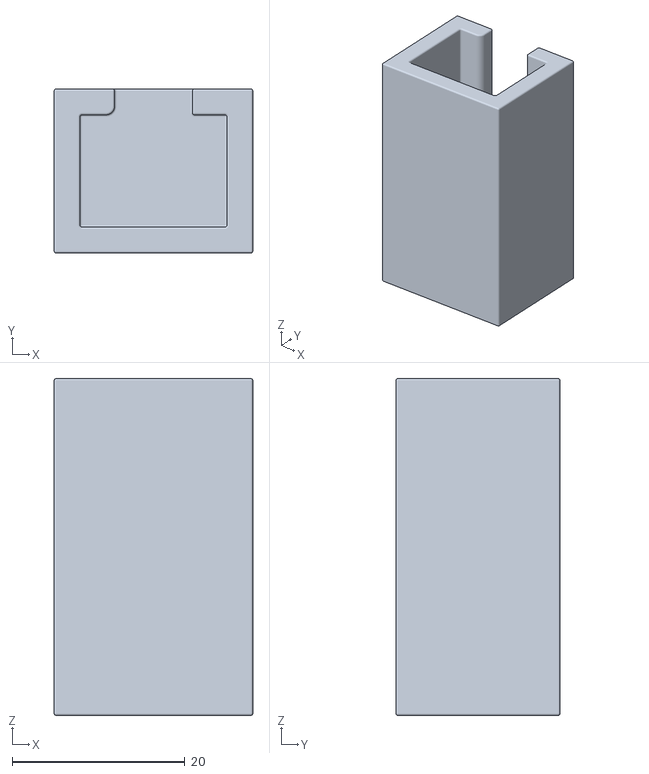
[picture p307: CAD file, 2021-07-25]
Modeles_3D/STL/v2020-2021/RobotTraceur1/prot bluetooth.STL
23.0 x 19.0 x 39.0
