LibrEduc/RobotBlocs/Projets_complets/v2020-2021/RobotTraceur1 - Pierre Gautier  - Simon Le Moal - Armand Racine  - Gwen Berrou/Conception/Pièces 3D/mini dome.SLDPRT

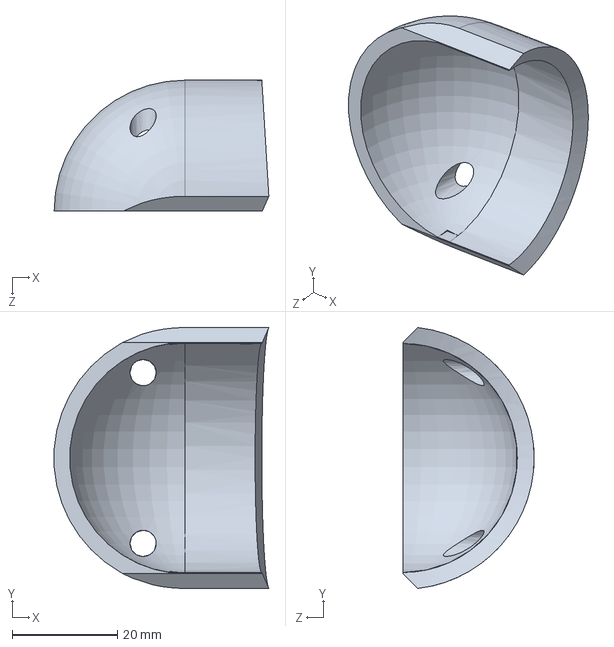
[picture p308: CAD file, 2021-07-25]
Projets_complets/v2020-2021/RobotTraceur1 - Pierre Gautier - Simon Le Moal - Armand Racine - Gwen Berrou/Conception/Pièces 3D/mini dome.SLDPRT
40.9 x 49.7 x 25.0 mm
