LibrEduc/RobotBlocs/Projets_complets/v2020-2021/RobotTraceur1 - Pierre Gautier  - Simon Le Moal - Armand Racine  - Gwen Berrou/Conception/Support Crayon/support crayon 3 optimiser/support crayon opti et finition.SLDPRT

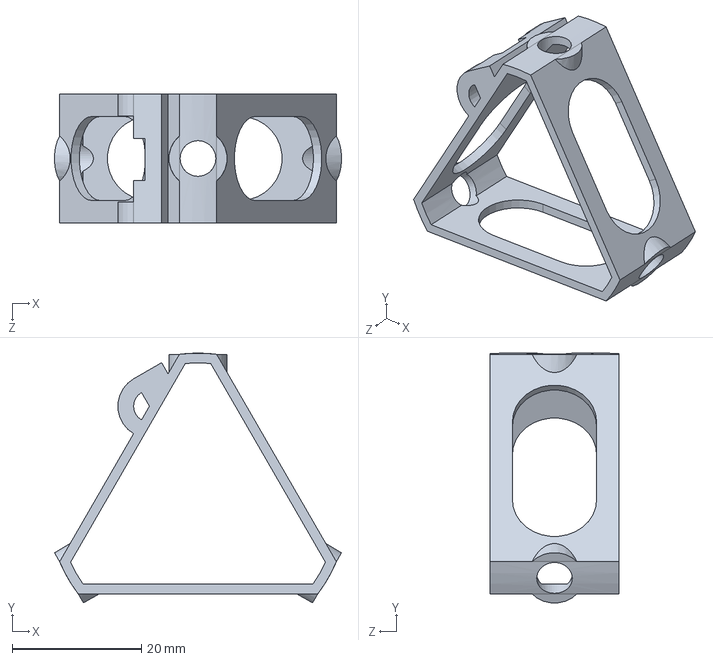
[picture p310: CAD file, 2021-07-25]
Projets_complets/v2020-2021/RobotTraceur1 - Pierre Gautier - Simon Le Moal - Armand Racine - Gwen Berrou/Conception/Support Crayon/support crayon 3 optimiser/support crayon opti et finition.SLDPRT
44.3 x 38.6 x 20.0 mm
