LibrEduc/RobotBlocs/Projets_complets/v2020-2021/RobotTraceur2 - Basile Glo - Gaspar Quéméner - Rahkim Gairbekov - Killian Salmon/Pièces/attache crayon.SLDPRT

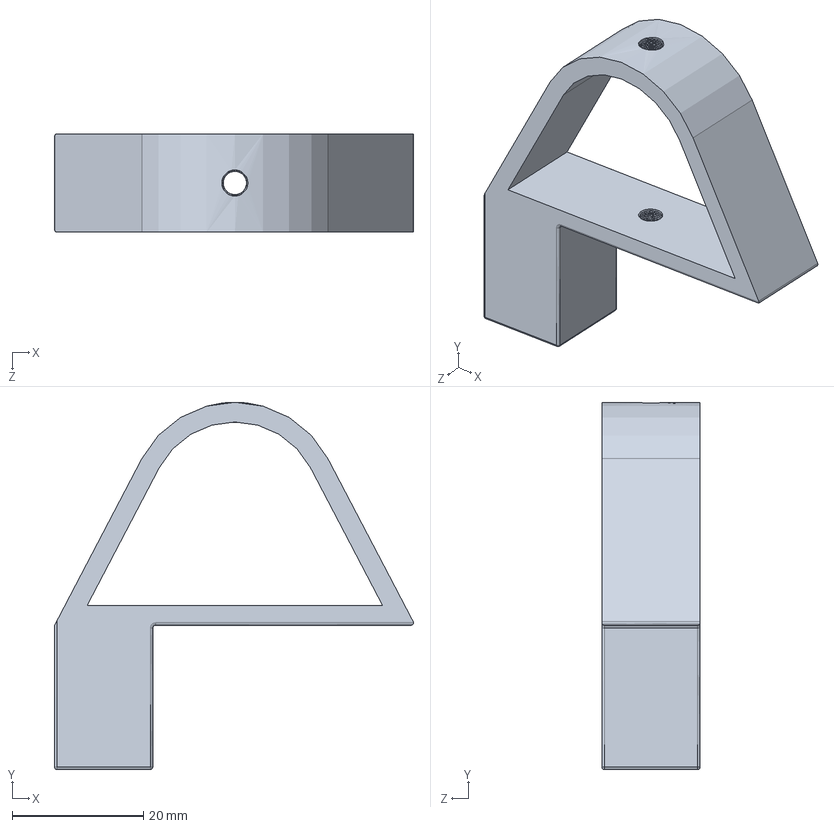
[picture p312: CAD file, 2021-07-25]
Projets_complets/v2020-2021/RobotTraceur2 - Basile Glo - Gaspar Quéméner - Rahkim Gairbekov - Killian Salmon/Pièces/attache crayon.SLDPRT
54.7 x 56.0 x 15.0 mm
