LibrEduc/RobotBlocs/Projets_complets/v2020-2021/RobotTraceur4 - Dylan Morilleau - Arthur Albert - Simon Leservoisier - Marius Bourse - Elouan lucas/pièce crayon/pièce crayon/Batterie.SLDPRT

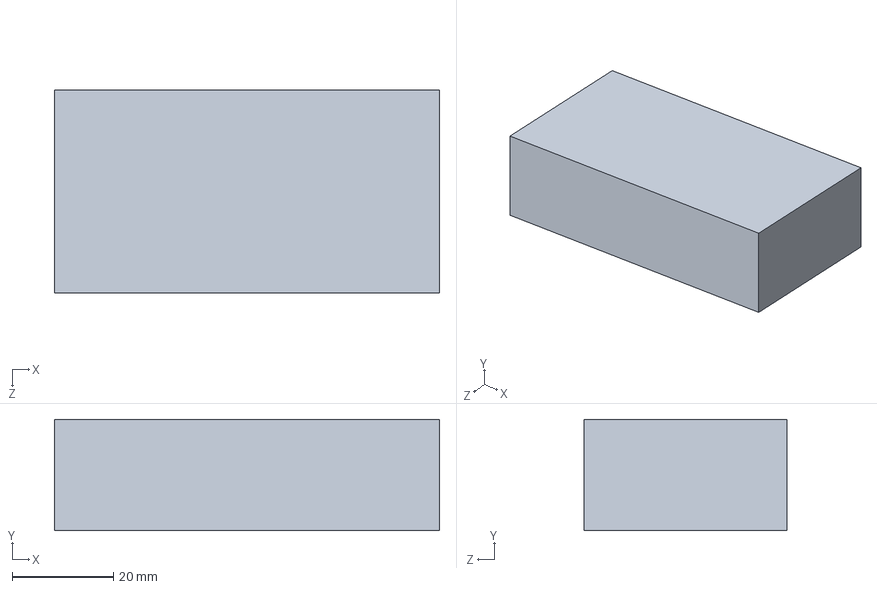
[picture p313: CAD file, 2021-09-23]
Projets_complets/v2020-2021/RobotTraceur4 - Dylan Morilleau - Arthur Albert - Simon Leservoisier - Marius Bourse - Elouan lucas/pièce crayon/pièce crayon/Batterie.SLDPRT
76.0 x 22.0 x 40.0 mm
