LibrEduc/RobotBlocs/Electronique/protorobotrapido/roue.STL

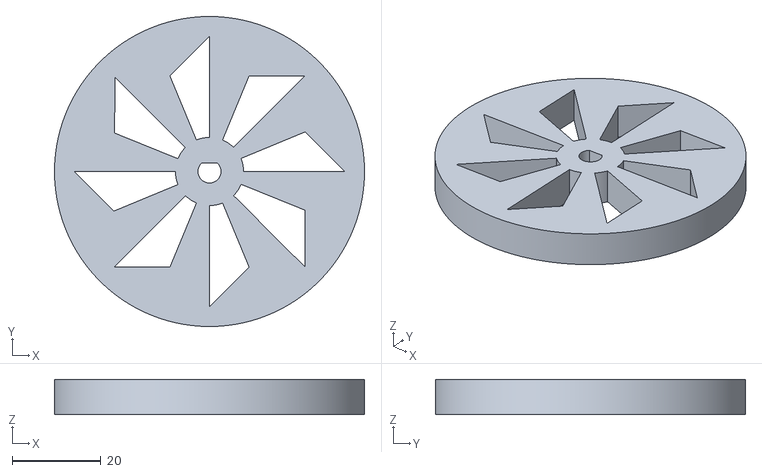
[picture p314: CAD file, 2021-02-01]
Electronique/protorobotrapido/roue.STL
70.0 x 70.0 x 8.00
