LibrEduc/RobotBlocs/Modeles_3D/Solidworks/v2016-2017/Roboblocs-progs/pieces_et_couvercles/contacteur/contact land_sd_mini 3.SLDPRT

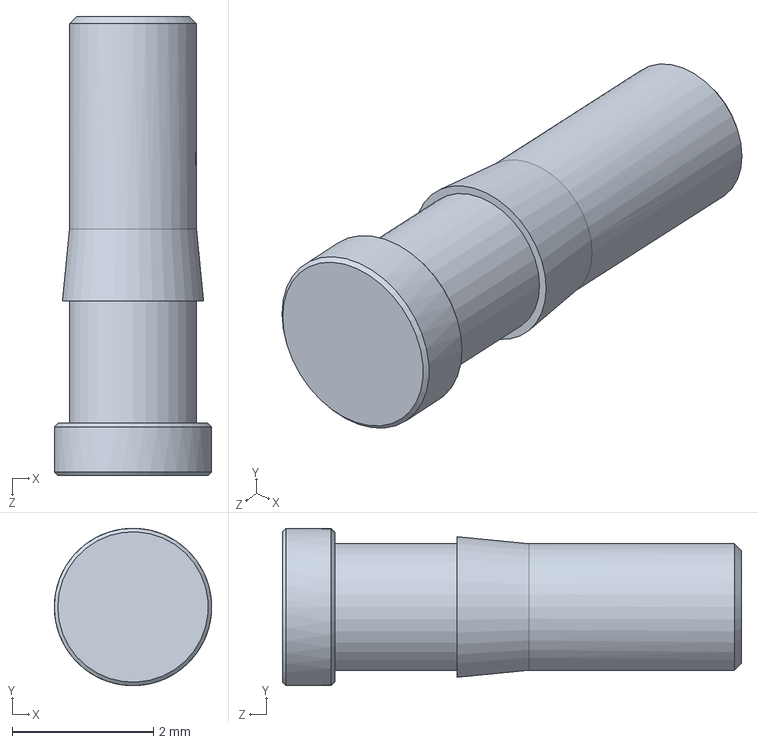
[picture p315: CAD file, 2017-06-28]
Modeles_3D/Solidworks/v2016-2017/Roboblocs-progs/pieces_et_couvercles/contacteur/contact land_sd_mini 3.SLDPRT
2.23 x 2.23 x 6.50 mm
