LibrEduc/RobotBlocs/Modeles_3D/Solidworks/v2016-2017/Roboblocs-robot/Sous systèmes - composants/Regulateur pololu.SLDPRT

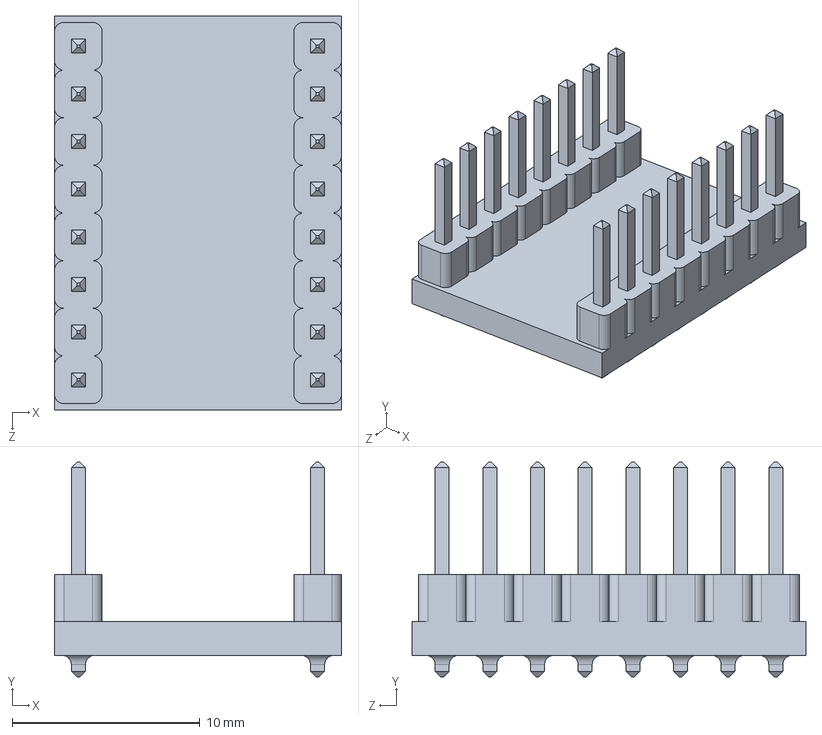
[picture p317: CAD file, 2017-06-28]
Modeles_3D/Solidworks/v2016-2017/Roboblocs-robot/Sous systèmes - composants/Regulateur pololu.SLDPRT
15.3 x 11.4 x 21.0 mm
