LibrEduc/RobotBlocs/Modeles_3D/Solidworks/v2018-2019/Bloc-Prog/Blocprog Corps symetrie.SLDPRT

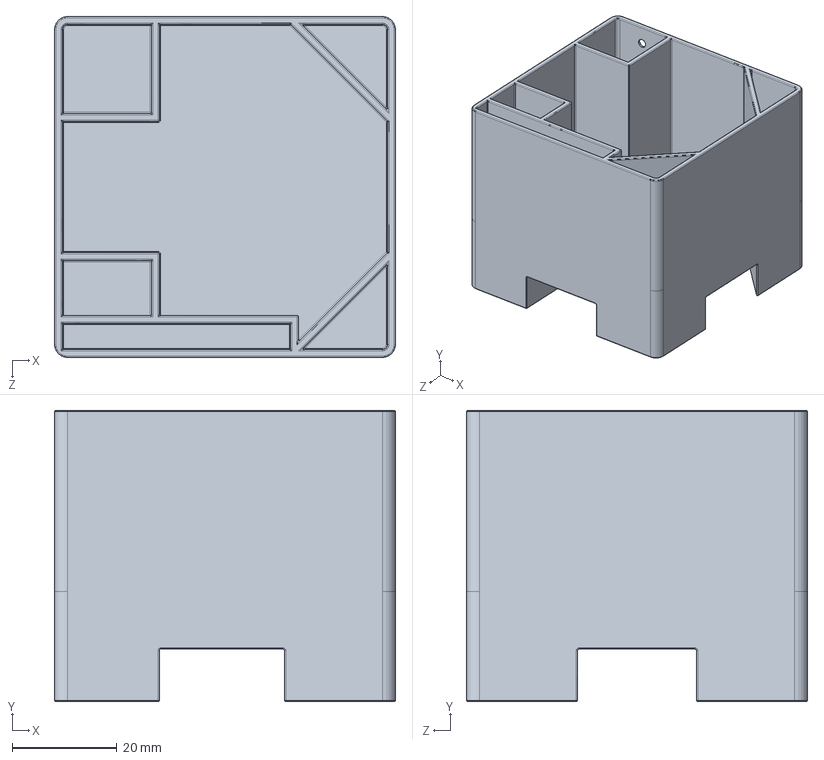
[picture p318: CAD file, 2021-02-01]
Modeles_3D/Solidworks/v2018-2019/Bloc-Prog/Blocprog Corps symetrie.SLDPRT
65.0 x 55.5 x 65.0 mm
