LibrEduc/RobotBlocs/Modeles_3D/Solidworks/v2019-2020/robot/powerbank112.SLDPRT

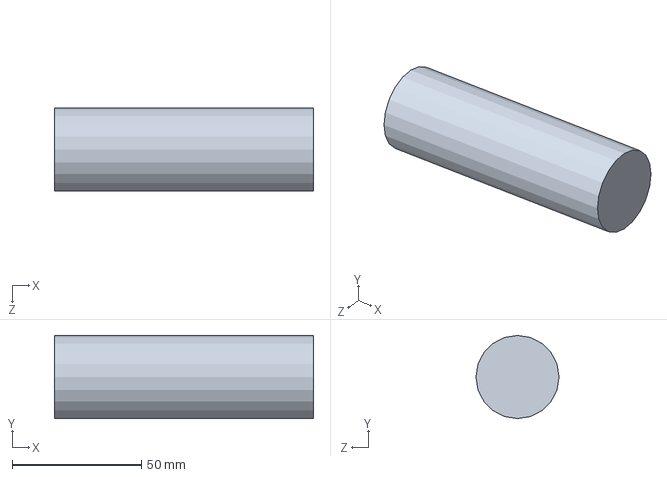
[picture p319: CAD file, 2021-02-01]
Modeles_3D/Solidworks/v2019-2020/robot/powerbank112.SLDPRT
100.3 x 32.2 x 32.2 mm
