LibrEduc/RobotBlocs/Modeles_3D/Solidworks/v2020-2021/BlocsProg1 - Jayson Dauly - Tino  Da Costa - Charles Favier/Grand projet PIECE/3(coter).SLDPRT

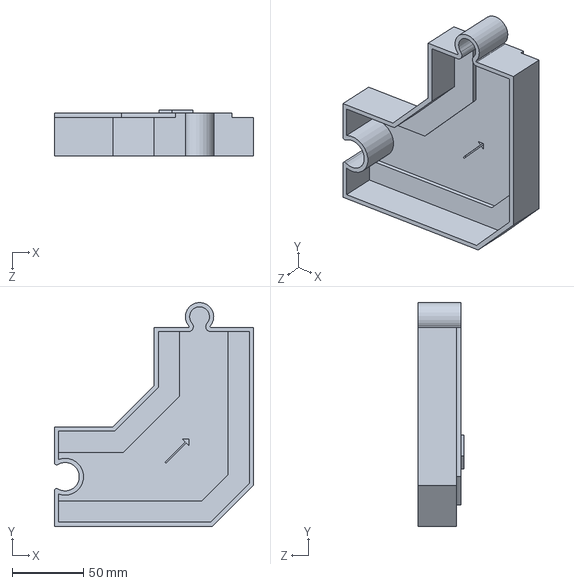
[picture p320: CAD file, 2021-07-25]
Modeles_3D/Solidworks/v2020-2021/BlocsProg1 - Jayson Dauly - Tino Da Costa - Charles Favier/Grand projet PIECE/3(coter).SLDPRT
140.0 x 157.5 x 32.0 mm
