LibrEduc/RobotBlocs/Modeles_3D/Solidworks/v2020-2021/BlocsProg2 - Emile Mesnage - Quentin Gallot - Corentin Gloaguen/Solidworks/Conception/Couvercle.SLDPRT

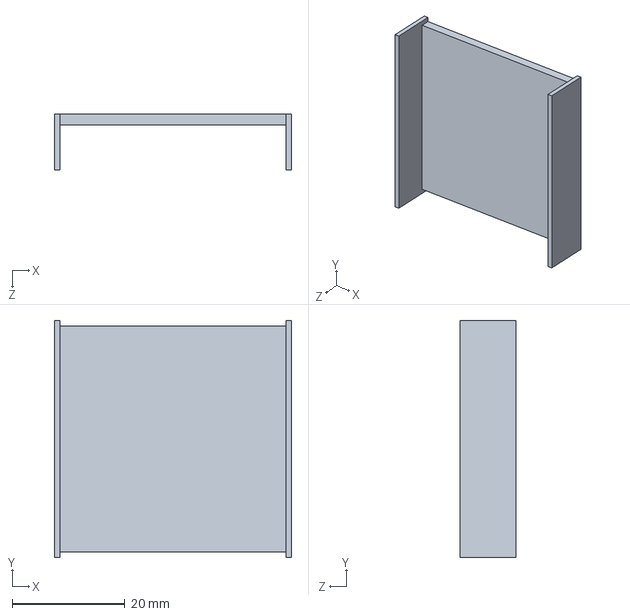
[picture p321: CAD file, 2021-07-25]
Modeles_3D/Solidworks/v2020-2021/BlocsProg2 - Emile Mesnage - Quentin Gallot - Corentin Gloaguen/Solidworks/Conception/Couvercle.SLDPRT
42.0 x 42.0 x 10.0 mm
