LibrEduc/RobotBlocs/Modeles_3D/STL/v2016-2017/Robot - Batterie-1 XT60 Connector Female Connector-1 XT60 Connector Female Contact-1.STL

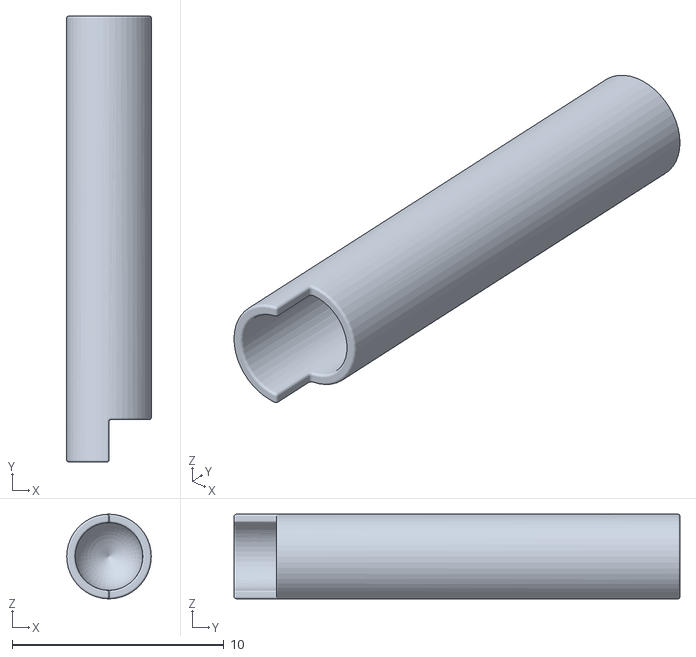
[picture p322: CAD file, 2017-06-28]
Modeles_3D/STL/v2016-2017/Robot - Batterie-1 XT60 Connector Female Connector-1 XT60 Connector Female Contact-1.STL
4.00 x 21.1 x 4.00
