LibrEduc/RobotBlocs/Modeles_3D/STL/v2018-2019/Robot - Coffre^Robot-1.STL

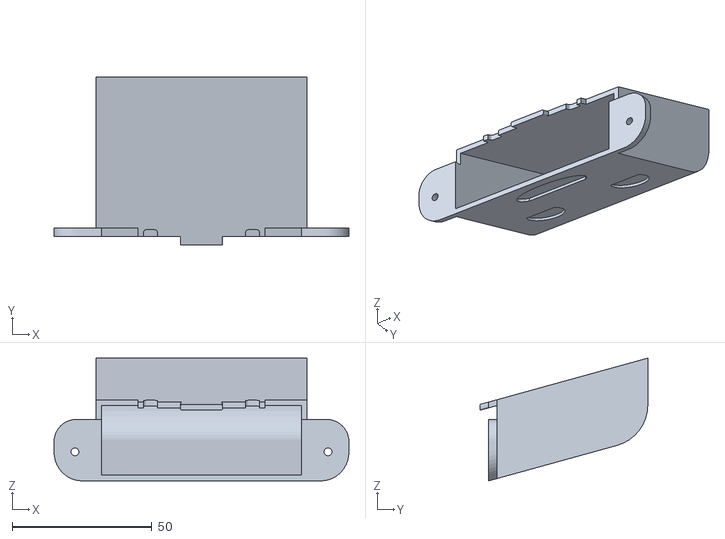
[picture p323: CAD file, 2021-02-01]
Modeles_3D/STL/v2018-2019/Robot - Coffre^Robot-1.STL
105.5 x 60.0 x 43.9
