LibrEduc/RobotBlocs/Projets_complets/v2020-2021/RobotTraceur1 - Pierre Gautier  - Simon Le Moal - Armand Racine  - Gwen Berrou/Conception/Pièces 3D/Robot Tortue.SLDPRT

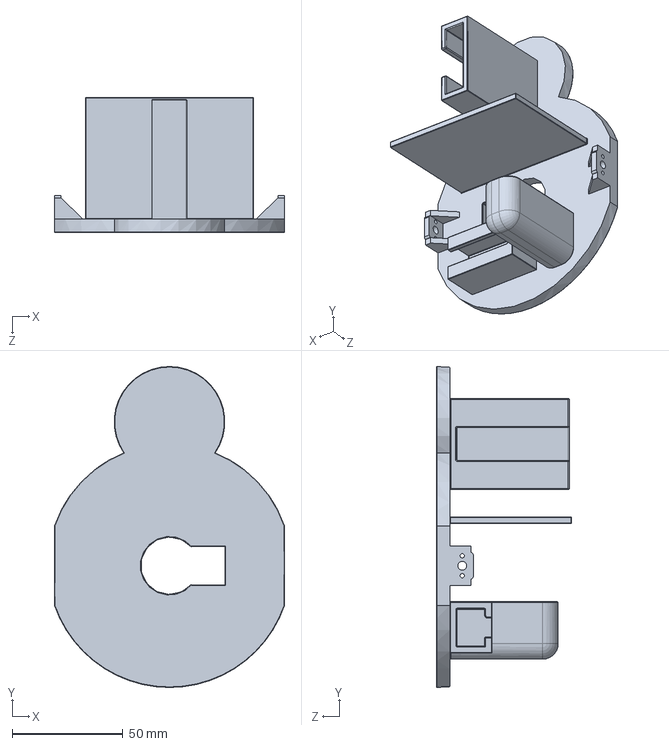
[picture p324: CAD file, 2021-07-25]
Projets_complets/v2020-2021/RobotTraceur1 - Pierre Gautier - Simon Le Moal - Armand Racine - Gwen Berrou/Conception/Pièces 3D/Robot Tortue.SLDPRT
104.0 x 145.0 x 61.0 mm
