LibrEduc/RobotBlocs/Projets_complets/v2020-2021/RobotTraceur2 - Basile Glo - Gaspar Quéméner - Rahkim Gairbekov - Killian Salmon/Pièces/arduino nano.SLDPRT

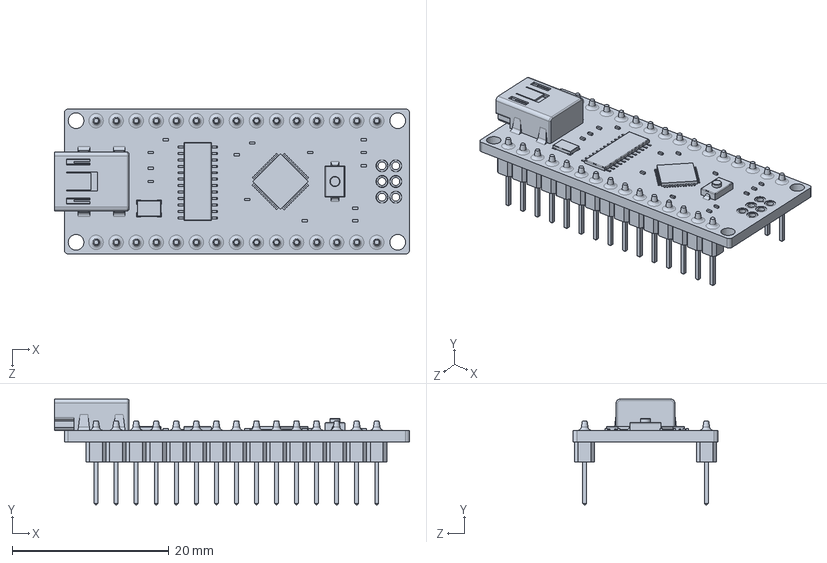
[picture p325: CAD file, 2021-07-25]
Projets_complets/v2020-2021/RobotTraceur2 - Basile Glo - Gaspar Quéméner - Rahkim Gairbekov - Killian Salmon/Pièces/arduino nano.SLDPRT
45.2 x 13.5 x 18.5 mm
