LibrEduc/RobotBlocs/Projets_complets/v2020-2021/RobotTraceur4 - Dylan Morilleau - Arthur Albert - Simon Leservoisier - Marius Bourse - Elouan lucas/pièce crayon/coque.SLDPRT

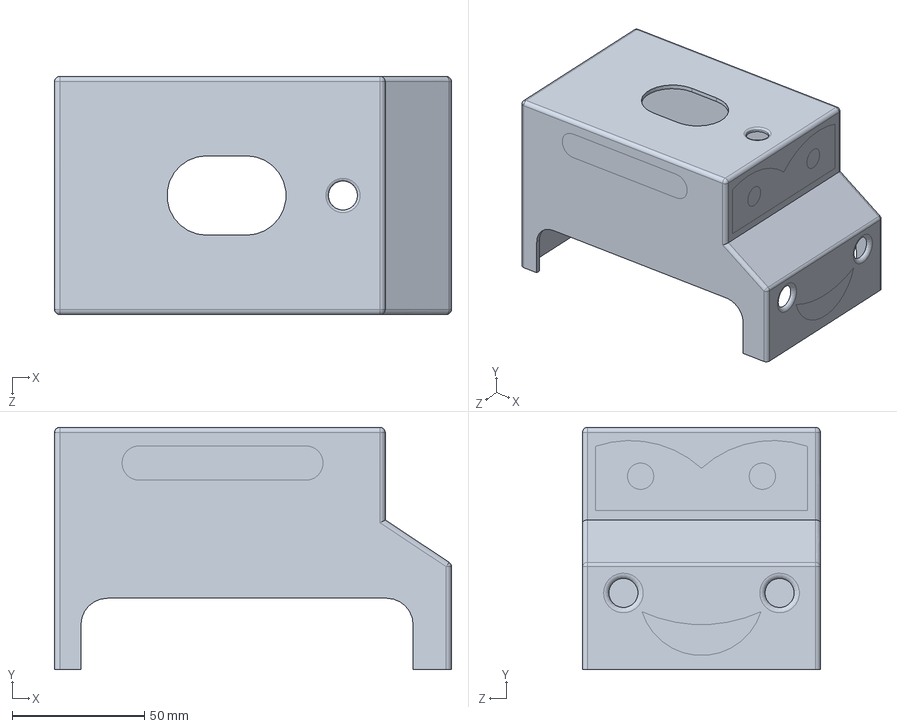
[picture p326: CAD file, 2021-09-23]
Projets_complets/v2020-2021/RobotTraceur4 - Dylan Morilleau - Arthur Albert - Simon Leservoisier - Marius Bourse - Elouan lucas/pièce crayon/coque.SLDPRT
150.0 x 91.6 x 90.0 mm
