LibrEduc/RobotBlocs/Projets_complets/v2020-2021/RobotTraceur4 - Dylan Morilleau - Arthur Albert - Simon Leservoisier - Marius Bourse - Elouan lucas/pièce crayon/pièce crayon/piece servomoteur.sldprt

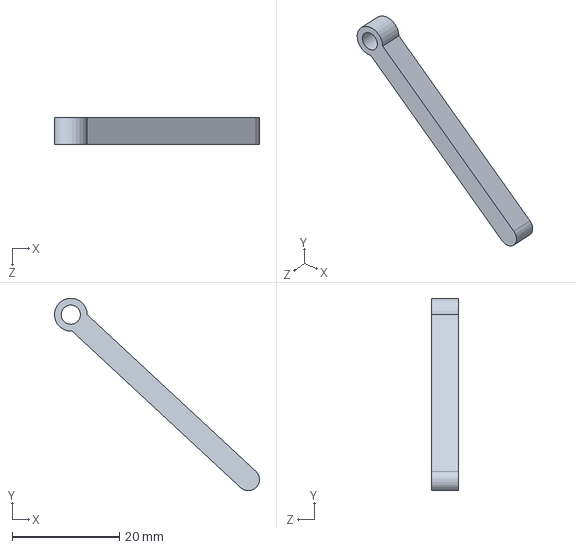
[picture p327: CAD file, 2021-09-23]
Projets_complets/v2020-2021/RobotTraceur4 - Dylan Morilleau - Arthur Albert - Simon Leservoisier - Marius Bourse - Elouan lucas/pièce crayon/pièce crayon/piece servomoteur.sldprt
38.3 x 35.9 x 5.00 mm
