LibrEduc/RobotBlocs/Electronique/protorobotrapido/fixation roue 2.STL

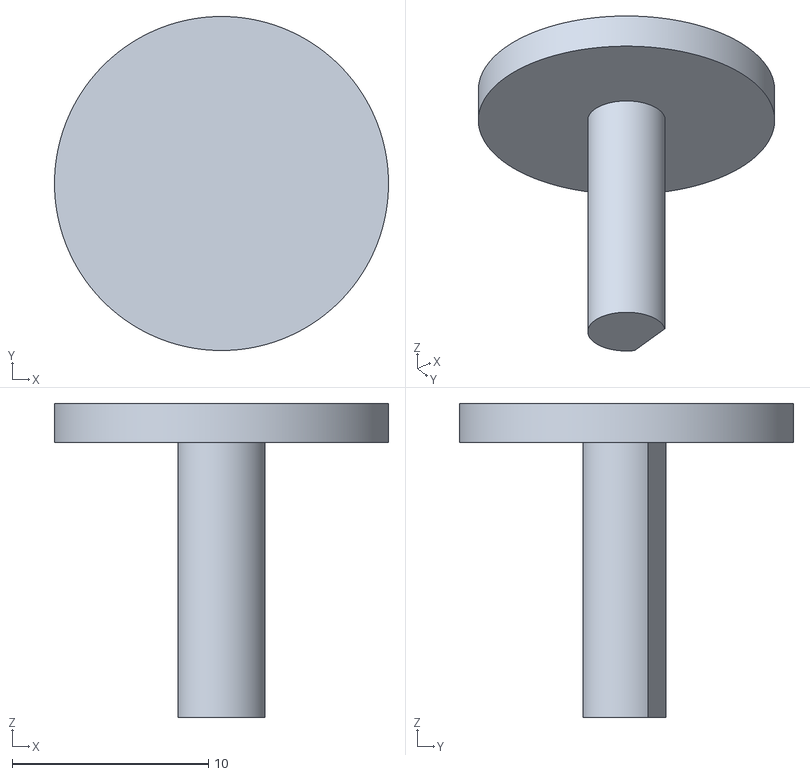
[picture p328: CAD file, 2021-02-01]
Electronique/protorobotrapido/fixation roue 2.STL
17.0 x 17.0 x 16.0
