LibrEduc/RobotBlocs/Modeles_3D/Solidworks/v2016-2017/Roboblocs-progs/pieces_et_couvercles/block.SLDPRT

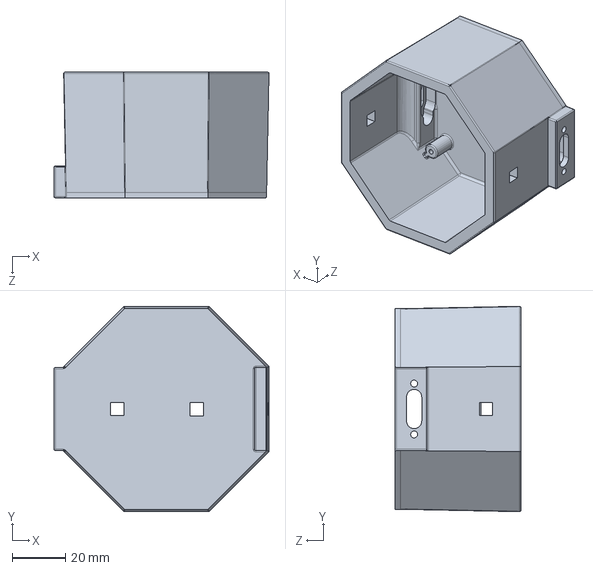
[picture p329: CAD file, 2017-06-28]
Modeles_3D/Solidworks/v2016-2017/Roboblocs-progs/pieces_et_couvercles/block.SLDPRT
80.4 x 76.8 x 47.0 mm
