LibrEduc/RobotBlocs/Modeles_3D/Solidworks/v2016-2017/Roboblocs-progs/pieces_et_couvercles/contacteur/contact_sd_mini.sldprt

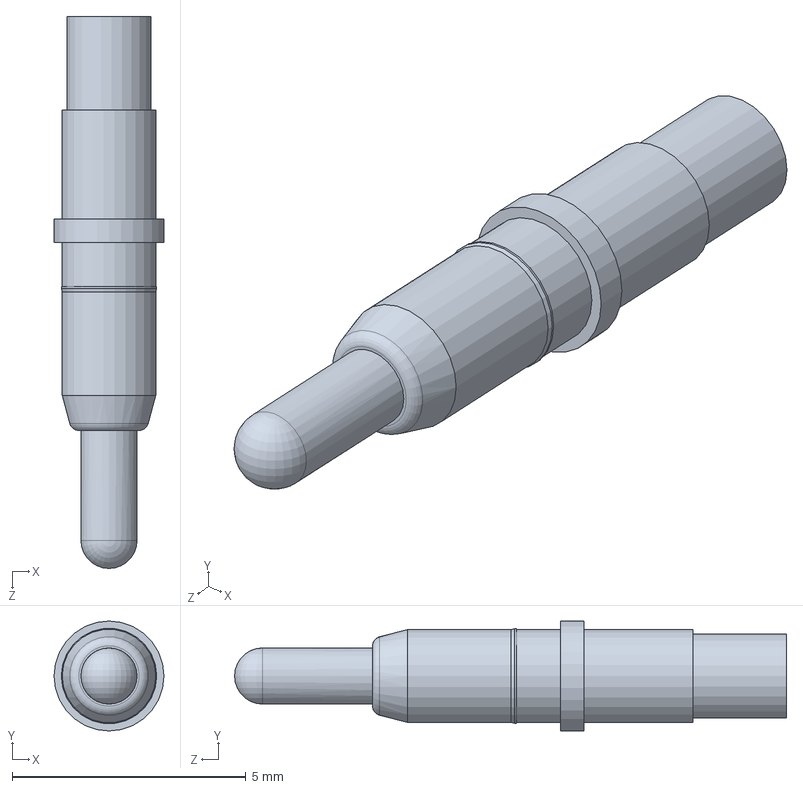
[picture p330: CAD file, 2017-06-28]
Modeles_3D/Solidworks/v2016-2017/Roboblocs-progs/pieces_et_couvercles/contacteur/contact_sd_mini.sldprt
2.35 x 2.35 x 11.8 mm
