LibrEduc/RobotBlocs/Modeles_3D/Solidworks/v2016-2017/Roboblocs-robot/pieces/griffe de guidage.sldprt

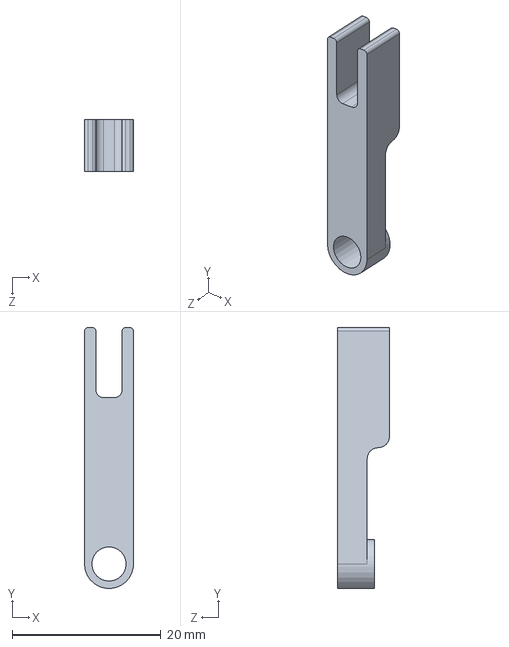
[picture p331: CAD file, 2017-06-28]
Modeles_3D/Solidworks/v2016-2017/Roboblocs-robot/pieces/griffe de guidage.sldprt
6.60 x 35.1 x 7.00 mm
