LibrEduc/RobotBlocs/Modeles_3D/Solidworks/v2018-2019/Bloc-maître/coté droit de loco.SLDPRT

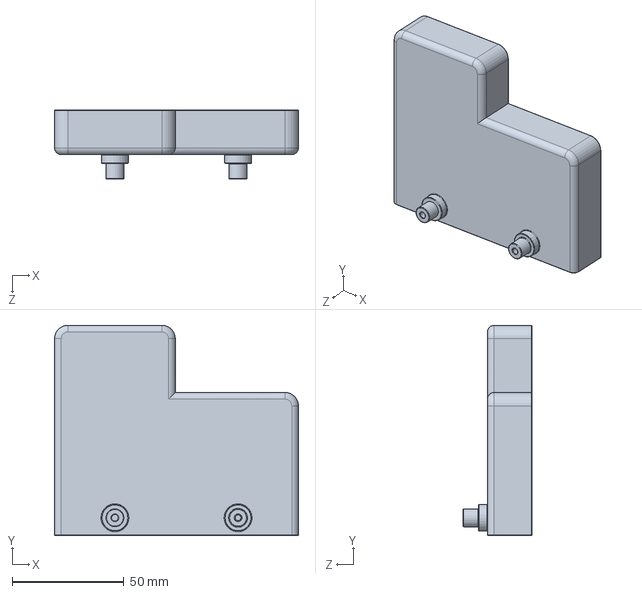
[picture p333: CAD file, 2021-02-01]
Modeles_3D/Solidworks/v2018-2019/Bloc-maître/coté droit de loco.SLDPRT
109.0 x 94.0 x 31.0 mm
