LibrEduc/RobotBlocs/Modeles_3D/Solidworks/v2018-2019/Bloc-Prog/Couvercle.sldprt

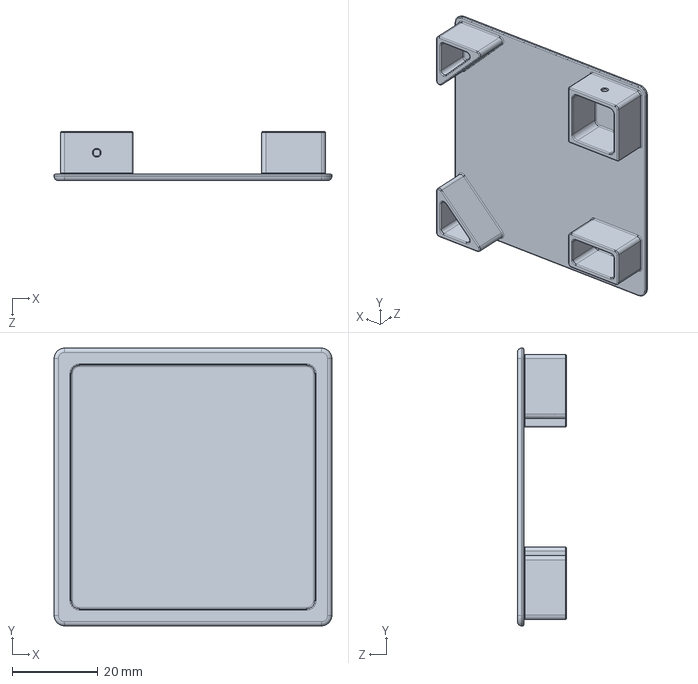
[picture p334: CAD file, 2021-02-01]
Modeles_3D/Solidworks/v2018-2019/Bloc-Prog/Couvercle.sldprt
65.0 x 65.0 x 11.5 mm
