LibrEduc/RobotBlocs/Modeles_3D/Solidworks/v2018-2019/Robot/SG90 - Micro Servo 9g - Tower Pro.2.SLDPRT

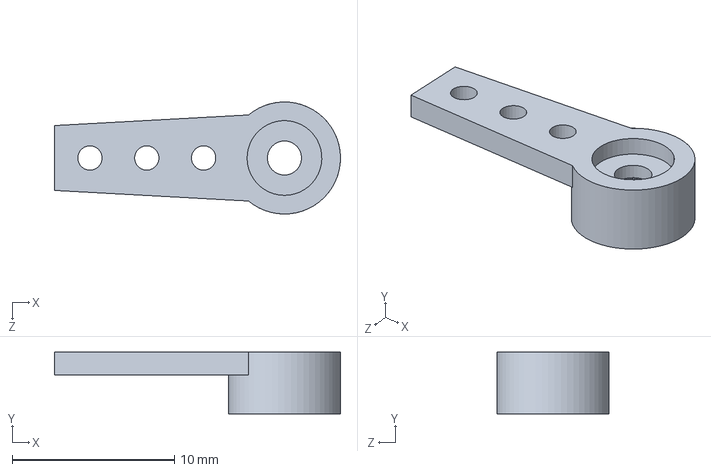
[picture p335: CAD file, 2021-02-01]
Modeles_3D/Solidworks/v2018-2019/Robot/SG90 - Micro Servo 9g - Tower Pro.2.SLDPRT
17.6 x 3.80 x 6.90 mm
