LibrEduc/RobotBlocs/Modeles_3D/Solidworks/v2019-2020/robot/189 RESISTOR PACK.SLDPRT

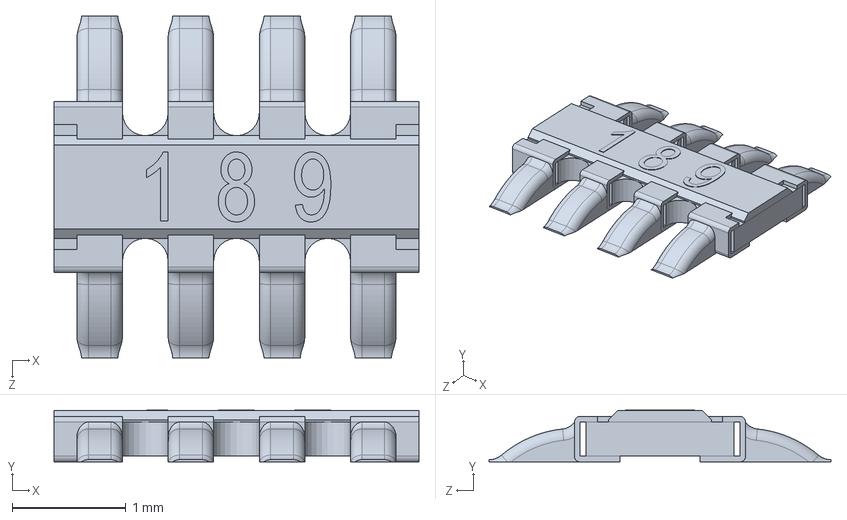
[picture p336: CAD file, 2021-02-01]
Modeles_3D/Solidworks/v2019-2020/robot/189 RESISTOR PACK.SLDPRT
3.20 x 0.455 x 3.00 mm
