LibrEduc/RobotBlocs/Modeles_3D/STL/v2016-2017/Robot - servo moteur stylo-1.STL

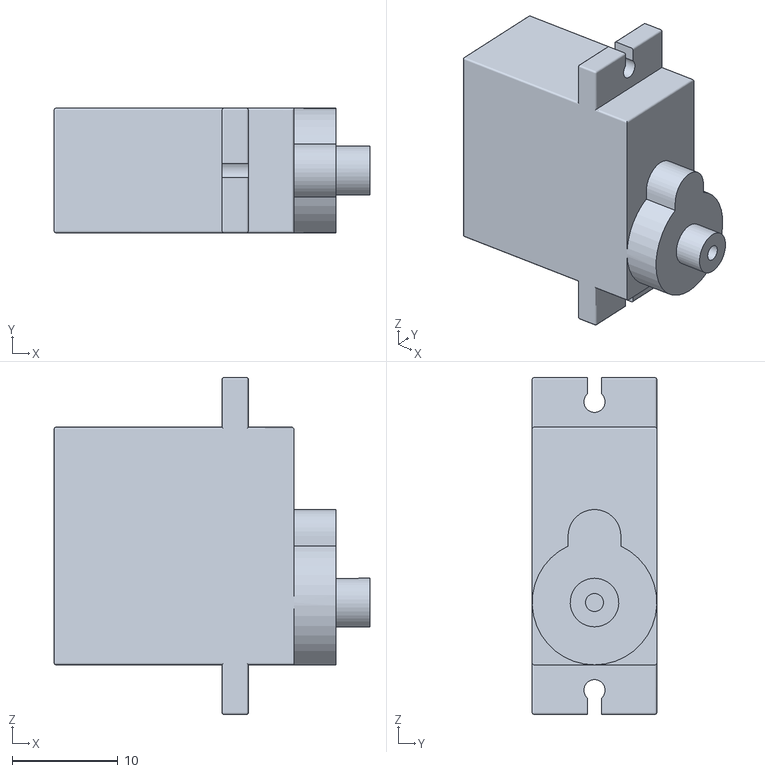
[picture p337: CAD file, 2017-06-28]
Modeles_3D/STL/v2016-2017/Robot - servo moteur stylo-1.STL
29.9 x 11.8 x 31.9
