LibrEduc/RobotBlocs/Modeles_3D/STL/v2018-2019/Robot - proto Robot-1.STL

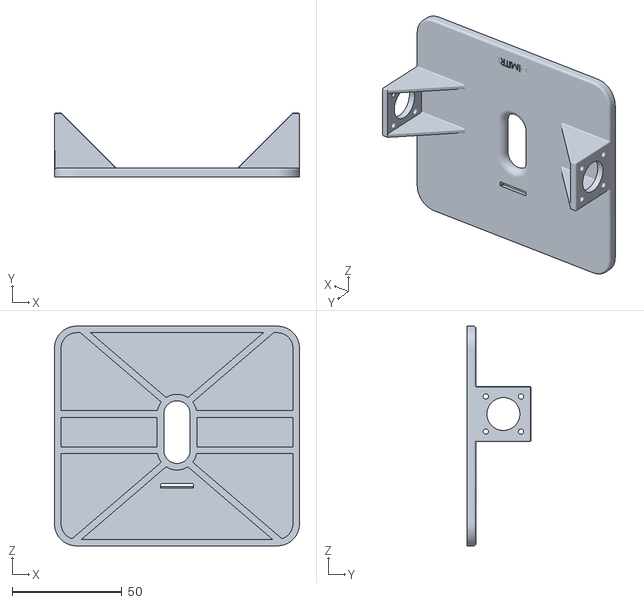
[picture p338: CAD file, 2021-02-01]
Modeles_3D/STL/v2018-2019/Robot - proto Robot-1.STL
111.5 x 29.0 x 100.0
