LibrEduc/RobotBlocs/Modeles_3D/STL/v2020-2021/RobotTraceur1/bloc cerveau moteur.STL

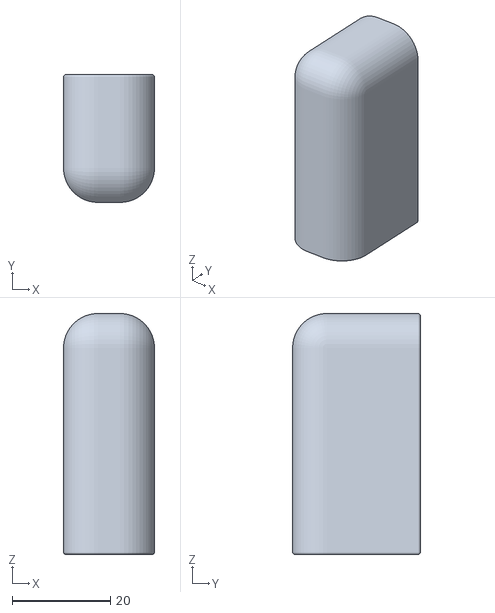
[picture p339: CAD file, 2021-07-25]
Modeles_3D/STL/v2020-2021/RobotTraceur1/bloc cerveau moteur.STL
18.5 x 26.0 x 49.0
