LibrEduc/RobotBlocs/Projets_complets/v2020-2021/RobotTraceur2 - Basile Glo - Gaspar Quéméner - Rahkim Gairbekov - Killian Salmon/Pièces/support attache crayon.SLDPRT

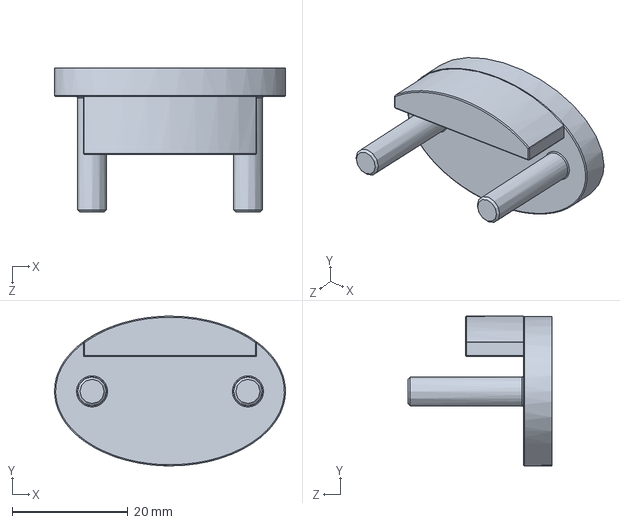
[picture p341: CAD file, 2021-07-25]
Projets_complets/v2020-2021/RobotTraceur2 - Basile Glo - Gaspar Quéméner - Rahkim Gairbekov - Killian Salmon/Pièces/support attache crayon.SLDPRT
40.0 x 25.9 x 25.0 mm
