LibrEduc/RobotBlocs/Modeles_3D/Solidworks/v2016-2017/Roboblocs-progs/pieces_et_couvercles/contacteur/body_4 hole_mini.sldprt

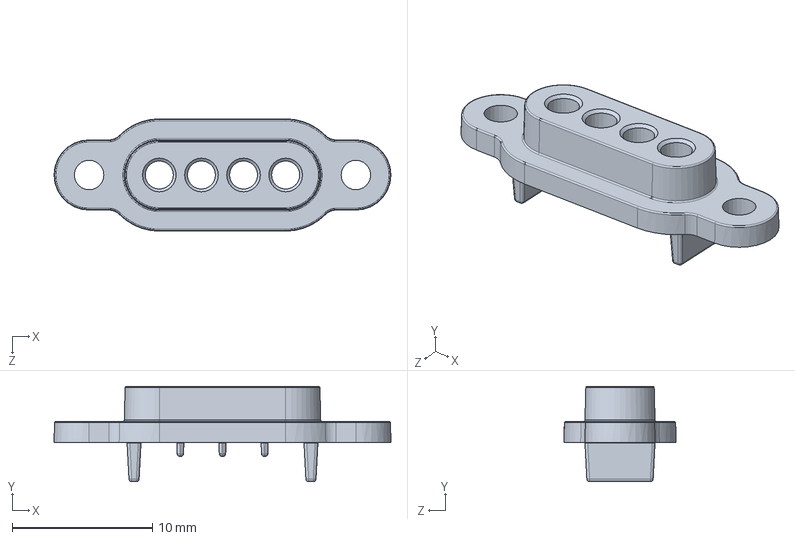
[picture p343: CAD file, 2017-06-28]
Modeles_3D/Solidworks/v2016-2017/Roboblocs-progs/pieces_et_couvercles/contacteur/body_4 hole_mini.sldprt
24.0 x 6.80 x 8.00 mm
