LibrEduc/RobotBlocs/Modeles_3D/Solidworks/v2016-2017/Roboblocs-robot/pieces/Tube translatant v2.sldprt

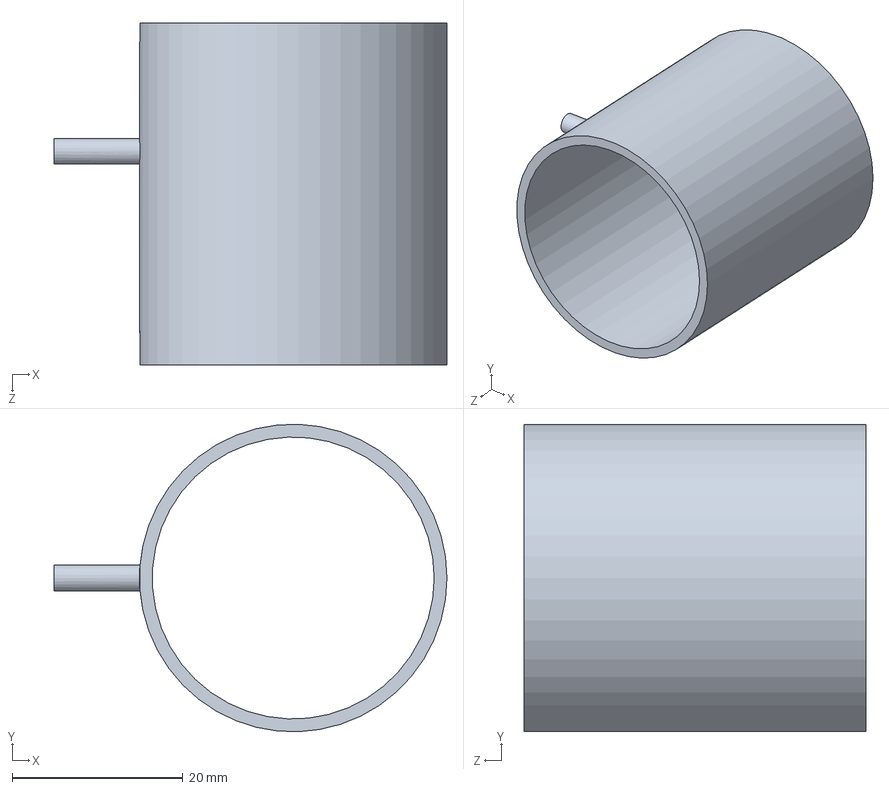
[picture p344: CAD file, 2017-06-28]
Modeles_3D/Solidworks/v2016-2017/Roboblocs-robot/pieces/Tube translatant v2.sldprt
46.0 x 36.0 x 40.0 mm
