LibrEduc/RobotBlocs/Modeles_3D/Solidworks/v2019-2020/robot/ftdi FT232rl.SLDPRT

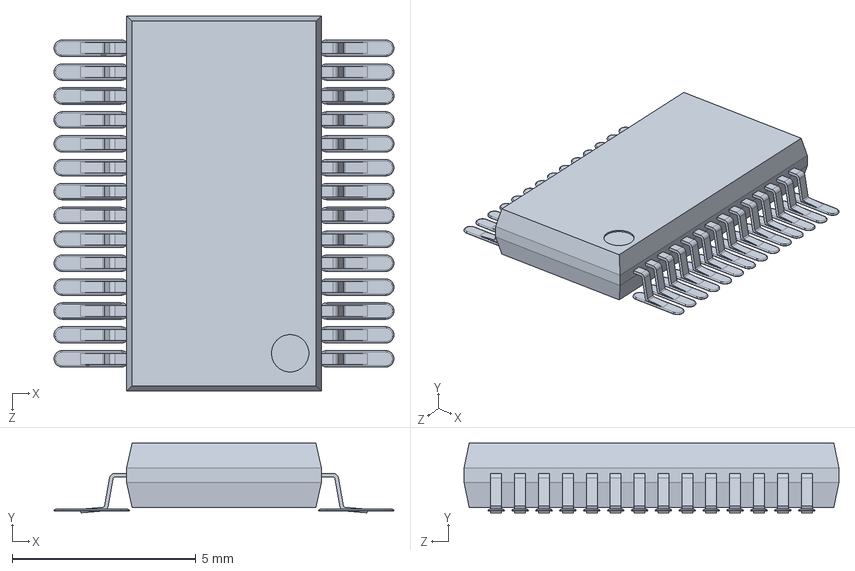
[picture p347: CAD file, 2021-02-01]
Modeles_3D/Solidworks/v2019-2020/robot/ftdi FT232rl.SLDPRT
9.25 x 1.90 x 10.2 mm
