LibrEduc/RobotBlocs/Modeles_3D/Solidworks/v2020-2021/BlocsProg1 - Jayson Dauly - Tino  Da Costa - Charles Favier/Grand projet PIECE/4 (Bloc maitre).SLDPRT

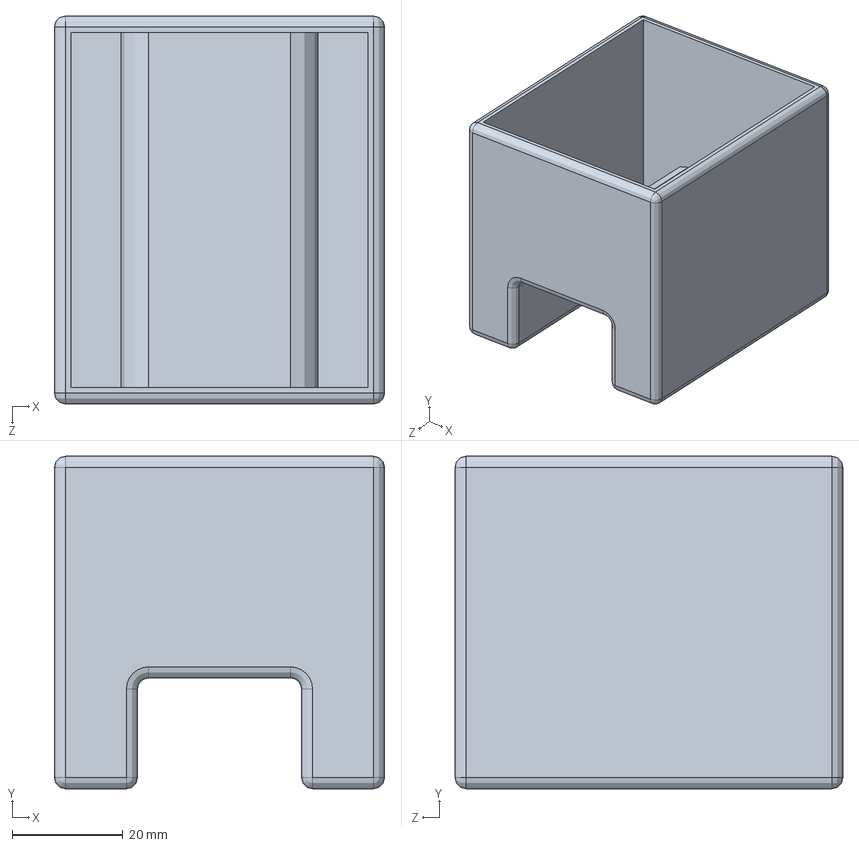
[picture p348: CAD file, 2021-07-25]
Modeles_3D/Solidworks/v2020-2021/BlocsProg1 - Jayson Dauly - Tino Da Costa - Charles Favier/Grand projet PIECE/4 (Bloc maitre).SLDPRT
59.6 x 60.0 x 70.0 mm
