LibrEduc/RobotBlocs/Modeles_3D/Solidworks/v2020-2021/BlocsProg2 - Emile Mesnage - Quentin Gallot - Corentin Gloaguen/Solidworks/Conception/Bloc maitre.SLDPRT

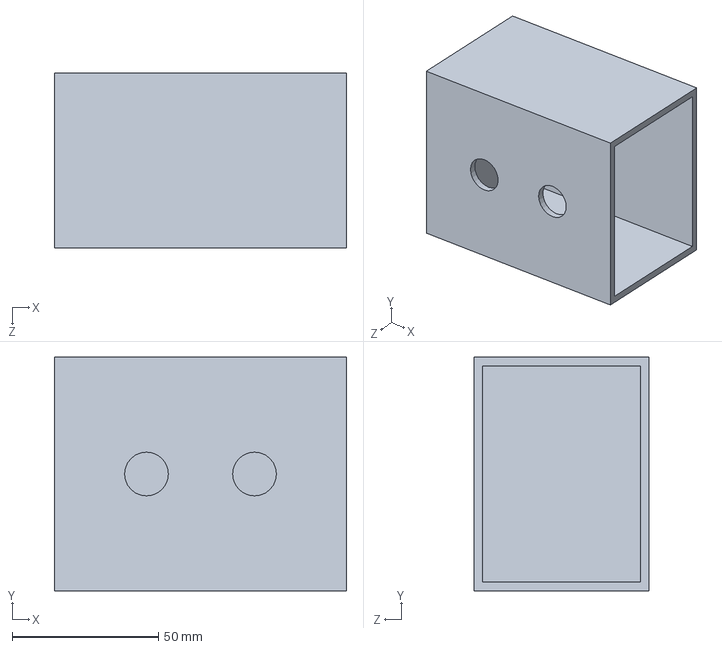
[picture p349: CAD file, 2021-07-25]
Modeles_3D/Solidworks/v2020-2021/BlocsProg2 - Emile Mesnage - Quentin Gallot - Corentin Gloaguen/Solidworks/Conception/Bloc maitre.SLDPRT
100.0 x 80.0 x 60.0 mm
