LibrEduc/RobotBlocs/Modeles_3D/STEP/v2016-2017/SWIFT DOCK MINI-4-SC.STEP

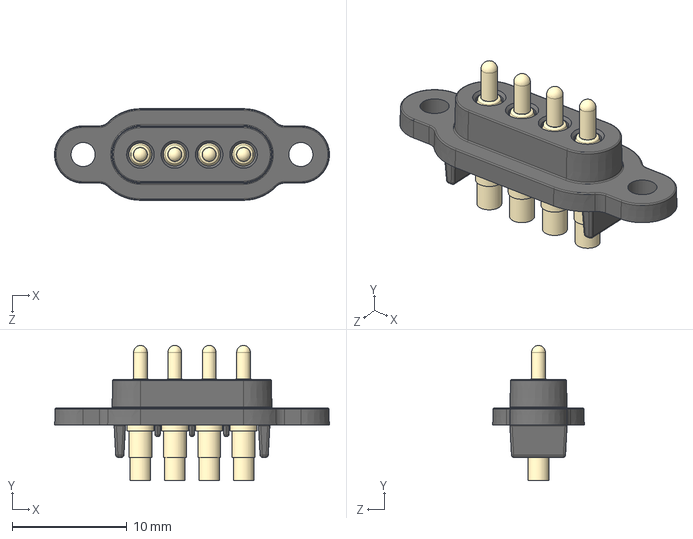
[picture p350: CAD file, 2017-06-28]
Modeles_3D/STEP/v2016-2017/SWIFT DOCK MINI-4-SC.STEP
24.0 x 11.8 x 8.00 mm
body_4 hole_mini
contact_sd_mini x 4
