LibrEduc/RobotBlocs/Modeles_3D/STL/v2018-2019/Robot - Roue-1.STL

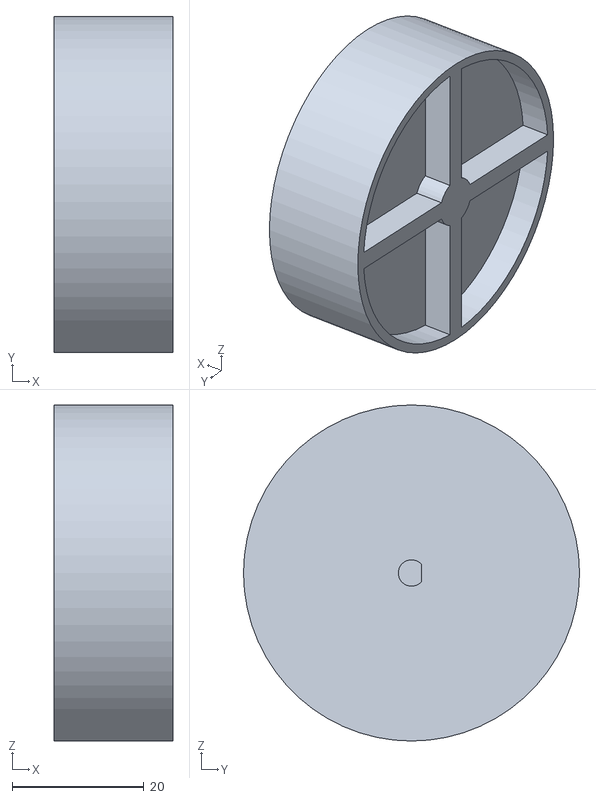
[picture p351: CAD file, 2021-02-01]
Modeles_3D/STL/v2018-2019/Robot - Roue-1.STL
18.0 x 51.0 x 51.0
