LibrEduc/RobotBlocs/Modeles_3D/STL/v2020-2021/RobotTraceur1/bloc ressort.STL

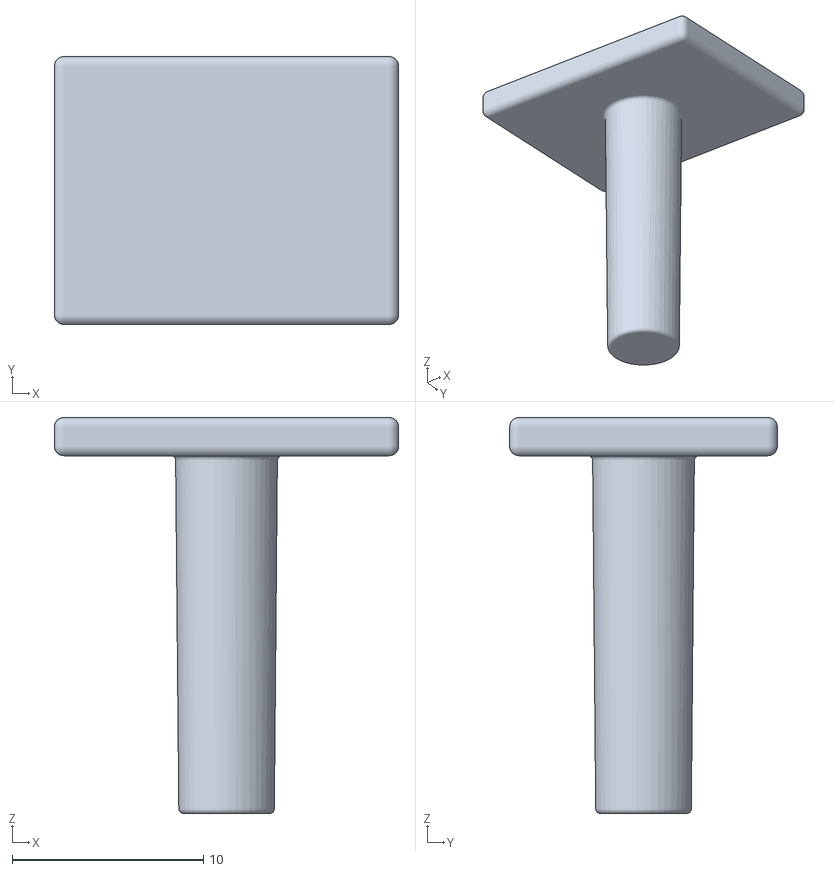
[picture p352: CAD file, 2021-07-25]
Modeles_3D/STL/v2020-2021/RobotTraceur1/bloc ressort.STL
18.0 x 14.0 x 20.7
