LibrEduc/RobotBlocs/Modeles_3D/Solidworks/v2016-2017/Roboblocs-progs/pieces_et_couvercles/contacteur/circuit imprime.SLDPRT

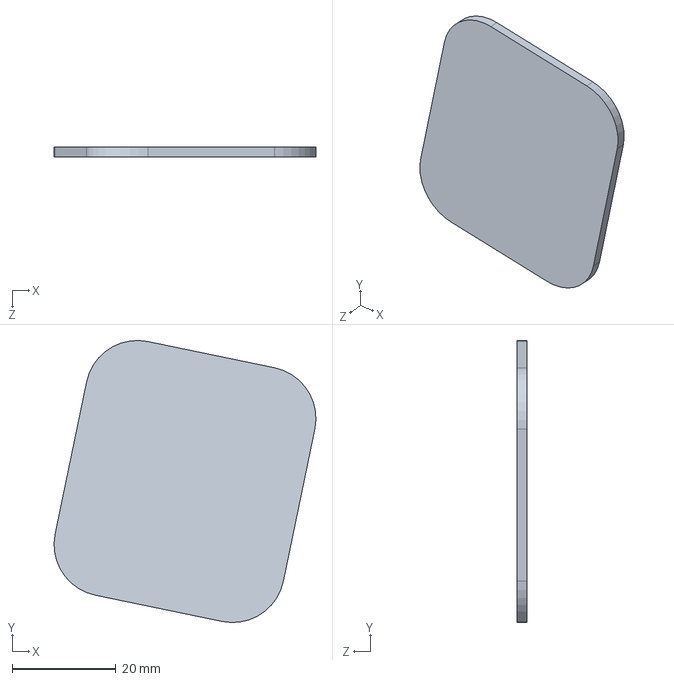
[picture p355: CAD file, 2017-06-28]
Modeles_3D/Solidworks/v2016-2017/Roboblocs-progs/pieces_et_couvercles/contacteur/circuit imprime.SLDPRT
50.6 x 54.4 x 2.00 mm
