LibrEduc/RobotBlocs/Modeles_3D/Solidworks/v2016-2017/Roboblocs-progs/pieces_et_couvercles/fonction tout droit.SLDPRT

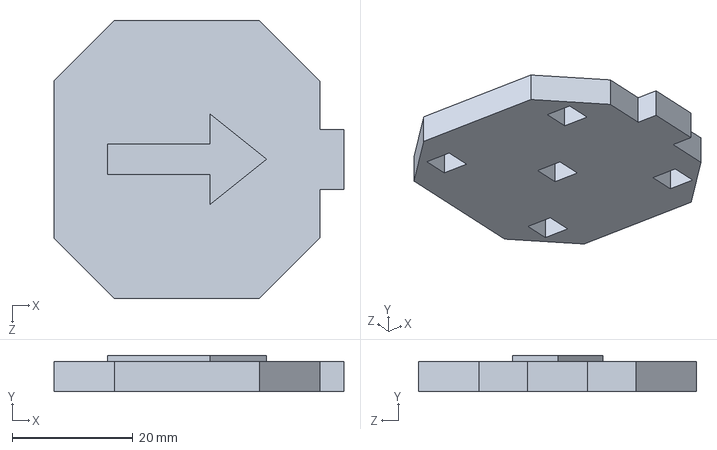
[picture p356: CAD file, 2017-06-28]
Modeles_3D/Solidworks/v2016-2017/Roboblocs-progs/pieces_et_couvercles/fonction tout droit.SLDPRT
48.0 x 6.00 x 46.0 mm
