LibrEduc/RobotBlocs/Modeles_3D/Solidworks/v2016-2017/Roboblocs-robot/pieces/TUBE translatant.SLDPRT

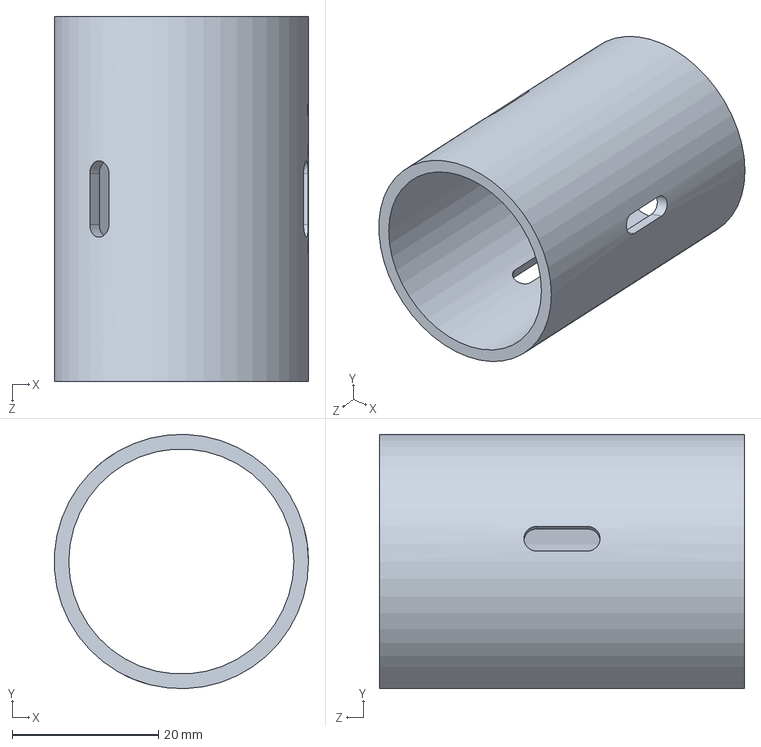
[picture p357: CAD file, 2017-06-28]
Modeles_3D/Solidworks/v2016-2017/Roboblocs-robot/pieces/TUBE translatant.SLDPRT
34.8 x 34.8 x 50.0 mm
