LibrEduc/RobotBlocs/Modeles_3D/Solidworks/v2016-2017/Roboblocs-robot/Sous systèmes - composants/module bluetooth hc05.SLDPRT

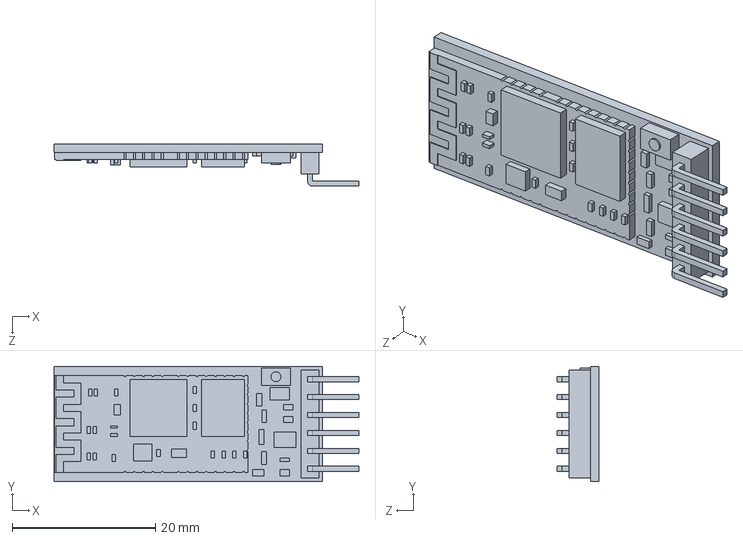
[picture p358: CAD file, 2017-06-28]
Modeles_3D/Solidworks/v2016-2017/Roboblocs-robot/Sous systèmes - composants/module bluetooth hc05.SLDPRT
42.6 x 16.1 x 5.90 mm
