LibrEduc/RobotBlocs/Modeles_3D/Solidworks/v2018-2019/Robot/SG90 - Micro Servo 9g - Tower Pro.6.SLDPRT

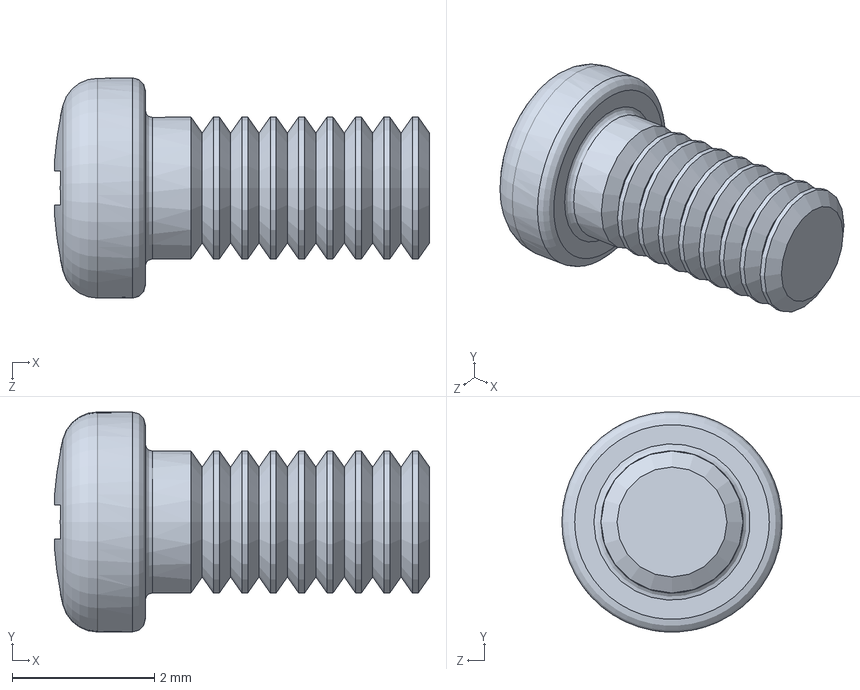
[picture p359: CAD file, 2021-02-01]
Modeles_3D/Solidworks/v2018-2019/Robot/SG90 - Micro Servo 9g - Tower Pro.6.SLDPRT
5.28 x 3.10 x 3.10 mm
