LibrEduc/RobotBlocs/Modeles_3D/Solidworks/v2020-2021/BlocsProg2 - Emile Mesnage - Quentin Gallot - Corentin Gloaguen/Solidworks/Conception/Bloc Final projet.SLDPRT

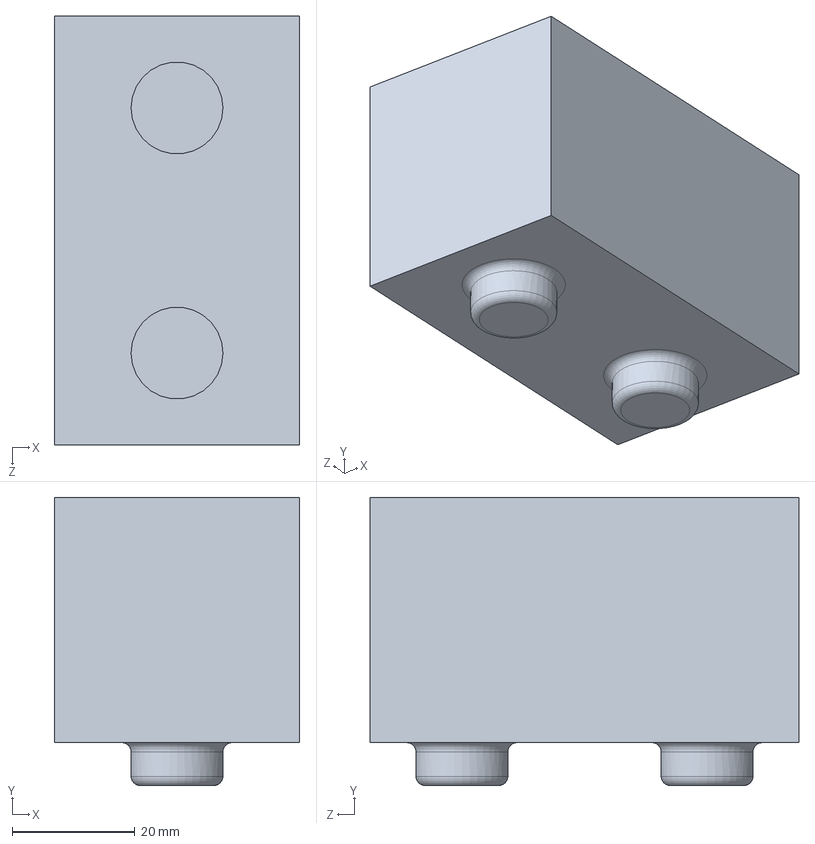
[picture p360: CAD file, 2021-07-25]
Modeles_3D/Solidworks/v2020-2021/BlocsProg2 - Emile Mesnage - Quentin Gallot - Corentin Gloaguen/Solidworks/Conception/Bloc Final projet.SLDPRT
40.0 x 47.0 x 70.0 mm
