LibrEduc/RobotBlocs/Modeles_3D/STL/v2016-2017/Robot - Chassis robot-1.STL

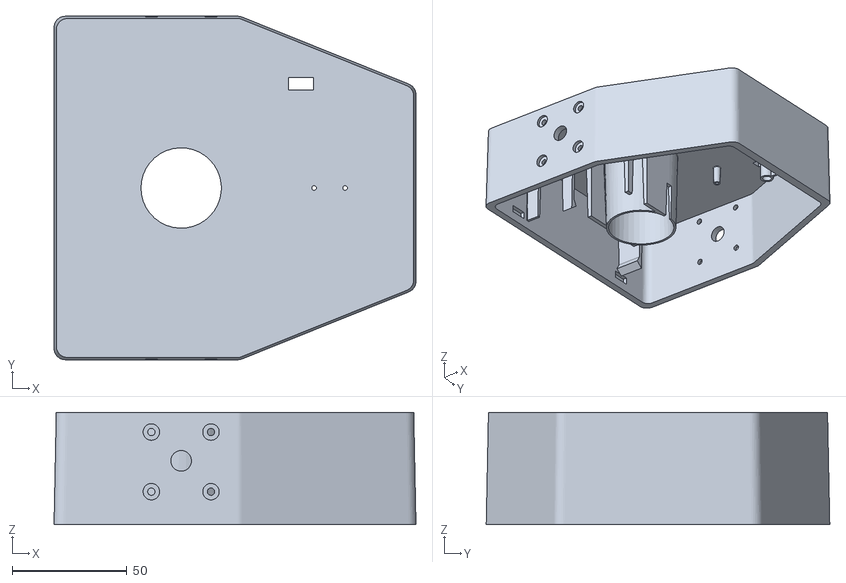
[picture p361: CAD file, 2017-06-28]
Modeles_3D/STL/v2016-2017/Robot - Chassis robot-1.STL
157.8 x 149.8 x 49.0
