LibrEduc/RobotBlocs/Modeles_3D/STL/v2020-2021/RobotTraceur1/bloc batterie.STL

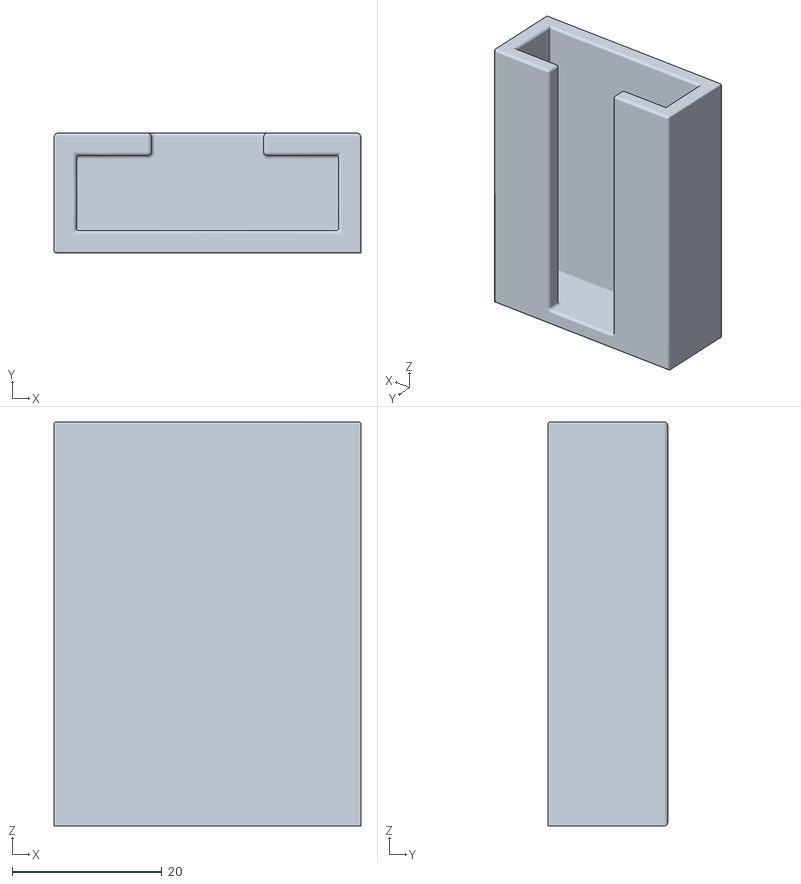
[picture p362: CAD file, 2021-07-25]
Modeles_3D/STL/v2020-2021/RobotTraceur1/bloc batterie.STL
41.0 x 16.0 x 54.0
