LibrEduc/RobotBlocs/Modeles_3D/Solidworks/v2016-2017/Roboblocs-progs/pieces_et_couvercles/contacteur/land body_4 hole_mini 2.SLDPRT

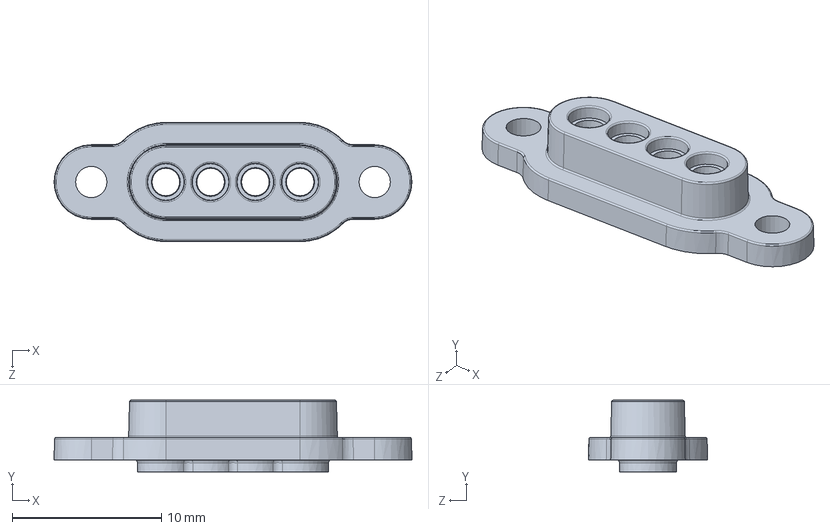
[picture p365: CAD file, 2017-06-28]
Modeles_3D/Solidworks/v2016-2017/Roboblocs-progs/pieces_et_couvercles/contacteur/land body_4 hole_mini 2.SLDPRT
24.0 x 4.80 x 8.00 mm
