LibrEduc/RobotBlocs/Modeles_3D/Solidworks/v2016-2017/Roboblocs-robot/pieces/moteur pas à pas.SLDPRT

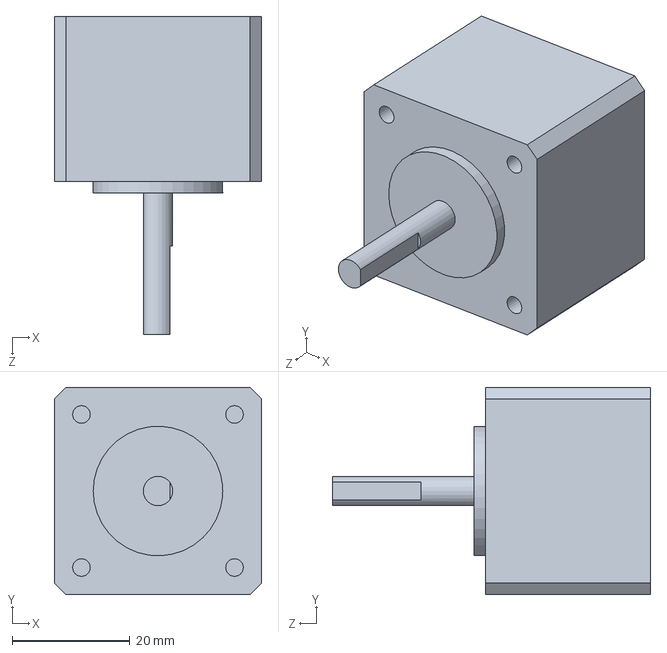
[picture p367: CAD file, 2017-06-28]
Modeles_3D/Solidworks/v2016-2017/Roboblocs-robot/pieces/moteur pas à pas.SLDPRT
35.2 x 35.2 x 54.0 mm
