LibrEduc/RobotBlocs/Modeles_3D/Solidworks/v2016-2017/Roboblocs-robot/Sous systèmes - composants/arduino uno/lp2985dgkr.SLDPRT

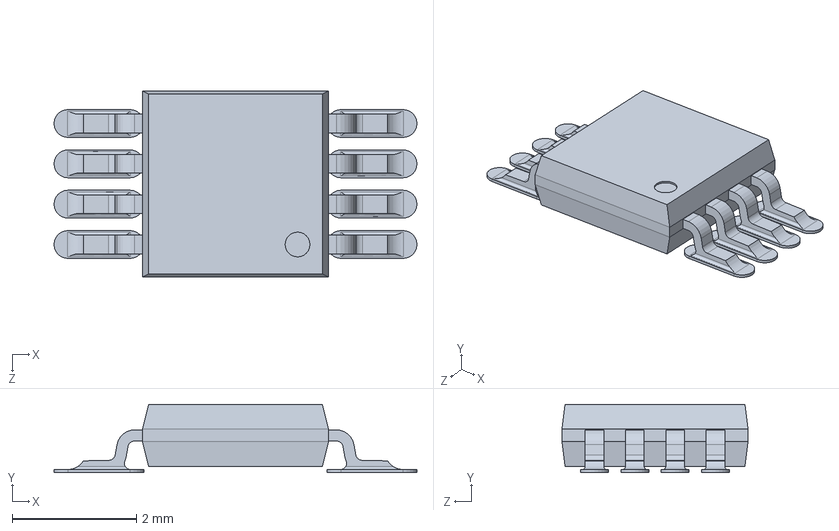
[picture p368: CAD file, 2017-06-28]
Modeles_3D/Solidworks/v2016-2017/Roboblocs-robot/Sous systèmes - composants/arduino uno/lp2985dgkr.SLDPRT
5.85 x 1.10 x 3.00 mm
