LibrEduc/RobotBlocs/Modeles_3D/Solidworks/v2016-2017/Roboblocs-robot/Sous systèmes - composants/roue en mousse.SLDPRT

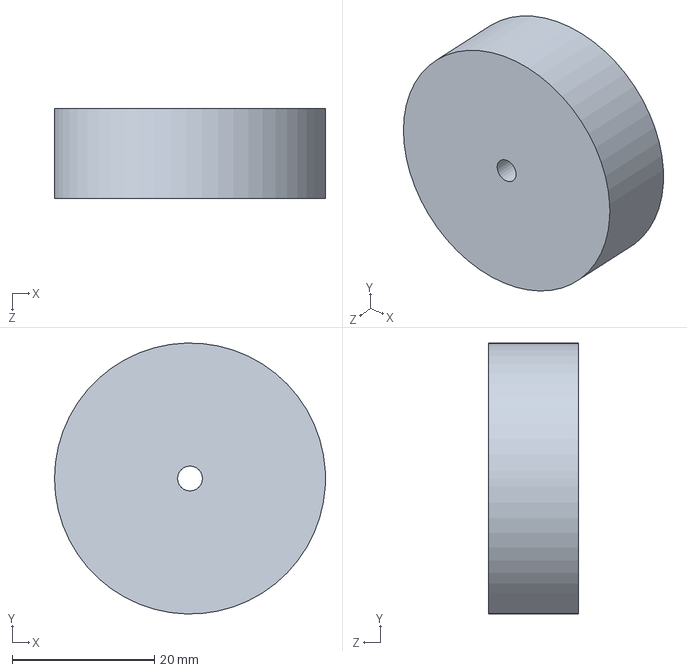
[picture p369: CAD file, 2017-06-28]
Modeles_3D/Solidworks/v2016-2017/Roboblocs-robot/Sous systèmes - composants/roue en mousse.SLDPRT
38.1 x 38.1 x 12.7 mm
