LibrEduc/RobotBlocs/Modeles_3D/Solidworks/v2018-2019/Robot/arbe moteur.SLDPRT

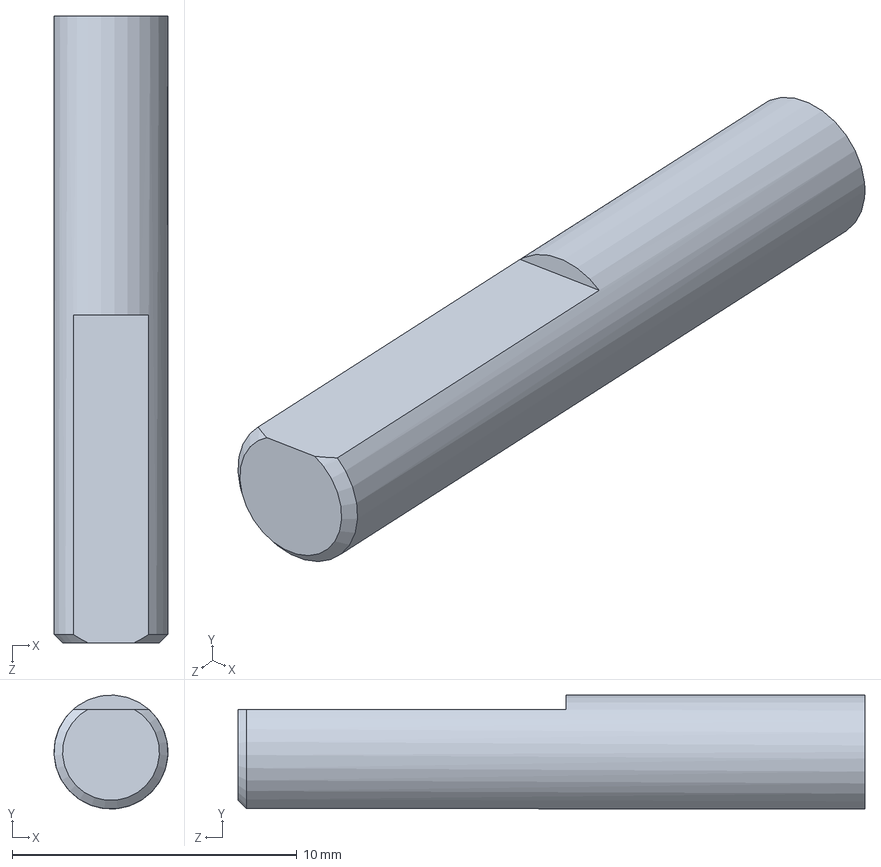
[picture p370: CAD file, 2021-02-01]
Modeles_3D/Solidworks/v2018-2019/Robot/arbe moteur.SLDPRT
4.00 x 3.99 x 22.0 mm
