LibrEduc/RobotBlocs/Modeles_3D/Solidworks/v2019-2020/robot/NANO DIODE.SLDPRT

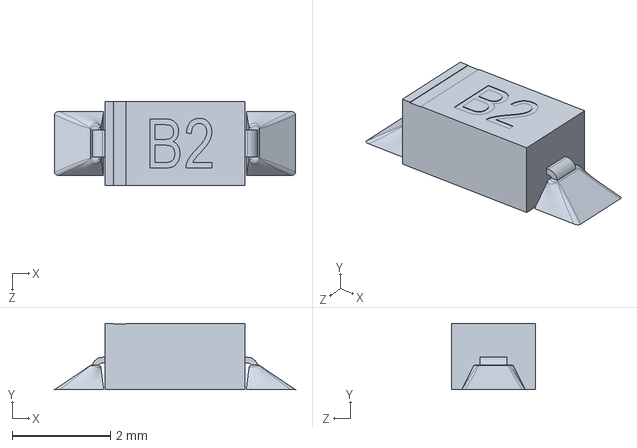
[picture p371: CAD file, 2021-02-01]
Modeles_3D/Solidworks/v2019-2020/robot/NANO DIODE.SLDPRT
4.90 x 1.35 x 1.70 mm
