LibrEduc/RobotBlocs/Modeles_3D/Solidworks/v2020-2021/BlocsProg1 - Jayson Dauly - Tino  Da Costa - Charles Favier/Grand projet PIECE/toit.SLDPRT

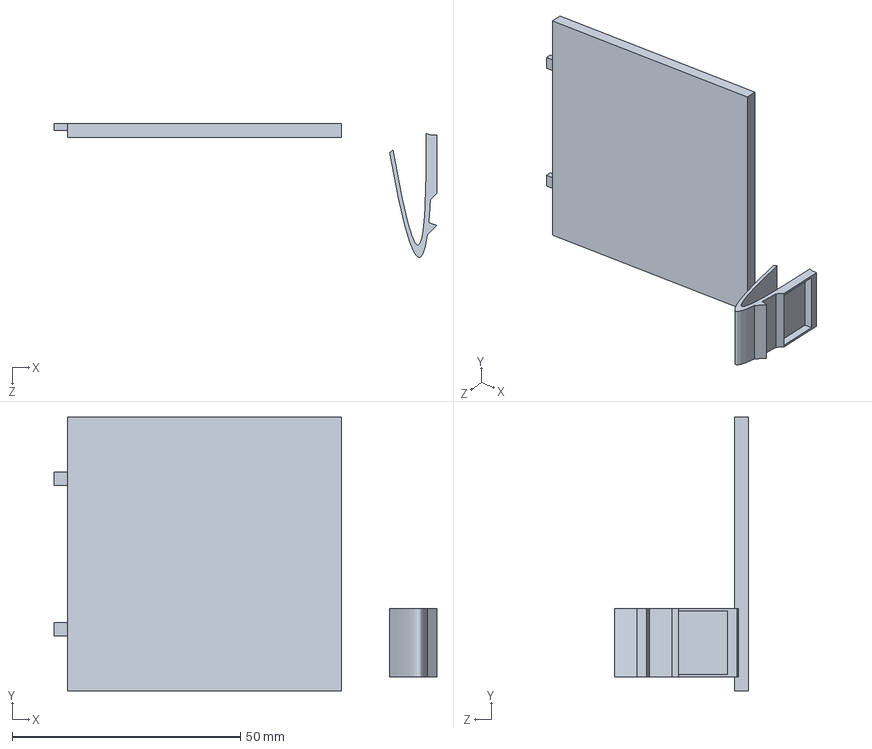
[picture p372: CAD file, 2021-07-25]
Modeles_3D/Solidworks/v2020-2021/BlocsProg1 - Jayson Dauly - Tino Da Costa - Charles Favier/Grand projet PIECE/toit.SLDPRT
84.0 x 60.0 x 29.3 mm
