LibrEduc/RobotBlocs/Modeles_3D/Solidworks/v2020-2021/BlocsProg2 - Emile Mesnage - Quentin Gallot - Corentin Gloaguen/Solidworks/Conception/tube.SLDPRT

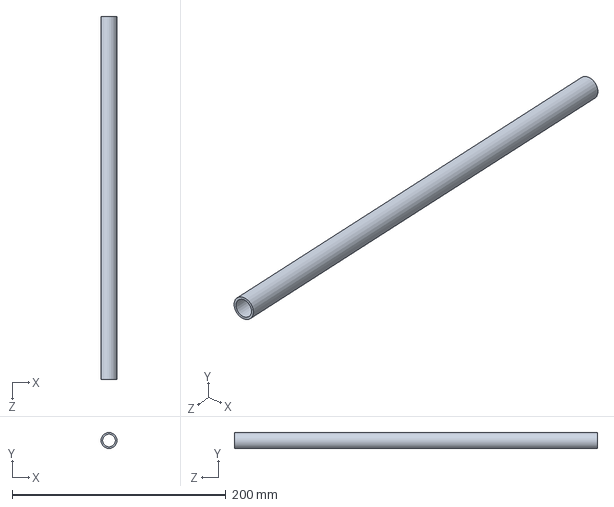
[picture p373: CAD file, 2021-07-25]
Modeles_3D/Solidworks/v2020-2021/BlocsProg2 - Emile Mesnage - Quentin Gallot - Corentin Gloaguen/Solidworks/Conception/tube.SLDPRT
15.0 x 15.0 x 340.0 mm
