LibrEduc/RobotBlocs/Modeles_3D/STL/v2016-2017/roue_d.90.STL

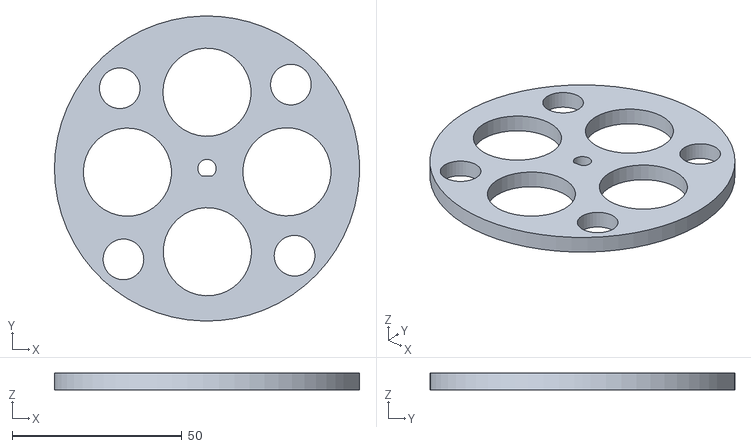
[picture p374: CAD file, 2017-06-28]
Modeles_3D/STL/v2016-2017/roue_d.90.STL
90.0 x 90.0 x 5.00
