LibrEduc/RobotBlocs/Modeles_3D/STL/v2018-2019/Robot - cache_robot^Robot-1.STL

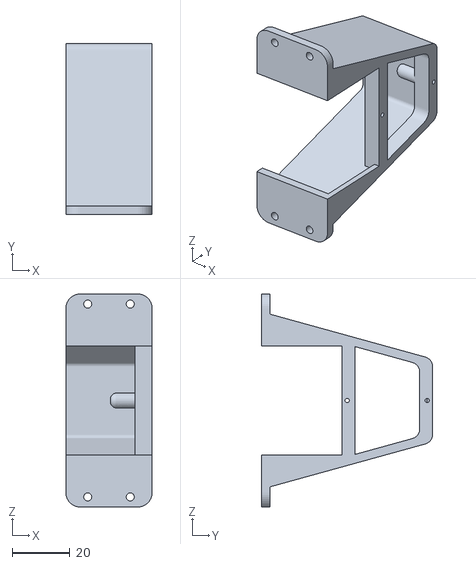
[picture p375: CAD file, 2021-02-01]
Modeles_3D/STL/v2018-2019/Robot - cache_robot^Robot-1.STL
30.0 x 59.5 x 74.0
