LibrEduc/RobotBlocs/Photos_3D_et_fab/v2019-2020/Capture support force resultante.PNG

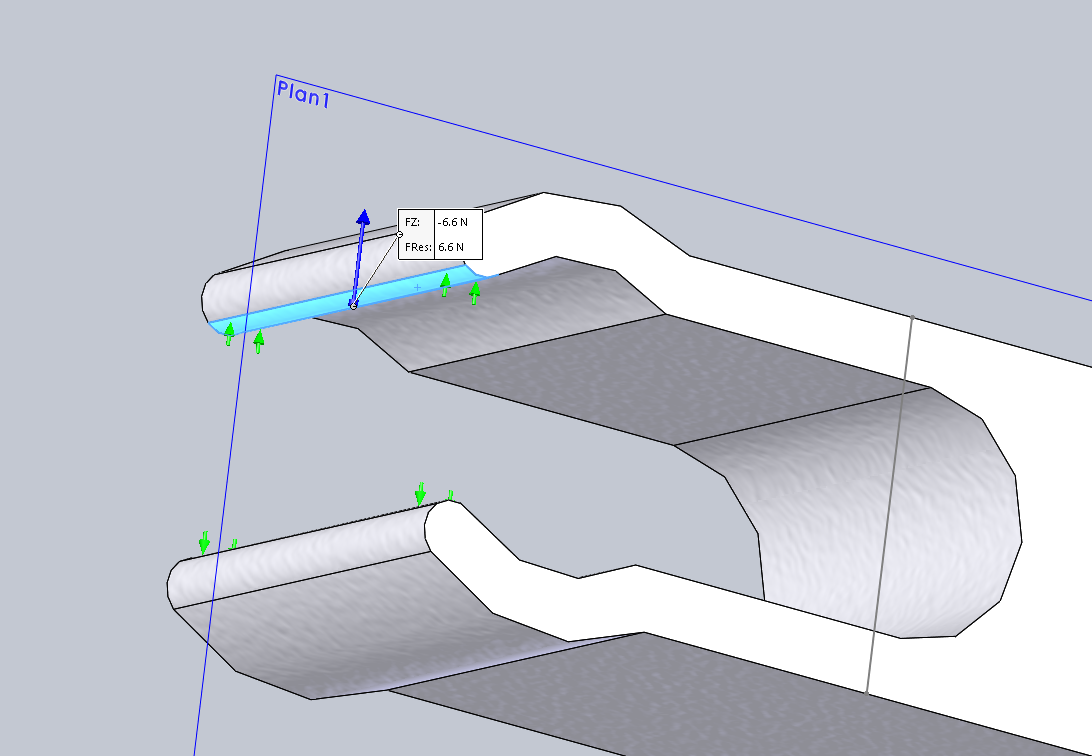
Photos_3D_et_fab/v2019-2020/Capture support force resultante.PNG
