LibrEduc/RobotBlocs/Electronique/SIN_2016-2017/coderobot final/MOTEUR_QUI_MARCHE/FORME.ino

void formeA() {}

void formeB() {}

void formeC() {}

void formeD() {}

void formeE() {}

void formeF() {}

void formeG() {}

void formeH() {}

void formeI() {}

void formeJ() {}

void formeK() {}

void formeL() {}

void formeM() {}

void formeN() {}

void formeO() {}

void formeP() {}
