LibrEduc/RobotBlocs/Electronique/SIN_2016-2017/coderobot final/MOTEUR_QUI_MARCHE/figures.ino

void carre()
{
 toutdroit(800);
 gauche(1030);
 toutdroit(800);
 gauche(1030);
 toutdroit(800);
 gauche(1030);
 toutdroit(800);
}

void triangle()
{
  toutdroit(800);
  gauche(1300);
  toutdroit(800);
  gauche(1300);
  toutdroit(800);
}

void carrepierre()
{
  toutdroit(1600);
  calculangle(90);
droite(pas);
  toutdroit(1600);
droite(pas);
  toutdroit(1600);
droite(pas);
toutdroit(1600);
droite(pas);
}
