LibrEduc/RobotBlocs/Electronique/SIN_2016-2017/coderobot final/robot/formes.ino

void formeA() {
  carre();
}

void formeB() {
  triangle();
}

void formeC() {
  melodie();
}

void formeD() {
  avant();
  }

void formeE() {
  gauchedroite();
  }

void formeF() {
  hexagone();
  }

void formeG() {
  rectangle();
  }

void formeH() {
  losange();
  }

void formeI() {}

void formeJ() {}

void formeK() {}

void formeL() {}

void formeM() {}

void formeN() {}

void formeO() {}

void formeP() {}
