LibrEduc/RobotBlocs/Electronique/SIN_2016-2017/28_01_2017/Moteur_28_01_2017/fonctions.ino

void pas0() {
  digitalWrite(M1NA, 0);
  digitalWrite(M1NB, 0);
  digitalWrite(M2NA, 0);
  digitalWrite(M2NB, 0);
  delay(2000);

}
void pas1() {
  digitalWrite(M1NA, 1);
  digitalWrite(M1NB, 0);
  digitalWrite(M2NA, 1);
  digitalWrite(M2NB, 0);
//delay(courant);
//  digitalWrite(M1NA, 0);
//  digitalWrite(M1NB, 0);
//  digitalWrite(M2NA, 0);
//  digitalWrite(M2NB, 0);
  delay(tempo);

}
void pas2() {
  digitalWrite(M1NA, 0);
  digitalWrite(M1NB, 1);
  digitalWrite(M2NA, 1);
  digitalWrite(M2NB, 0);
//delay(courant);
//  digitalWrite(M1NA, 0);
//  digitalWrite(M1NB, 0);
//  digitalWrite(M2NA, 0);
//  digitalWrite(M2NB, 0);
  delay(tempo);

}
void pas3() {
  digitalWrite(M1NA, 0);
  digitalWrite(M1NB, 1);
  digitalWrite(M2NA, 0);
  digitalWrite(M2NB, 1);
//delay(courant);
//  digitalWrite(M1NA, 0);
//  digitalWrite(M1NB, 0);
//  digitalWrite(M2NA, 0);
//  digitalWrite(M2NB, 0);
  delay(tempo);

}
void pas4() {
  digitalWrite(M1NA, 1);
  digitalWrite(M1NB, 0);
  digitalWrite(M2NA, 0);
  digitalWrite(M2NB, 1);
//delay(courant);
//  digitalWrite(M1NA, 0);
//  digitalWrite(M1NB, 0);
//  digitalWrite(M2NA, 0);
//  digitalWrite(M2NB, 0);
  delay(tempo);

}
