LibrEduc/RobotBlocs/Programmes_Arduino/v2017_2018/Prog_MOT_DRV8833/test/test.ino

#include <Stepper.h>

// change this to the number of steps on your motor
#define STEPS 200

// create an instance of the stepper class, specifying
// the number of steps of the motor and the pins it's
// attached to
Stepper stepper(STEPS, 4, 5, 6, 7);


void setup()
{
  Serial.begin(9600);
  Serial.println("Stepper test!");
  // set the speed of the motor to 30 RPMs
  stepper.setSpeed(70);
}

void loop()
{
  Serial.println("Forward");
  stepper.step(STEPS*2);
  Serial.println("Backward");
  stepper.step(-STEPS);
}
