LibrEduc/RobotBlocs/Electronique/SIN_2016-2017/Doodle_Bot_Text_Demo/Alphabet.pde

// Instructions to generate alphabet

void A()
{
  Turn(-90);Down();Go(4);Turn(45);Go(3);Turn(90);Go(3);Turn(45);Go(4);Up();Go(-3);Turn(-90);Down();Go(-4);Up();Turn(90);Go(3);Turn(-90);Go(6);
}

void B()
{
  Down();Go(3);Turn(-45);Go(1);Turn(-45);Go(1);Turn(-45);Go(1);Turn(-45);Go(3);Up();Turn(90);Go(-3);Down();Go(6);Turn(90);Go(3);Turn(45);Go(1);Turn(45);Go(1);Turn(45);Go(1);Up();Turn(-45);Go(3);Turn(-90);Go(3);
}
  
void C()
{
  Go(3);Turn(-45);Go(1);Turn(-180);Down();Go(1);Turn(45);Go(2);Turn(45);Go(1);Turn(45);Go(4);Turn(45);Go(1);Turn(45);Go(2);Turn(45);Go(1);Up();Turn(45);Go(5);Turn(-90);Go(2);
}
  
void D()
{
  Down();Go(3);Turn(-45);Go(1);Turn(-45);Go(4);Turn(-45);Go(1);Turn(-45);Go(3);Turn(-90);Go(6);Up();Turn(-90);Go(6);
}

void E()
{
  Down();Go(4);Up();Go(-4);Turn(-90);Down();Go(6);Up();Go(-3);Turn(90);Down();Go(3);Up();Go(-3);Turn(-90);Go(3);Turn(90);Down();Go(4);Up();Turn(90);Go(6);Turn(-90);Go(2);
}

void F()
{
  Turn(-90);Down();Go(6);Up();Go(-3);Turn(90);Down();Go(3);Up();Go(-3);Turn(-90);Go(3);Turn(90);Down();Go(4);Up();Turn(90);Go(6);Turn(-90);Go(2);
}

void G()
{
  Go(2);Turn(-90);Go(3);Turn(90);Down();Go(2);Turn(-270);Go(2);Turn(45);Go(1);Turn(45);Go(2);Turn(45);Go(1);Turn(45);Go(4);Turn(45);Go(1);Turn(45);Go(2);Turn(45);Go(1);Up();Turn(-315);Go(5);Turn(-90);Go(2);
}

void H()
{
  Turn(-90);Down();Go(6);Up();Go(-3);Turn(90);Down();Go(4);Up();Turn(-90);Go(3);Down();Go(-6);Up();Turn(90);Go(2);
}

void I()
{
  Go(1);Down();Go(2);Up();Go(-1);Turn(-90);Down();Go(6);Up();Turn(90);Go(-1);Down();Go(2);Up();Turn(90);Go(6);Turn(-90);Go(3);
}

void J()
{
  Turn(-90);Go(2);Turn(180);Down();Go(1);Turn(-45);Go(1);Turn(-45);Go(2);Turn(-45);Go(1);Turn(-45);Go(5);Up();Turn(180);Go(6);Turn(-90);Go(2);
}

void K()
{
  Turn(-90);Down();Go(6);Up();Go(-4);Turn(45);Down();Go(6);Up();Go(-5);Turn(90);Down();Go(4);Up();Turn(-45);Go(2);
}

void L()
{
  Turn(-90);Down();Go(6);Up();Go(-6);Turn(90);Down();Go(4);Up();Go(2);
}

void M()
{
  Turn(-90);Down();Go(6);Turn(135);Go(3);Turn(-90);Go(3);Turn(135);Go(6);Up();Turn(-90);Go(2);
}

void N()
{
  Turn(-90);Down();Go(6);Turn(135);Go(6);Up();Turn(-135);Go(4);Down();Go(-6);Up();Turn(90);Go(2);
}

void O()
{
  Turn(-90);Go(1);Down();Go(4);Turn(45);Go(1);Turn(45);Go(2);Turn(45);Go(1);Turn(45);Go(4);Turn(45);Go(1);Turn(45);Go(2);Turn(45);Go(1);Up();Turn(-135);Go(1);Turn(-90);Go(6);
}

void P()
{
  Turn(-90);Down();Go(6);Turn(90);Go(3);Turn(45);Go(1);Turn(45);Go(1);Turn(45);Go(1);Turn(45);Go(3);Up();Turn(-90);Go(3);Turn(-90);Go(6);
}

void Q()
{
  Go(4);Turn(-90);Go(2);Turn(-135);Down();Go(3);Turn(45);Go(1);Turn(45);Go(1);Turn(45);Go(4);Turn(45);Go(1);Turn(45);Go(2);Turn(45);Go(1);Turn(45);Go(3);Up();Turn(90);Go(2);Turn(-135);Down();Go(3);Up();Turn(-45);Go(2);
}

void R()
{
  Turn(-90);Down();Go(6);Turn(90);Go(3);Turn(45);Go(1);Turn(45);Go(1);Turn(45);Go(1);Turn(45);Go(3);Up();Go(-1);Turn(-135);Down();Go(4);Up();Turn(-45);Go(2);
}

void S()
{
  Turn(-90);Go(1);Turn(135);Down();Go(1);Turn(-45);Go(2);Turn(-45);Go(1);Turn(-45);Go(1);Turn(-45);Go(1);Turn(-45);Go(2);Turn(45);Go(1);Turn(45);Go(1);Turn(45);Go(1);Turn(45);Go(2);Turn(45);Go(1);Up();Turn(-315);Go(5);
  Turn(-90);Go(2);
}

void T()
{
  Go(2);Turn(-90);Down();Go(6);Up();Turn(90);Go(-2);Down();Go(4);Up();Turn(90);Go(6);Turn(-90);Go(2);
}

void U()
{
  Turn(-90);Go(6);Turn(180);Down();Go(5);Turn(-45);Go(1);Turn(-45);Go(2);Turn(-45);Go(1);Turn(-45);Go(5);Up();Go(-6);Turn(90);Go(2);
}

void V()
{
  Turn(-90);Go(6);Turn(180);Down();Go(1);Turn(-33);Go(6);Turn(-38);Go(6);Turn(-33);Go(1);Up();Turn(180);Go(6);Turn(-90);Go(2);
}

void W()
{
  Turn(-90);Go(6);Turn(180);Down();Go(4);Turn(-33);Go(2);Turn(-37);Go(2);Turn(37);Go(2);Turn(-37);Go(2);Turn(-33);Go(4);Up();Turn(180);
  Go(6);Turn(-90);Go(2); 
}

void X()
{
  Turn(-90);Down();Go(1);Turn(45);Go(6);Turn(-45);Go(1);Up();Turn(-90);Go(4);Turn(-90);Down();Go(1);Turn(-45);Go(6);Turn(45);Go(1);
  Up();Turn(-90);Go(2);
}

void Y()
{
  Go(2);Turn(-90);Down();Go(3);Turn(-45);Go(3);Turn(45);Go(1);Up();Turn(90);Go(4);Turn(90);Down();Go(1);Turn(45);Go(3);Up();Turn(-45);
  Go(3);Turn(-90);Go(4);
}

void Z()
{
  Turn(-90);Go(6);Turn(90);Down();Go(4);Turn(90);Go(1);Turn(45);Go(6);Turn(-45);Go(1);Turn(-90);Go(4);Up();Go(2);
}
