LibrEduc/RobotBlocs/Electronique/SIN_2016-2017/28_01_2017/Moteur_28_01_2017/test_moteur.ino

/*void tuto() {

  for (int i = 0; i < 50; i++) {
    digitalWrite(M1NA, 1);
    digitalWrite(M1NB, 0);
    digitalWrite(M2NA, 1);
    digitalWrite(M2NB, 0);
    delay(tempo);
    digitalWrite(M1NA, 0);
    digitalWrite(M1NB, 1);
    digitalWrite(M2NA, 1);
    digitalWrite(M2NB, 0);
    delay(tempo);

    digitalWrite(M1NA, 0);
    digitalWrite(M1NB, 1);
    digitalWrite(M2NA, 0);
    digitalWrite(M2NB, 1);
    delay(tempo);
    digitalWrite(M1NA, 1);
    digitalWrite(M1NB, 0);
    digitalWrite(M2NA, 0);
    digitalWrite(M2NB, 1);
    delay(tempo);
  }

  digitalWrite(M1NA, 0);
  digitalWrite(M1NB, 0);
  digitalWrite(M2NA, 0);
  digitalWrite(M2NB, 0);
  delay(2000);

  for (int b = 0; b < 200; b++) {
    digitalWrite(M1NA, 0);
    digitalWrite(M1NB, 1);
    digitalWrite(M2NA, 0);
    digitalWrite(M2NB, 1);
    delay(tempo);
    digitalWrite(M1NA, 0);
    digitalWrite(M1NB, 1);
    digitalWrite(M2NA, 1);
    digitalWrite(M2NB, 0);
    delay(tempo);
    digitalWrite(M1NA, 1);
    digitalWrite(M1NB, 0);
    digitalWrite(M2NA, 1);
    digitalWrite(M2NB, 0);
    delay(tempo);
    digitalWrite(M1NA, 1);
    digitalWrite(M1NB, 0);
    digitalWrite(M2NA, 0);
    digitalWrite(M2NB, 1);
    delay(tempo);
  }

  digitalWrite(M1NA, 0);
  digitalWrite(M1NB, 0);
  digitalWrite(M2NA, 0);
  digitalWrite(M2NB, 0);
  delay(2000);
}*/
