LibrEduc/RobotBlocs/Electronique/SIN_2016-2017/Doodle_Bot_Text_Demo/Numbers.pde

// Instructions to generate the numbers 0-9

void N0()
{
  Turn(-90);Go(1);Down();Go(4);Turn(45);Go(1);Turn(45);Go(2);Turn(45);Go(1);Turn(45);Go(4);Turn(45);Go(1);Turn(45);Go(2);Turn(45);Go(1);Turn(90);Go(5);Up();Go(-5);Turn(-225);Go(1);Turn(-90);Go(6);
}

void N1()
{
  Down();Go(2);Up();Go(-1);Turn(-90);Down();Go(6);Turn(-39);Go(2);Up();Go(-2);Turn(39);Go(-6);Turn(90);Go(3);
}

void N2()
{
  Turn(-90);Go(5);Down();Turn(45);Go(1);Turn(45);Go(2);Turn(45);Go(1);Turn(45);Go(1);Turn(45);Go(6);Turn(-135);Go(4);Up();Go(2);
}

void N3()
{
  Turn(-90);Go(5);Turn(45);Down();Go(1);Turn(45);Go(2);Turn(45);Go(1);Turn(45);Go(1);Turn(45);Go(1);Turn(45);Go(2);Up();Turn(-180);Go(2);Down();Turn(45);Go(1);Turn(45);Go(1);Turn(45);Go(1);Turn(45);Go(2);
  Turn(45);Go(1);Up();Turn(-135);Go(1);Turn(-90);Go(6);
}

void N4()
{
  Go(3);Turn(-90);Down();Go(6);Turn(-135);Go(4);Turn(-45);Go(1);Turn(-90);Go(4);Up();Turn(90);Go(2);Turn(-90);Go(2);
}
  
void N5()
{
  Turn(-90);Go(1);Turn(135);Down();Go(1);Turn(-45);Go(2);Turn(-45);Go(1);Turn(-45);Go(2);Turn(-45);Go(1);Turn(-45);Go(3);Turn(90);Go(2);Turn(90);Go(4);Up();Turn(90);Go(6);Turn(-90);Go(2);
}

void N6()
{
  Go(4);Turn(-90);Go(5);Turn(-45);Down();Go(1);Turn(-45);Go(2);Turn(-45);Go(1);Turn(-45);Go(4);Turn(-45);Go(1);Turn(-45);Go(2);Turn(-45);Go(1);Turn(-45);Go(2);Turn(-45);Go(1);Turn(-45);Go(2);Turn(-45);Go(1);Up();
  Turn(-45);Go(3);Turn(-90);Go(6);
}
  
void N7()
{
  Go(2);Turn(-35);Down();Go(6);Turn(-37);Go(4);Up();Turn(-90);Go(6);Turn(-90);Go(6);
}

void N8()
{
  Go(1);Down();Go(2);Turn(-45);Go(1);Turn(-45);Go(1);Turn(-45);Go(1);Turn(-45);Go(2);Turn(45);Go(1);Turn(45);Go(1);Turn(45);Go(1);Turn(-315);Go(2);
  Turn(45);Go(1);Turn(45);Go(1);Turn(45);Go(1);Up();Turn(45);Go(2);Turn(-45);Down();Go(1);Turn(-45);Go(1);Turn(-45);Go(1);Up();Turn(-45);Go(5);
}

void N9()
{
  Turn(-90);Go(1);Turn(135);Down();Go(1);Turn(-45);Go(2);Turn(-45);Go(1);Turn(-45);Go(4);Turn(-45);Go(1);Turn(-45);Go(2);Turn(-45);Go(1);Turn(-45);
  Go(2);Turn(-45);Go(1);Turn(-45);Go(2);Turn(-45);Go(1);Up();Turn(135);Go(3);Turn(-90);Go(2);
}
